Z3r0shin/ambersong/docs/human/hardware-bible/13b-tube-radio.md

## 13.6 The 455 kHz AM IF and AM detector

In SW and AM, the converter (V3, section 13.7) sends its 455 kHz IF through the **first AM IF
transformer** (L11) to the first IF amplifier (V4), the tube the FM path also uses (section 13.4). From
V4 the IF goes through the **second AM IF transformer** (L13) to the **AM detector**: the two diodes
inside V6, a 12AV6. The detector recovers the audio from the IF and also makes the **AVC** voltage, which
sets the gain of V4 and, in AM, of the converter (section 13.1.5).

### 13.6.1 How it is joined

**First AM IF transformer (L11).** One end of its primary (terminal B) is on the converter's plate (V3
pin 5). The other end (terminal P) is on the AM supply, `AM_B`, together with the converter's screen
grids (V3 pin 6). The mode switch's B+ unit (S1D) puts B+ on `AM_B` in SW and AM only (section 13.1.6).
**No capacitor is on `AM_B`.** SAMS shows a 0.002 µF bypass there; this radio has none.

**Into V4.** The secondary of L11 is in series with the secondary of the first FM IF transformer (L10):
one end (terminal G) joins L10's secondary, and the other end (terminal E) is on the **AVC line**. V4's
control grid (pin 1) is at the far end of L10's secondary, so it returns to the AVC line through both
secondaries (section 13.4.1).

**Out of V4.** V4's plate feeds the primary of the second FM IF transformer (L12), then, in series, the
primary of the second AM IF transformer (L13). The far end of L13's primary shares a point with V4's
screen grid (pin 6). The **AM IF screen supply resistor** (R13, 1 kΩ) feeds that point from the B+
filter (`B115_A`, section 13.10), and its bypass capacitor (C29, 0.01 µF) joins it to the chassis. So
L13 and V4 have B+ in every position of the mode switch.

**Detector.** One end of L13's secondary (terminal G) goes to **both diode plates** of V6, pins 5 and 6.
The diodes' cathode is pin 2, which V6's triode shares, and it is on the chassis. The other end of the
secondary (terminal E) is the **detector load point**. From there:

- the detector IF bypass capacitor (C31, 100 pF) goes to the chassis;
- the detector load resistor (R15, 50 kΩ) leads to the **AM audio point**.

**AM audio point.** Three parts leave it: the detector DC return resistor (R16, 1 MΩ) and the audio IF
bypass capacitor (C32, 100 pF), both to the chassis, and the **AVC feed resistor** (R17, 2 MΩ) to the
AVC line. The AM audio goes to the SW and AM contacts of the mode switch's audio unit (S1B), whose common
feeds the top of the radio's volume control (section 13.8).

**AVC line.** It joins five things: the far end of the AVC feed resistor (R17), terminal E of L11's
secondary, one end of the AM loopstick (L7), one side of the AM antenna trimmer (C23A), and the **AVC
bypass capacitor** (C24, 0.05 µF), whose other side is on the chassis. In AM the converter's signal grid
returns to this line through the loopstick (section 13.7).

**Cans.** The cans of L11 and L13 are on the chassis.

How the stage is joined (simplified).

### 13.6.2 Parts

The stage's parts, with their fitted and original values (section 13.1.3):

| Part | Fitted | Original | Notes |
|---|---|---|---|
| First AM IF transformer (L11) | IF can, 455 kHz | factory: AM IF (A); SAMS: 455 kHz | SAMS DCR: primary 22 Ω, secondary 22 Ω. Not retuned. |
| Second AM IF transformer (L13) | IF can, 455 kHz | factory: AM IF (B); SAMS: 455 kHz | SAMS DCR: primary 22 Ω, secondary 20 Ω. Not retuned. Its secondary feeds V6's diodes. |
| AM IF screen supply resistor (R13) | 1 kΩ | same | Feeds the far end of L13's primary and V4's screen. |
| AM IF screen supply bypass capacitor (C29) | 0.01 µF | same | |
| Detector IF bypass capacitor (C31) | 100 pF | same | |
| Detector load resistor (R15) | 50 kΩ | same | |
| Detector DC return resistor (R16) | 1 MΩ | same | |
| Audio IF bypass capacitor (C32) | 100 pF | same | |
| AVC feed resistor (R17) | 2 MΩ | same | |
| AVC bypass capacitor (C24) | 0.05 µF | 0.05 µF (factory and SAMS); SAMS: 50 V | No fitted voltage rating recorded. |
| AM detector (V6's two diodes) | 12AV6, new old stock | 12AV6 | The whole tube is in section 13.8. |
| Mode switch, audio unit (S1B) | one unit of the mode switch | SAMS part M5 | Section 13.1.6. |

For a replacement AM IF transformer, neither original gives what you need: the windings' coupling and
impedance, the pinout, the internal capacitor values, the bandwidth and the mechanical fit are all
unrecorded. The tuned frequency is 455 kHz.

### 13.6.3 How to check it

- **Coil resistance.** The parts table gives the SAMS DCR figures for L11 and L13, which describe the
  original parts. A DCR is a check for an open winding, not a measure of inductance or tuning.
- **Shared with FM.** An open secondary in L11, or an open primary in L13, also stops V4 on FM
  (section 13.4.4).
- **Tuning.** The AM IF transformers were not retuned when the FM path was tuned (section 13.1.1).
- **Detector.** V6's diode plates are pins 5 and 6, both on the same end of L13's secondary; the cathode,
  pin 2, is on the chassis.

## 13.7 AM and SW input, converter (V3, 12BE6) and the SW and AM local oscillator

V3 is a **pentagrid converter**: one tube with five grids that is both the mixer and the local oscillator
for AM and SW. Its oscillator section runs on its first grid and cathode. The station enters on its third
grid, the **signal grid**. The IF, 455 kHz, leaves from its plate into the first AM IF transformer (L11).
The mode switch picks the input coil and the oscillator coil for each band. The input coil is the
ferrite **loopstick** (a ferrite rod carrying an antenna winding) in AM, and the SW antenna coil in SW.
V3 takes its B+ from `AM_B`, so it works only in SW and AM.

**The external SW antenna terminal (J2) is not fitted; the internal loopstick antenna (L7) is.** Every
other input part is fitted too: the SW coupling capacitor (C21), the SW antenna coil (L6) and its trimmer
(C22A), and the loopstick's trimmer (C23A).

SAMS gives the bands as 540 to 1620 kHz for AM (the loopstick) and 3.5 to 9 MHz for SW (the SW antenna
coil).

The stage has its own **trimmers** and **padders**, the small capacitors that set its alignment and
tracking (section 13.1.3).

### 13.7.1 How it is joined

**SW input.** The SW antenna coupling capacitor (C21) has one lead where the SW antenna terminal (J2)
would be; nothing else is on that lead. Its other lead goes to one end of the primary of the SW antenna
coil (L6); the other end of that primary is on the chassis. One end of L6's secondary is the **SW RF
point**, which the SW antenna trimmer (C22A) joins to the chassis, and which goes to the SW contact of the
mode switch's RF unit (S1C). The other end of the secondary is on the chassis.

**AM input.** One end of the loopstick (L7) is the **AM RF point**, which goes to the AM contact of S1C.
The other end is on the AVC line (section 13.6). The AM antenna trimmer (C23A) sits across the loopstick,
from the AVC line to the AM RF point.

**Signal grid.** The common of S1C, the AM/SW RF tuning section (VC3, whose other side is on the
chassis) and V3's signal grid (pin 7) are one point. In SW, S1C puts the SW RF point on it; in AM, the AM
RF point; in FM and FM-AFC, nothing. So in AM the grid returns to the AVC line through the loopstick,
and in SW it returns to the chassis through the SW coil's secondary.

**Plate and screens.** The plate (pin 5) goes to the primary of the first AM IF transformer (L11). The
screen grids (pin 6) are on `AM_B` with the other end of that primary. No capacitor is on `AM_B`
(section 13.6.1).

**Oscillator grid.** The oscillator grid (pin 1) goes to the chassis through the oscillator grid leak
resistor (R11, 20 kΩ; grid leak: section 13.3.1). The grid also goes through the oscillator feedback
capacitor (C25, 100 pF) to the **oscillator tuning point**.

**Oscillator tuning point.** It joins C25, the AM/SW oscillator tuning section (VC4, whose other side is
on the chassis) and the common of the mode switch's oscillator tank unit (S1F).

- **In SW**, S1F goes through the SW oscillator padder (C26, 0.003 µF) to the top of the SW oscillator
  coil (L9). The SW oscillator trimmer (C22B) joins that top to the chassis.
- **In AM**, S1F goes to a point that the AM oscillator trimmer (C23B) joins to the chassis. From there
  the AM oscillator padder (C27, 350 pF) leads to the top of the AM oscillator coil (L8).

The bottoms of both oscillator coils are on the chassis.

**Cathode.** The cathode (pin 2) goes only to the common of the mode switch's oscillator feedback unit
(S1G). In SW, S1G puts it on the tap of the SW oscillator coil (L9); in AM, on the tap of the AM
oscillator coil (L8). In FM and FM-AFC the cathode is connected to nothing, and the tube has no B+.

**Heater.** The heater is on pins 3 and 4, in the series string (section 13.9).

How the stage is joined (simplified).

### 13.7.2 V3's pins

The table gives each of V3's pins and what it is joined to.

| Pin | What it is | Joined to |
|---|---|---|
| 1 | oscillator grid (grid 1) | grid leak (R11) to chassis; feedback capacitor (C25) to the oscillator tuning point |
| 2 | cathode | oscillator feedback unit (S1G) only: SW oscillator coil's tap in SW, AM oscillator coil's tap in AM |
| 3 | heater | heater string, toward the FM RF tube's heater through a heater choke (L16) |
| 4 | heater | heater string, from the first IF tube's heater; bypass capacitor (C47) to chassis |
| 5 | plate | primary of the first AM IF transformer (L11) |
| 6 | screen grids (grids 2 and 4) | `AM_B`, with the other end of L11's primary |
| 7 | signal grid (grid 3) | RF unit's common (S1C) and the AM/SW RF tuning section (VC3) |

### 13.7.3 Parts

The stage's parts, with their fitted and original values (section 13.1.3):

| Part | Fitted | Original | Notes |
|---|---|---|---|
| Converter tube (V3) | 12BE6 | 12BE6 | |
| SW antenna terminal (J2) | **absent** | factory: antenna terminal with a series coupling capacitor; SAMS: a terminal, no rating | The external SW antenna terminal (J2) is not fitted; the internal loopstick antenna (L7) is. |
| SW antenna coupling capacitor (C21) | 450 pF | same | Several listed substitutes, Sprague among them, are 470 pF. The listed substitutes are DC-rated and give no safety class for an antenna input on a mains-connected chassis. |
| SW antenna coil (L6) | two-winding coil | factory: two-winding SW matching coil; SAMS: DCR 0.3 Ω each winding, band 3.5–9 MHz | Inductance not given. |
| SW antenna trimmer (C22A) | trimmer | no value in either original | Range and dielectric not specified. Part of the band alignment: do not choose one by appearance. |
| AM loopstick (L7) | loopstick | factory: ferrite bar with antenna winding; SAMS: DCR 0.6 Ω, band 540–1620 kHz | Inductance not given. |
| AM antenna trimmer (C23A) | trimmer | no value in either original | As the SW antenna trimmer. |
| AM/SW RF tuning section (VC3) | section of the four-section tuning capacitor | part of SAMS's tuning assembly M2; no range given | Serves both SW and AM. Turns with the other three sections of the tuning capacitor. |
| Mode switch, RF unit (S1C) | one unit of the mode switch | SAMS part M5 | Section 13.1.6. |
| Oscillator grid leak resistor (R11) | 20 kΩ | same | |
| Oscillator feedback capacitor (C25) | 100 pF | same | |
| AM/SW oscillator tuning section (VC4) | section of the four-section tuning capacitor | part of SAMS's tuning assembly M2; no range given | Serves both SW and AM. |
| Mode switch, oscillator tank unit (S1F) | one unit of the mode switch | SAMS part M5 | Section 13.1.6. |
| SW oscillator padder (C26) | 0.003 µF | 0.003 µF (3000 pF), SAMS: ±5 % | A stable, low-loss RF capacitor. The listed substitute is silvered mica, 500 V. The fitted part's type and rating are not recorded. |
| SW oscillator trimmer (C22B) | trimmer | no value in either original | As the SW antenna trimmer. |
| SW oscillator coil (L9) | tapped coil | factory: tapped oscillator coil; SAMS: DCR 0.3 Ω and 0.1 Ω sections | |
| AM oscillator padder (C27) | 350 pF | same | **Do not round it to 330 pF**: the padder sets the tracking. Sprague 5GA-T35 is 350 pF; Aerovox DI-330 and other listed substitutes are not. |
| AM oscillator trimmer (C23B) | trimmer | no value in either original | As the SW antenna trimmer. |
| AM oscillator coil (L8) | tapped coil | factory: tapped oscillator coil; SAMS: DCR 4.6 Ω and 0.9 Ω sections | SAMS: on the listed Merit, Miller and Stancor substitutes, ignore the extra tap. |
| Mode switch, oscillator feedback unit (S1G) | one unit of the mode switch | SAMS part M5 | Section 13.1.6. |

The AVC bypass capacitor (C24) is in section 13.6.

### 13.7.4 How to check it

- **Coil resistance.** SAMS gives these DCRs for the original coils: the SW antenna coil (L6) 0.3 Ω each
  winding; the loopstick (L7) 0.6 Ω; the AM oscillator coil (L8) 4.6 Ω and 0.9 Ω for its two sections;
  the SW oscillator coil (L9) 0.3 Ω and 0.1 Ω. A DCR finds an open winding; it does not measure
  inductance.
- **The mode switch.** With the cord out, the mode switch's RF, oscillator tank and oscillator feedback
  units (S1C, S1F, S1G) each join their common to their SW contact in SW and their AM contact in AM.
  In FM and FM-AFC they join it to nothing (section 13.1.6).
- **Alignment.** The AM and SW path was not retuned when the FM path was (section 13.1.1). No alignment
  figures for the trimmers are recorded.

## 13.8 The audio amplifier (V6, 12AV6, and V7, 50C5), tone switch and output transformer

The audio picked by the mode switch's audio unit (S1B) reaches the top of the radio's **volume
control** (R1). Its wiper drives the triode inside V6, the **first audio amplifier**, which raises the
audio's voltage. V7, a 50C5 **beam power tube** (a tube built to deliver power to a load), is the
**output stage**: it drives the primary of the **output transformer** (T1). A **tone switch** can join one
or two small capacitors from V6's plate to the chassis, which takes some of the treble away. V6 and V7
have B+ in every position of the mode switch.

### 13.8.1 How it is joined

**Volume control (R1).** Its top (pin 1) comes from the common of the audio unit (S1B). Its bottom
(pin 3) is on the chassis. Its wiper (pin 2) goes through the grid coupling capacitor (C38, 0.01 µF) to
V6's triode grid (pin 1). The audio grid leak resistor (R25, 2 MΩ) joins that grid to the chassis.

**V6's triode.** The cathode (pin 2), shared with the AM detector diodes, is on the chassis. The plate
(pin 7) is fed from the B+ filter (`B115_A`) through the audio plate load resistor (R26, 250 kΩ). Three
more parts leave the plate: the audio plate shunt capacitor (C39, 100 pF) to the chassis, the output
coupling capacitor (C42, 0.01 µF) to V7's grid, and the first tone capacitor (C40).

**Tone switch.** The first tone capacitor (C40, 0.002 µF) runs from V6's plate to a point the tone switch
calls LOW. The second tone capacitor (C41, 0.002 µF) runs from LOW to a point called MID. The tone
unit's common is on the chassis. The table shows what each tone position switches in:

| Tone position | What it switches in, from V6's plate to the chassis |
|---|---|
| H (high) | nothing: the H contact is connected to nothing |
| M (medium) | C40 and C41 in series: 0.001 µF |
| L (low) | C40 alone: 0.002 µF |

The factory drawing and SAMS agree on this. SAMS numbers the switch's lugs 13 for the common, 2 for OFF,
3 for H, 4 for M and 5 for L. The letters H, M and L above are the drawing's; no record maps them to the
physical lugs.

**V7.** The control grid (pin 2) takes the audio from C42 and returns to the chassis through the output
grid leak resistor (R27, 500 kΩ). The cathode (pin 1) goes to the chassis through the output cathode
resistor (R28, 150 Ω 1 W); nothing else is on the cathode. The screen grid (pin 6) is on the B+ filter
(`B115_A`). The plate (pin 7) goes to one end of the output transformer's primary (terminal P) and to the
primary shunt capacitor (C43, 0.0047 µF). **Nothing is wired to pin 5.**

**Output transformer (T1).** Its primary has **two terminals and no tap**. Terminal P is on V7's plate.
Terminal B is on `B130`, the first filtered point of the B+ supply (section 13.10), and C43 sits across
the two. The secondary's two leads leave the radio for the ADC (section 13.11).

**SP1 and SP2** are the radio's original speakers as drawn by the factory, in series across the
secondary. In this machine the radio's output feeds the 7.5 Ω load and the ADC, not speakers.

**Heaters.** V6's heater is on pins 3 and 4, V7's on pins 3 and 4, both in the series string
(section 13.9).

How the stage is joined (simplified).

### 13.8.2 V6's and V7's pins

The table gives each pin of both tubes and what it is joined to.

| Pin | V6, 12AV6 | Joined to | V7, 50C5 | Joined to |
|---|---|---|---|---|
| 1 | triode grid | grid coupling capacitor (C38) from the volume wiper; grid leak (R25) to chassis | cathode | output cathode resistor (R28) to chassis |
| 2 | cathode, shared by the triode and both diodes | chassis | control grid | output coupling capacitor (C42); grid leak (R27) to chassis |
| 3 | heater | heater string, toward the first IF tube's heater | heater | heater string, toward the limiter's heater |
| 4 | heater | heater string, from the limiter's heater | heater | the fused live: the start of the heater string |
| 5 | diode plate | second AM IF transformer's secondary (L13), terminal G | second control-grid pin | nothing |
| 6 | diode plate | the same point as pin 5 | screen grid | B+ filter (`B115_A`) |
| 7 | triode plate | plate load (R26) from `B115_A`; C39, C42, C40 | plate | output transformer primary, terminal P; C43 |

The 50C5's published ratings: plate at most 150 V, screen at most 130 V, plate dissipation 7 W, screen
dissipation 1.4 W.
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
