Z3r0shin/ambersong/docs/human/hardware-bible/A-datasheet-limits.md

# Appendix A. Datasheet facts used in this machine

This appendix gathers the makers' figures that matter for this machine: pinouts, limits, addresses and
ratings, part by part. Only the facts the machine uses are here. You need it when you replace a part,
check a reading against a limit, or adapt the design to other parts. The chapters tell you what each
part does; abbreviations are explained in the glossary.
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
