Z3r0shin/ambersong/hardware/STLs/AUDIO - Passive Radiator - Holder.stl

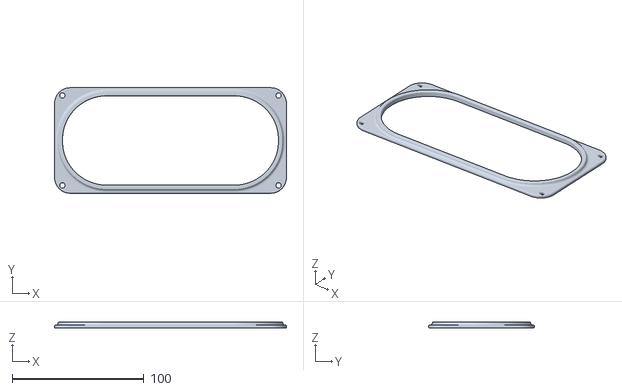
[picture p21: CAD file, 2026-09-28]
hardware/STLs/AUDIO - Passive Radiator - Holder.stl
176.2 x 80.2 x 4.80
