Z3r0shin/ambersong/hardware/STLs/IN - Electronics - LEDITRON Bus Case Bottom.stl

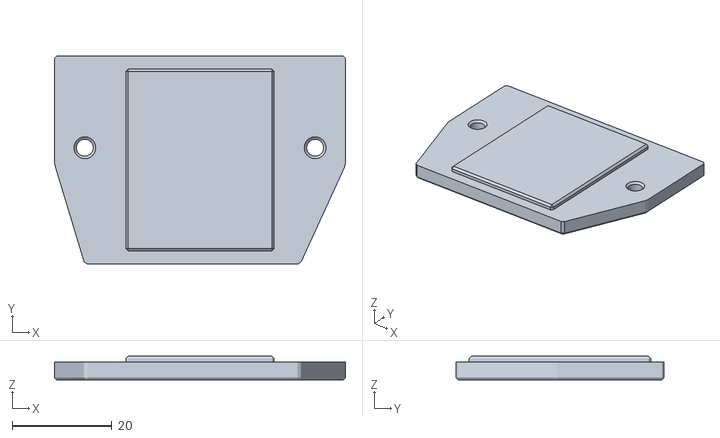
[picture p22: CAD file, 2026-09-28]
hardware/STLs/IN - Electronics - LEDITRON Bus Case Bottom.stl
58.4 x 41.8 x 4.80
