Z3r0shin/ambersong/hardware/STLs/IN - Electronics - Power Detect Case BOTTOM.stl

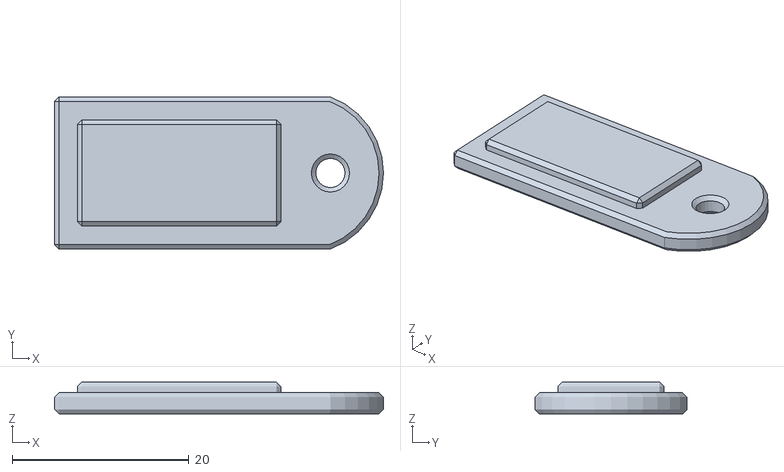
[picture p23: CAD file, 2026-09-28]
hardware/STLs/IN - Electronics - Power Detect Case BOTTOM.stl
37.2 x 17.2 x 3.60
