Z3r0shin/ambersong/hardware/STLs/FRONT - Panel Anchors - Outsidemost.stl

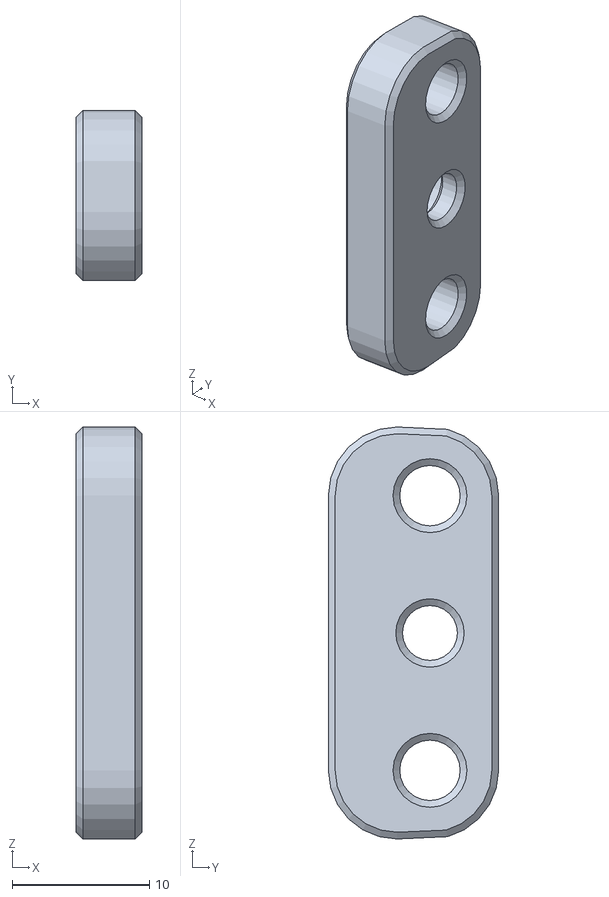
[picture p24: CAD file, 2026-09-28]
hardware/STLs/FRONT - Panel Anchors - Outsidemost.stl
4.80 x 12.4 x 30.0
