Z3r0shin/ambersong/hardware/STLs/IN - Electronics - RDA5807M - Cage Holder.stl

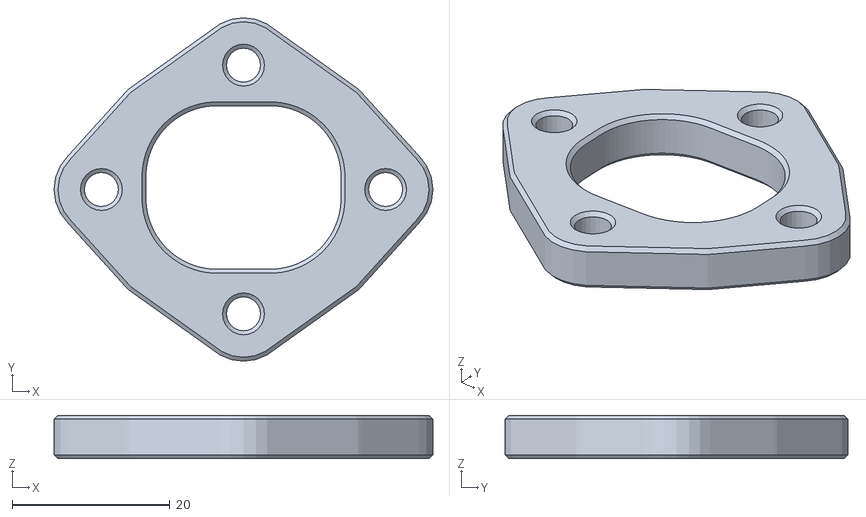
[picture p25: CAD file, 2026-09-28]
hardware/STLs/IN - Electronics - RDA5807M - Cage Holder.stl
48.0 x 43.5 x 5.50
