Z3r0shin/ambersong/hardware/STLs/IN - Electronics - Box Fan LM7812 Case Top.stl

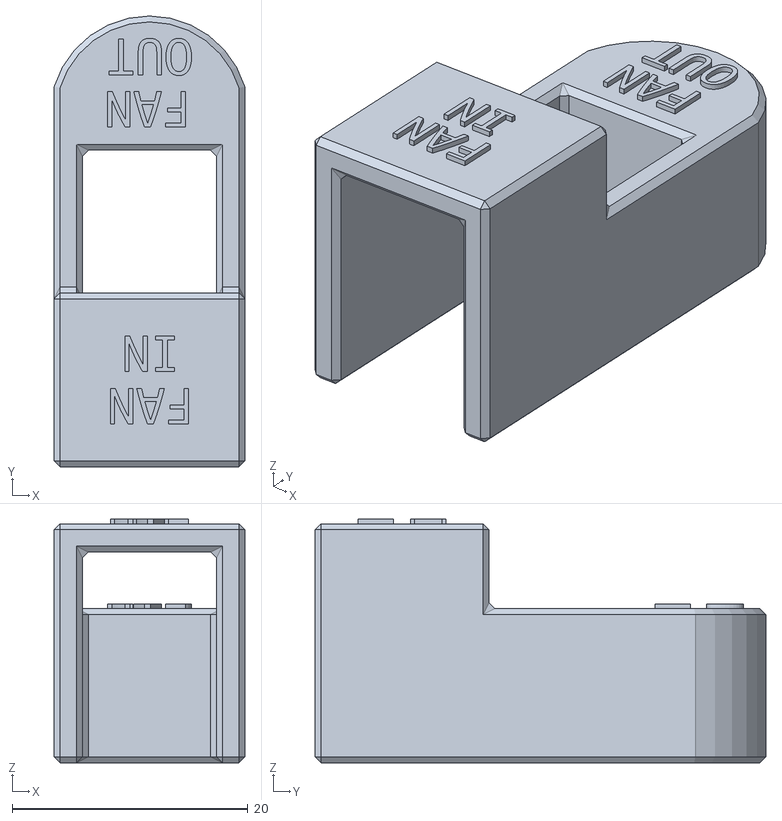
[picture p26: CAD file, 2026-09-28]
hardware/STLs/IN - Electronics - Box Fan LM7812 Case Top.stl
16.2 x 38.3 x 20.7
