Z3r0shin/ambersong/hardware/STLs/BACK - Electronics - BNC Antenna Interface.stl

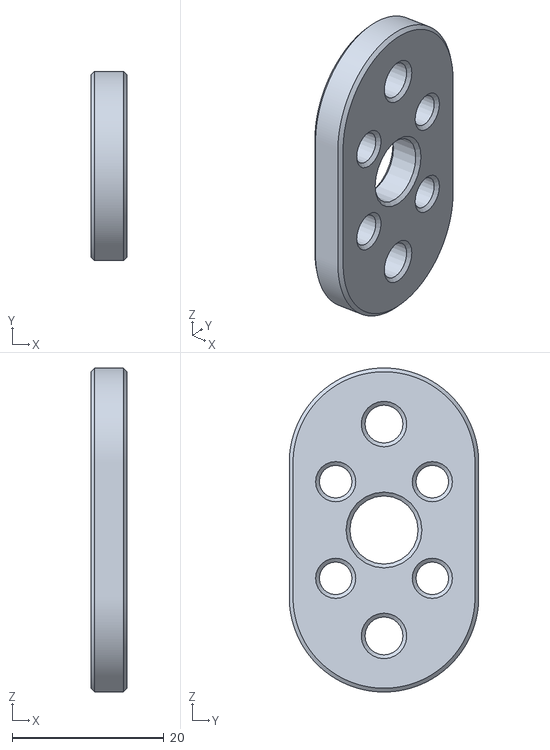
[picture p27: CAD file, 2026-09-28]
hardware/STLs/BACK - Electronics - BNC Antenna Interface.stl
4.80 x 25.0 x 42.7
