Z3r0shin/ambersong/hardware/STLs/LEDITRON - Front Case.stl

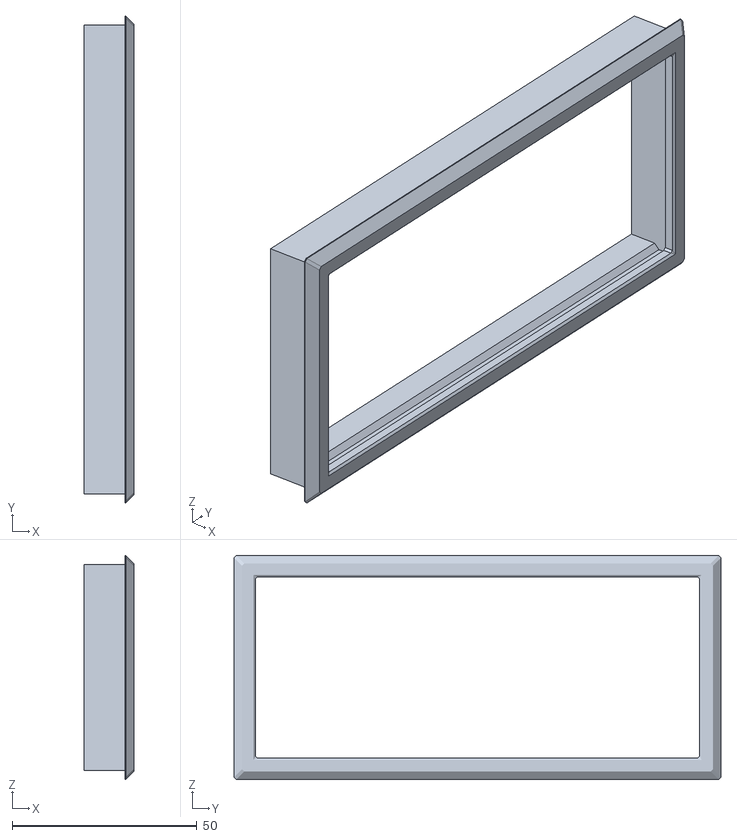
[picture p28: CAD file, 2026-09-28]
hardware/STLs/LEDITRON - Front Case.stl
13.5 x 131.8 x 60.7
