Z3r0shin/ambersong/hardware/STLs/IN - Electronics - Box Fan LM7812 Case Bottom.stl

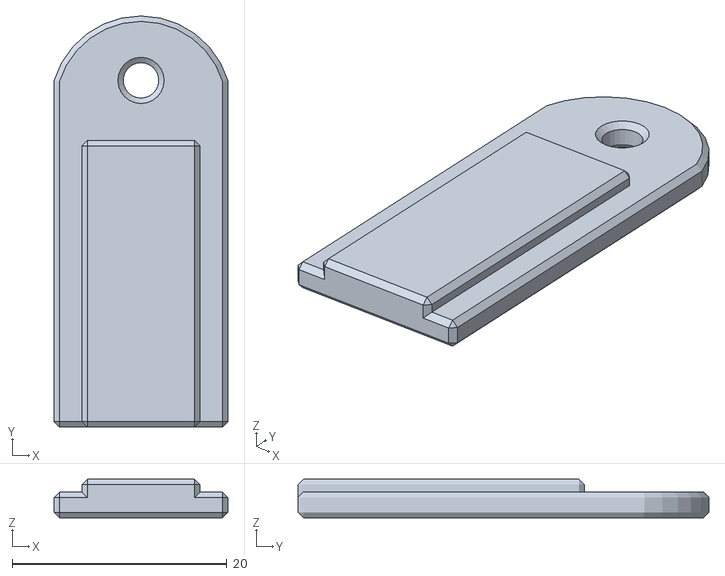
[picture p29: CAD file, 2026-09-28]
hardware/STLs/IN - Electronics - Box Fan LM7812 Case Bottom.stl
16.2 x 38.3 x 3.60
