Z3r0shin/ambersong/hardware/STLs/IN - Electronics - LEDITRON Back.stl

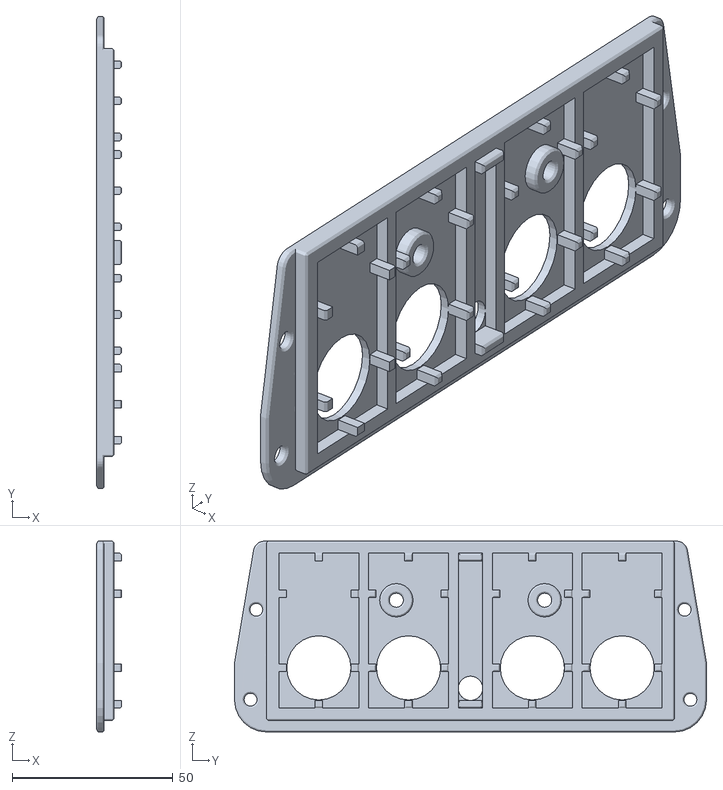
[picture p30: CAD file, 2026-09-28]
hardware/STLs/IN - Electronics - LEDITRON Back.stl
7.81 x 147.0 x 59.5
