Z3r0shin/ambersong/hardware/STLs/LEDITRON - Digit.stl

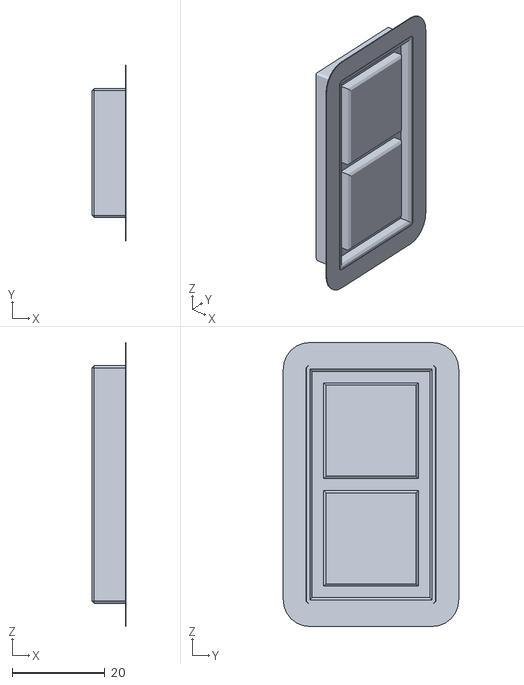
[picture p31: CAD file, 2026-09-28]
hardware/STLs/LEDITRON - Digit.stl
7.40 x 37.8 x 61.1
