Z3r0shin/ambersong/hardware/STLs/AUDIO - Passive Radiator - TPU Membrane.stl

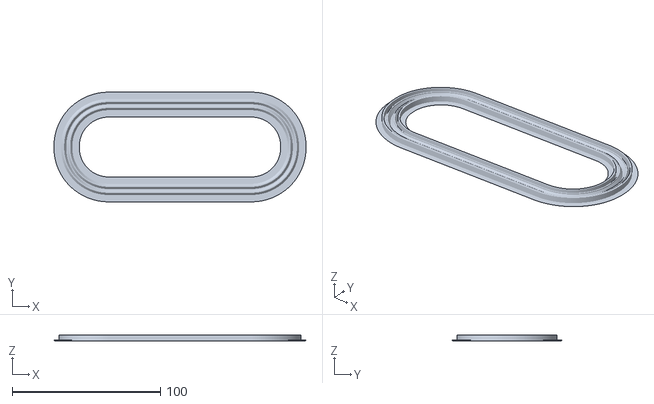
[picture p32: CAD file, 2026-09-28]
hardware/STLs/AUDIO - Passive Radiator - TPU Membrane.stl
170.0 x 74.0 x 4.00
