Z3r0shin/ambersong/hardware/STLs/LEDITRON - Glass Spacer.stl

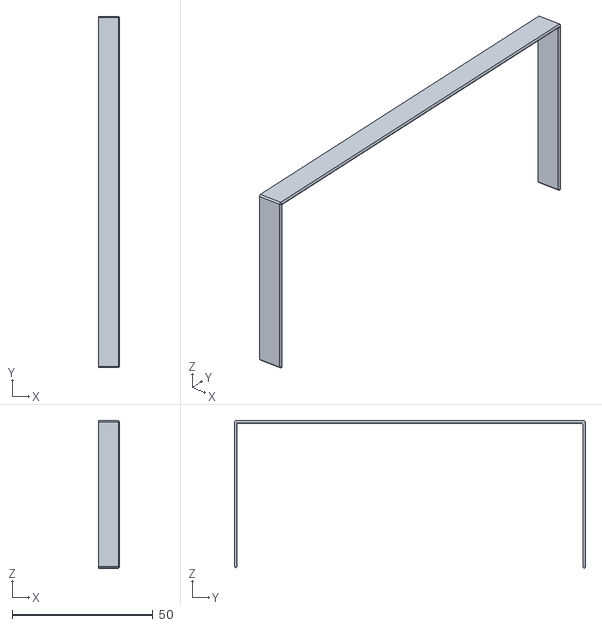
[picture p33: CAD file, 2026-09-28]
hardware/STLs/LEDITRON - Glass Spacer.stl
7.51 x 124.6 x 52.5
