Z3r0shin/ambersong/hardware/STLs/IN - Electronics - Audio MCU Case BOTTOM.stl

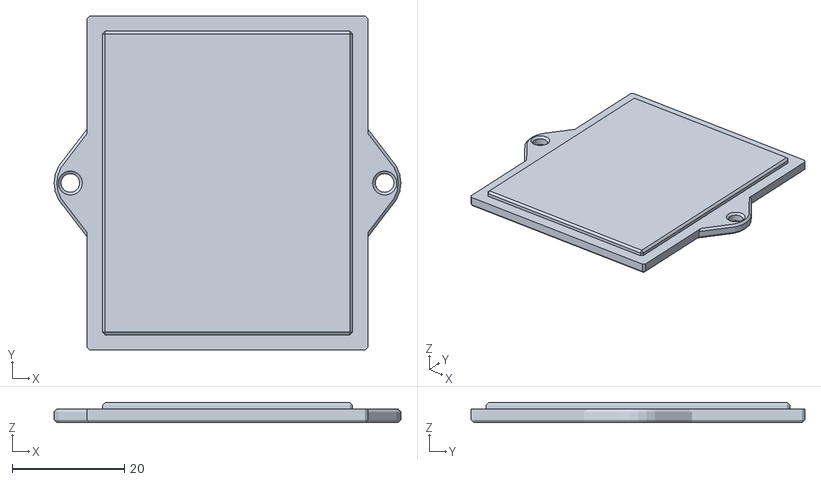
[picture p34: CAD file, 2026-09-28]
hardware/STLs/IN - Electronics - Audio MCU Case BOTTOM.stl
61.7 x 59.4 x 3.60
