Z3r0shin/ambersong/hardware/STLs/IN - Electronics - PCM5102A DAC Case Bottom.stl

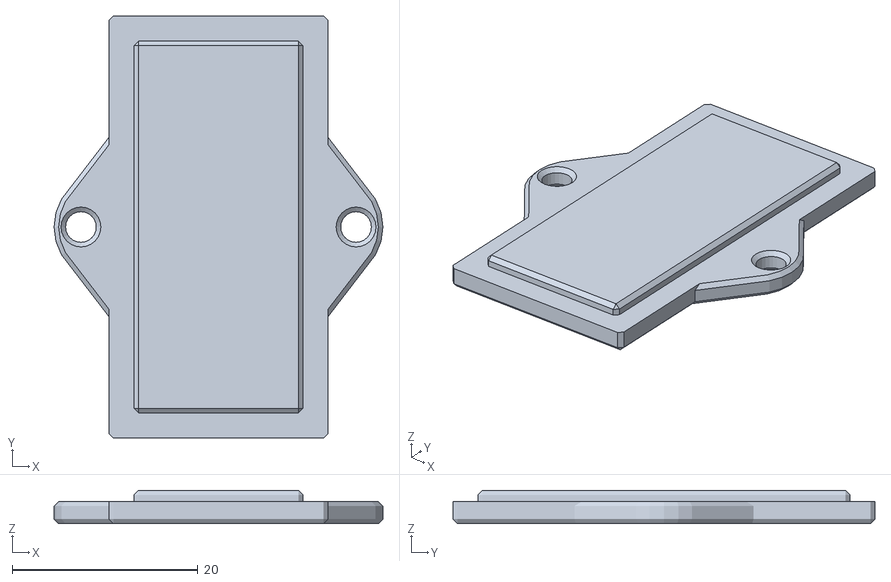
[picture p35: CAD file, 2026-09-28]
hardware/STLs/IN - Electronics - PCM5102A DAC Case Bottom.stl
35.4 x 45.4 x 3.60
