Z3r0shin/ambersong/hardware/STLs/IN - Electronics - 5V PSU Case Bottom.stl

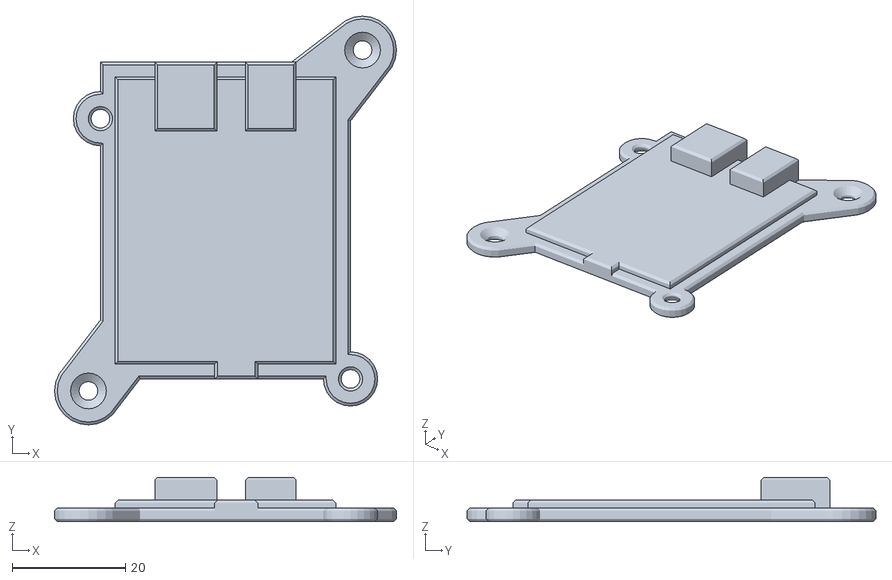
[picture p36: CAD file, 2026-09-28]
hardware/STLs/IN - Electronics - 5V PSU Case Bottom.stl
60.4 x 72.2 x 7.80
