Z3r0shin/ambersong/hardware/STLs/IN - Electronics - RDA5807M - Bottom.stl

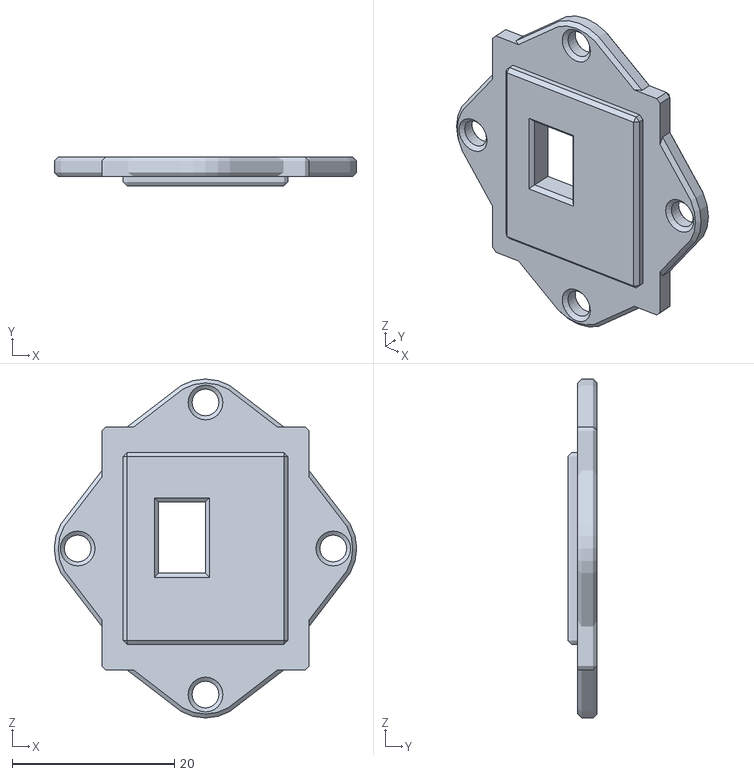
[picture p37: CAD file, 2026-09-28]
hardware/STLs/IN - Electronics - RDA5807M - Bottom.stl
37.3 x 3.60 x 41.8
