Z3r0shin/ambersong/hardware/STLs/IN - Electronics - LEDITRON Bus Case TOP.stl

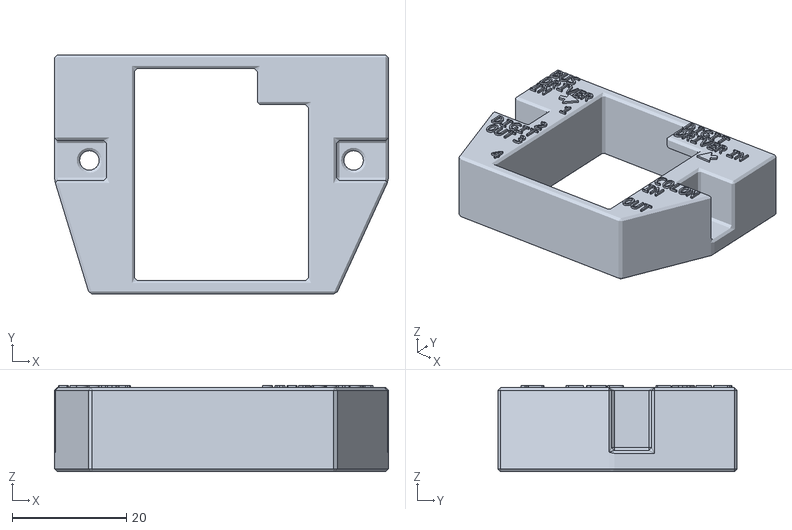
[picture p38: CAD file, 2026-09-28]
hardware/STLs/IN - Electronics - LEDITRON Bus Case TOP.stl
58.4 x 41.8 x 15.1
