Z3r0shin/ambersong/hardware/STLs/IN - Electronics - Stepper Driver ULN2003A Case - Top.stl

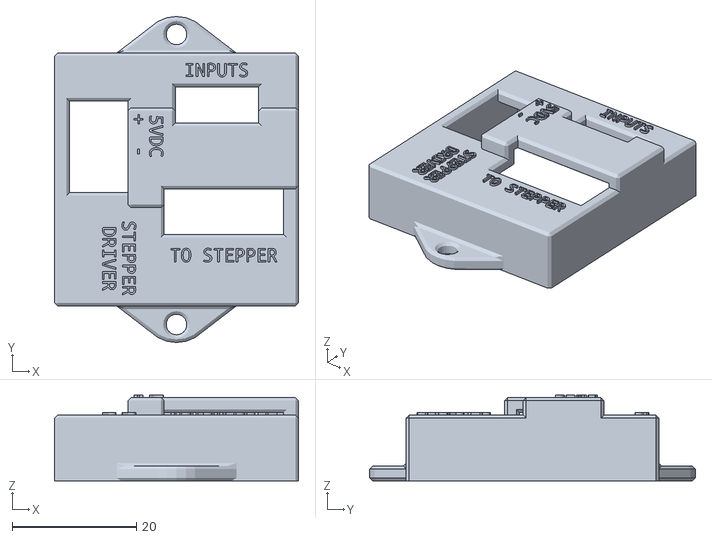
[picture p39: CAD file, 2026-09-28]
hardware/STLs/IN - Electronics - Stepper Driver ULN2003A Case - Top.stl
39.2 x 52.4 x 13.8
