Z3r0shin/ambersong/hardware/STLs/FRONT - FM Dial - Stepper Needle and Magnet Holder.stl

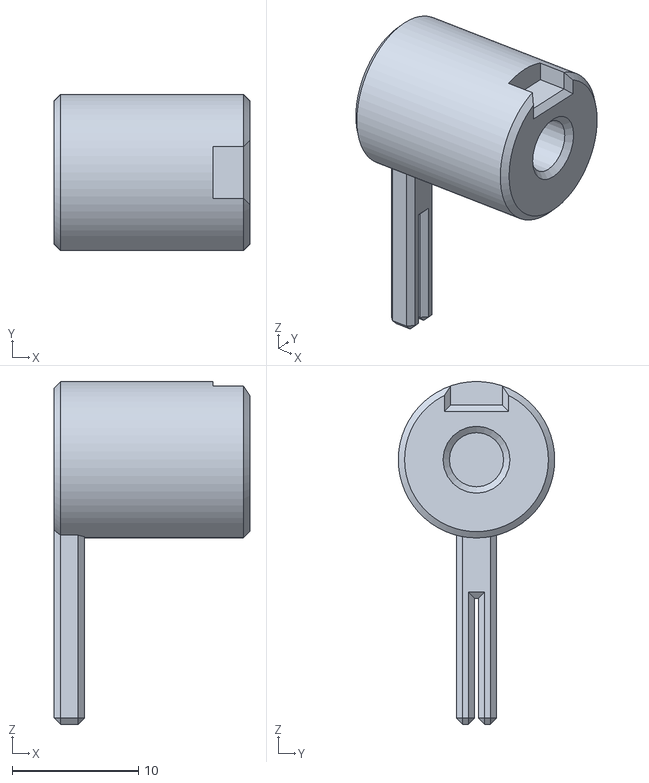
[picture p40: CAD file, 2026-09-28]
hardware/STLs/FRONT - FM Dial - Stepper Needle and Magnet Holder.stl
15.5 x 12.4 x 27.2
