Z3r0shin/ambersong/hardware/STLs/IN - Electronics - AS5600 Case - Top.stl

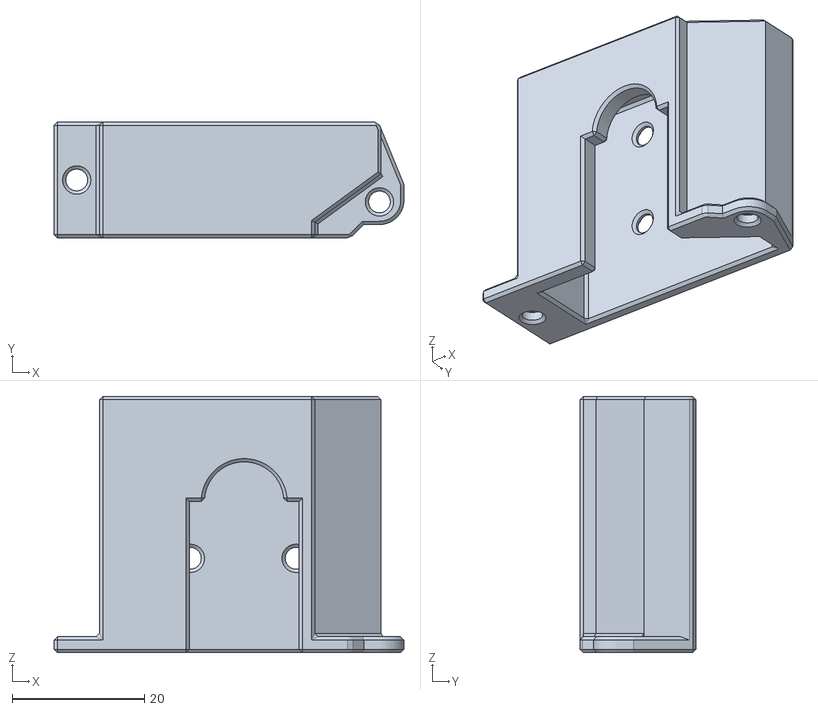
[picture p41: CAD file, 2026-09-28]
hardware/STLs/IN - Electronics - AS5600 Case - Top.stl
53.0 x 17.5 x 38.8
