Z3r0shin/ambersong/hardware/STLs/AUDIO - Passive Radiator - Membrane Weight.stl

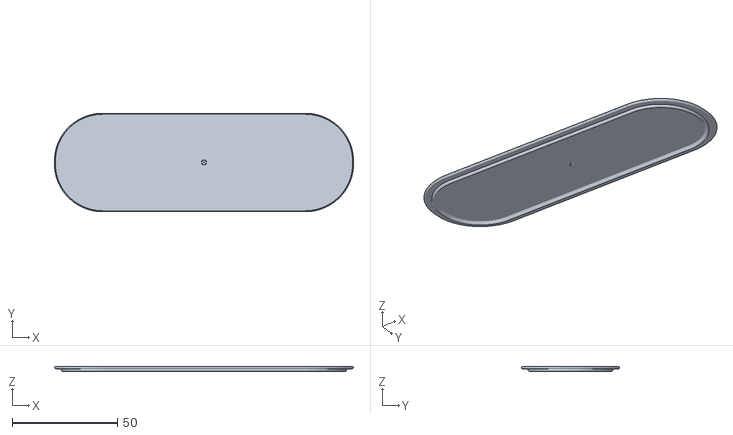
[picture p42: CAD file, 2026-09-28]
hardware/STLs/AUDIO - Passive Radiator - Membrane Weight.stl
142.3 x 46.8 x 2.40
