Z3r0shin/ambersong/hardware/STLs/IN - Electronics - PCM1802 ADC Case BOTTOM.stl

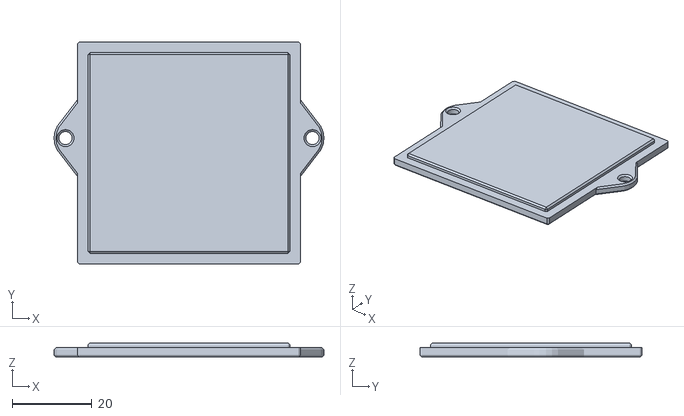
[picture p43: CAD file, 2026-09-28]
hardware/STLs/IN - Electronics - PCM1802 ADC Case BOTTOM.stl
67.9 x 55.9 x 3.60
