Z3r0shin/ambersong/hardware/STLs/IN - Electronics - Stepper Driver ULN2003A Case - Bottom.stl

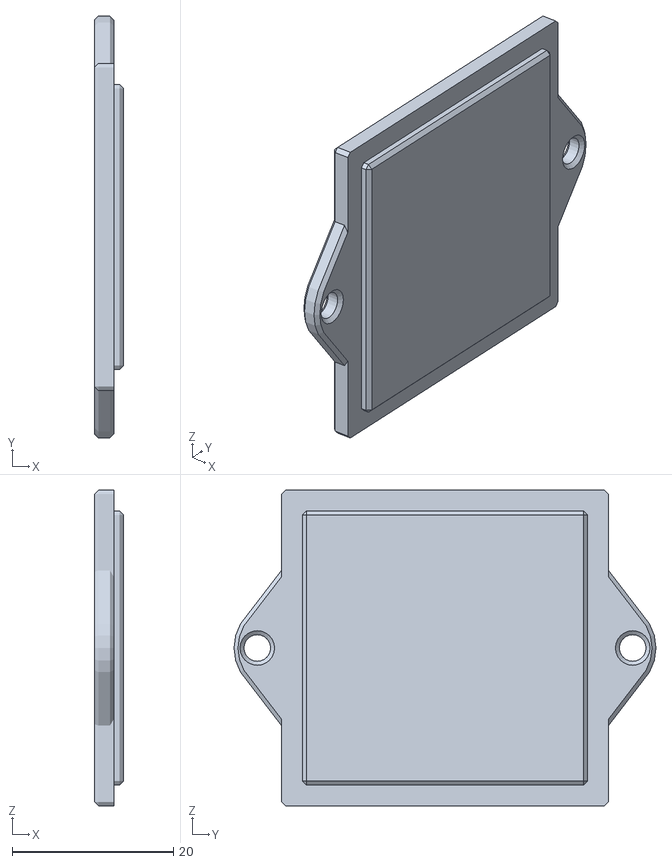
[picture p44: CAD file, 2026-09-28]
hardware/STLs/IN - Electronics - Stepper Driver ULN2003A Case - Bottom.stl
3.60 x 52.4 x 39.2
