Z3r0shin/ambersong/hardware/STLs/IN - Electronics - Audio Listener Case BOTTOM.stl

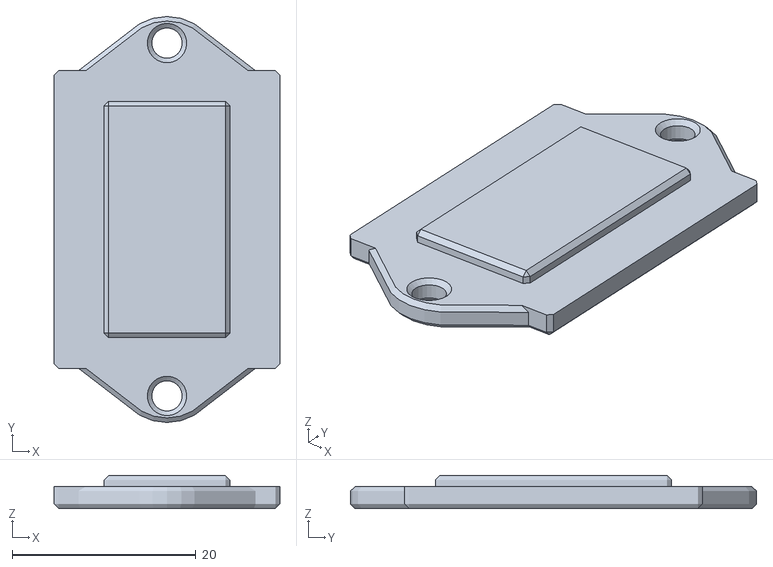
[picture p45: CAD file, 2026-09-28]
hardware/STLs/IN - Electronics - Audio Listener Case BOTTOM.stl
24.5 x 44.2 x 3.60
