Z3r0shin/ambersong/hardware/STLs/IN - Electronics - Digit Drivers Case BOTTOM.stl

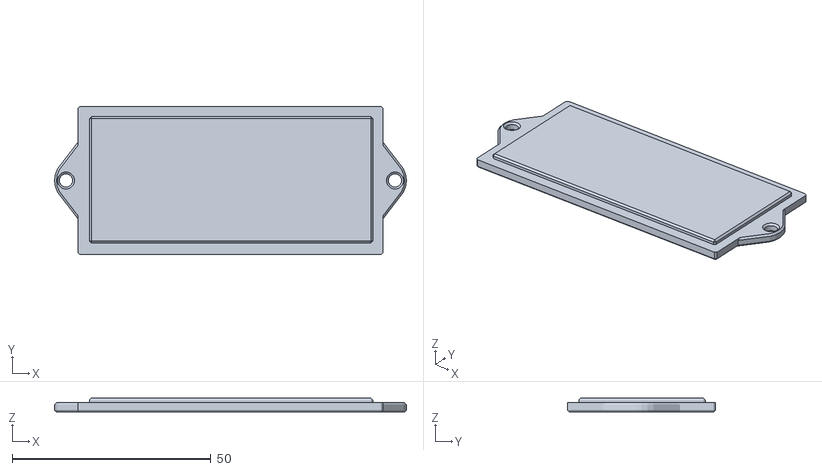
[picture p46: CAD file, 2026-09-28]
hardware/STLs/IN - Electronics - Digit Drivers Case BOTTOM.stl
88.6 x 37.3 x 3.60
