Z3r0shin/ambersong/hardware/STLs/IN - Electronics - Audio Listener Case TOP.stl

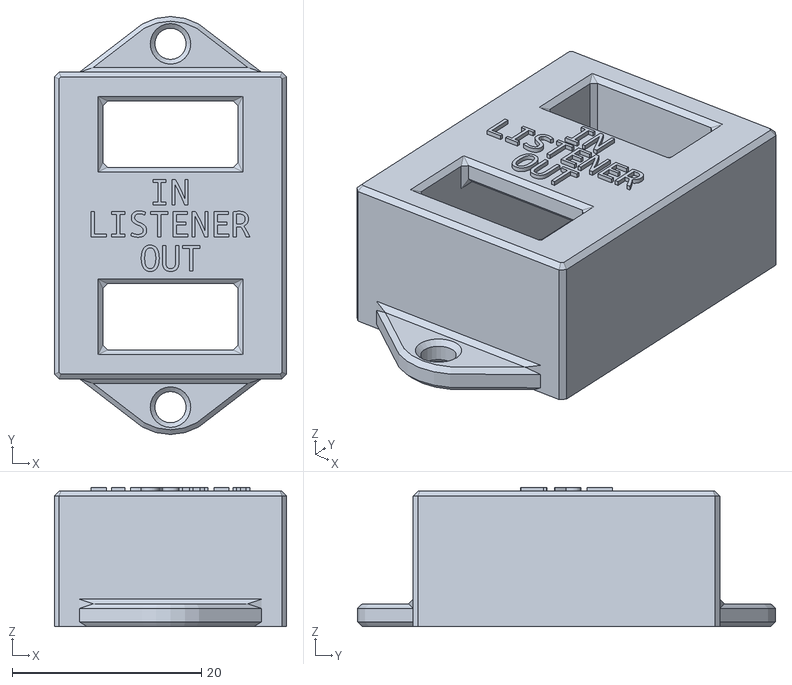
[picture p47: CAD file, 2026-09-28]
hardware/STLs/IN - Electronics - Audio Listener Case TOP.stl
24.6 x 44.2 x 14.7
