Z3r0shin/ambersong/hardware/STLs/LEDITRON - Colon - Blanket.stl

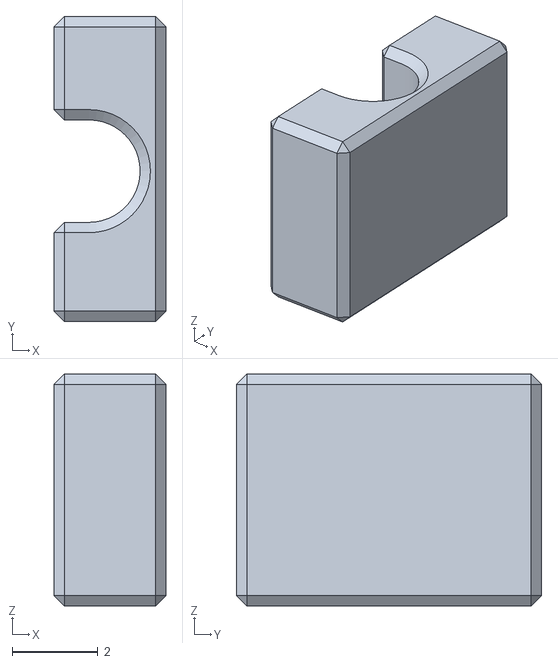
[picture p48: CAD file, 2026-09-28]
hardware/STLs/LEDITRON - Colon - Blanket.stl
2.60 x 7.10 x 5.40
