Z3r0shin/ambersong/hardware/STLs/IN - Electronics - Digit Drivers Case TOP.stl

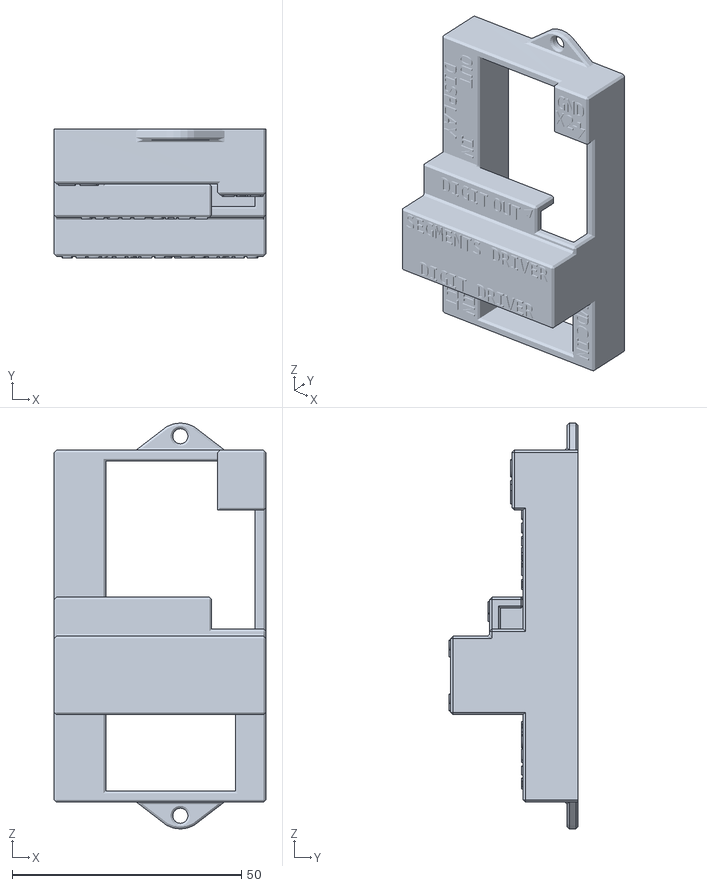
[picture p49: CAD file, 2026-09-28]
hardware/STLs/IN - Electronics - Digit Drivers Case TOP.stl
46.2 x 28.2 x 88.6
