Z3r0shin/ambersong/hardware/STLs/BACK - Fan Exhaust.stl

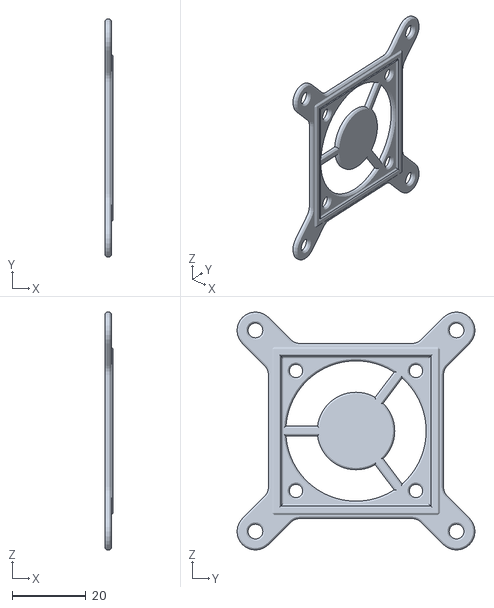
[picture p50: CAD file, 2026-09-28]
hardware/STLs/BACK - Fan Exhaust.stl
2.29 x 64.5 x 64.5
