Z3r0shin/ambersong/hardware/STLs/FRONT - FM Dial - Back.stl

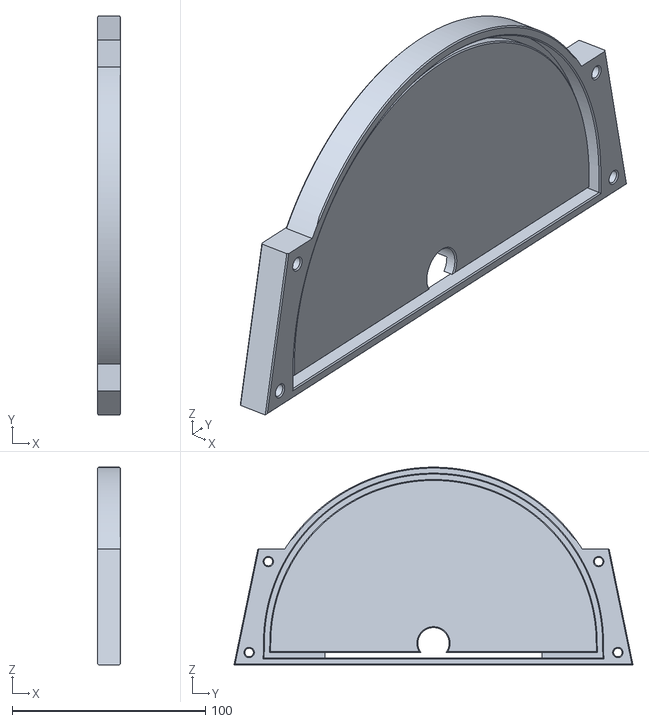
[picture p51: CAD file, 2026-09-28]
hardware/STLs/FRONT - FM Dial - Back.stl
12.0 x 206.7 x 102.4
