Z3r0shin/ambersong/hardware/STLs/IN - Electronics - DS3231 RTC Case BOTTOM.stl

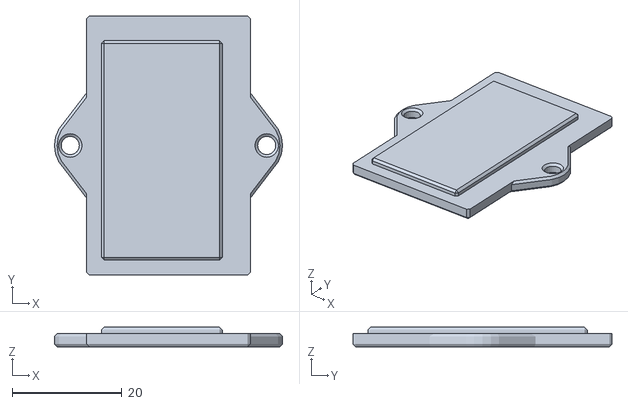
[picture p52: CAD file, 2026-09-28]
hardware/STLs/IN - Electronics - DS3231 RTC Case BOTTOM.stl
41.6 x 47.2 x 3.60
