Z3r0shin/ambersong/hardware/STLs/FRONT - FM Dial - Cover.stl

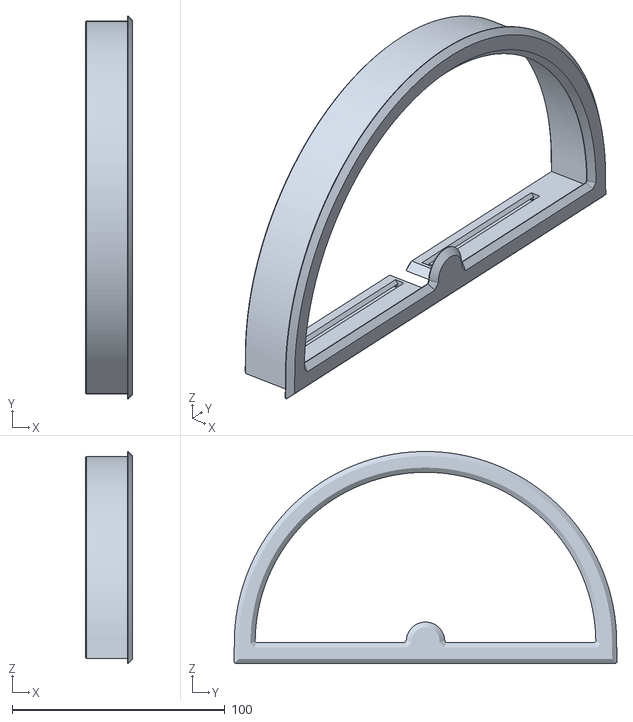
[picture p53: CAD file, 2026-09-28]
hardware/STLs/FRONT - FM Dial - Cover.stl
22.3 x 179.9 x 99.6
