Z3r0shin/ambersong/hardware/STLs/IN - Electronics - Bluetooth LED Holder.stl

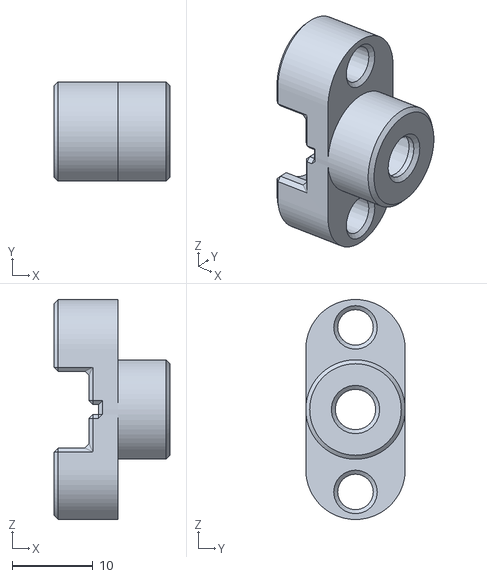
[picture p54: CAD file, 2026-09-28]
hardware/STLs/IN - Electronics - Bluetooth LED Holder.stl
14.3 x 12.3 x 27.2
