Z3r0shin/ambersong/hardware/STLs/IN - Electronics - PCM1802 ADC Case TOP.stl

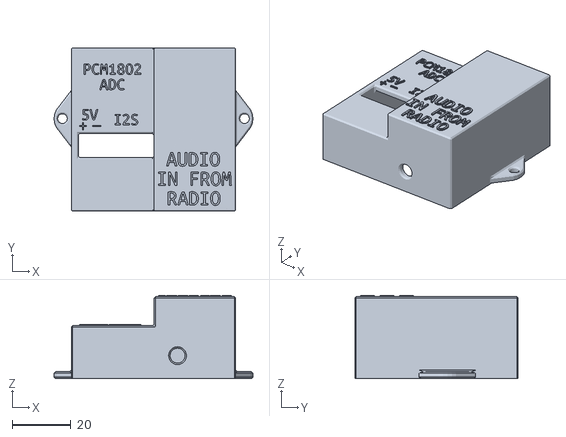
[picture p55: CAD file, 2026-09-28]
hardware/STLs/IN - Electronics - PCM1802 ADC Case TOP.stl
67.9 x 55.8 x 28.4
