Z3r0shin/ambersong/hardware/STLs/IN - Tube Radio - Faraday Cage 1.stl

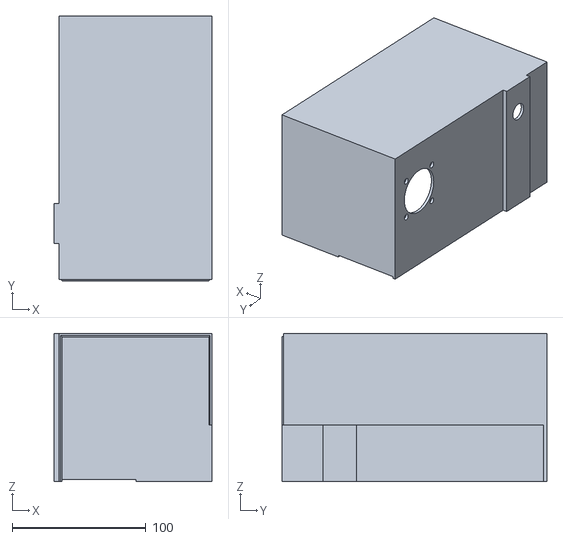
[picture p56: CAD file, 2026-09-28]
hardware/STLs/IN - Tube Radio - Faraday Cage 1.stl
118.0 x 197.7 x 110.7
