Z3r0shin/ambersong/hardware/STLs/IN - Electronics - Hall Sensor Stepper Limit Case.stl

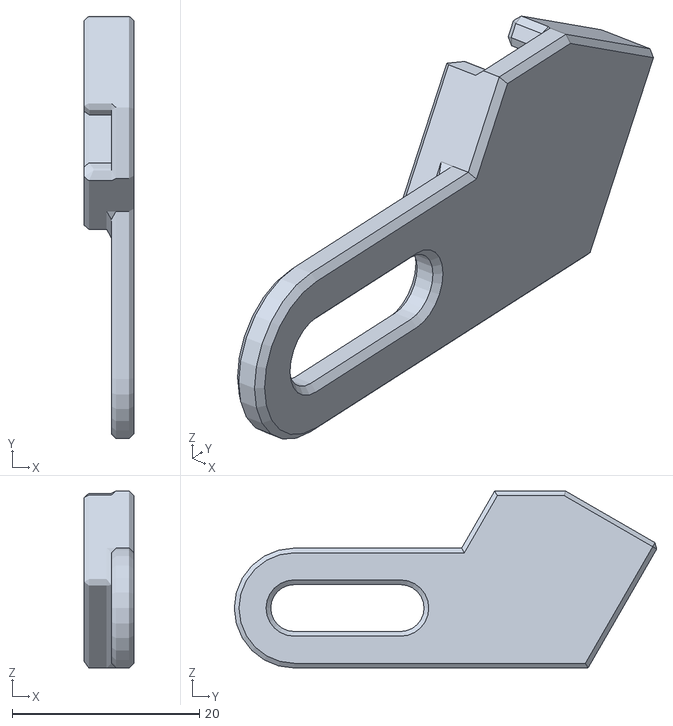
[picture p57: CAD file, 2026-09-28]
hardware/STLs/IN - Electronics - Hall Sensor Stepper Limit Case.stl
5.30 x 45.1 x 18.9
