Z3r0shin/ambersong/hardware/STLs/AUDIO - Speakers Holder and Seal.stl

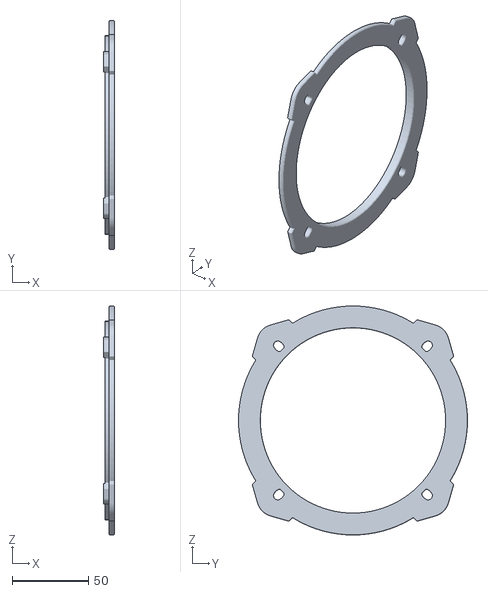
[picture p58: CAD file, 2026-09-28]
hardware/STLs/AUDIO - Speakers Holder and Seal.stl
7.50 x 150.6 x 150.6
