Z3r0shin/ambersong/hardware/STLs/IN - Electronics - Backing Panel 1.stl

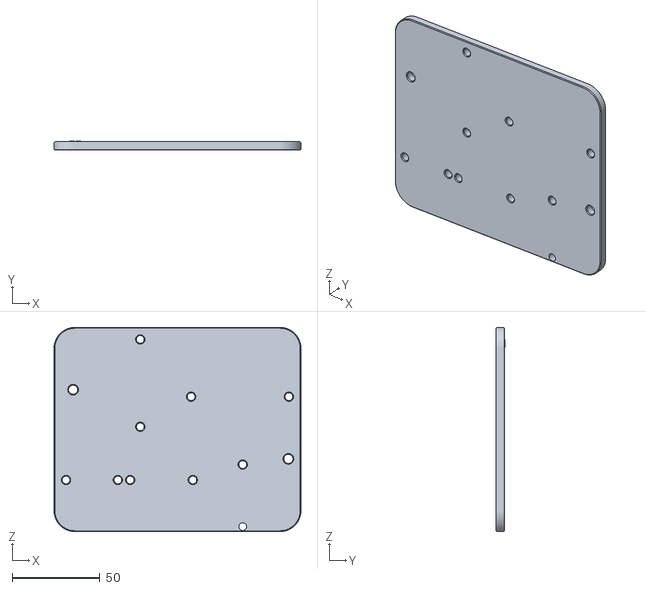
[picture p59: CAD file, 2026-09-28]
hardware/STLs/IN - Electronics - Backing Panel 1.stl
141.1 x 5.20 x 116.7
