Z3r0shin/ambersong/hardware/STLs/FRONT - Tuning Pot Extender PLA Shaft.stl

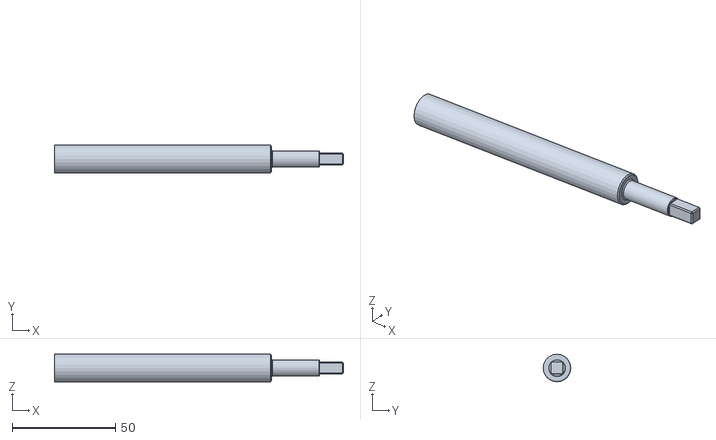
[picture p60: CAD file, 2026-09-28]
hardware/STLs/FRONT - Tuning Pot Extender PLA Shaft.stl
140.1 x 13.4 x 13.4
