Z3r0shin/ambersong/hardware/STLs/IN - Electronics - 5V PSU Case Top.stl

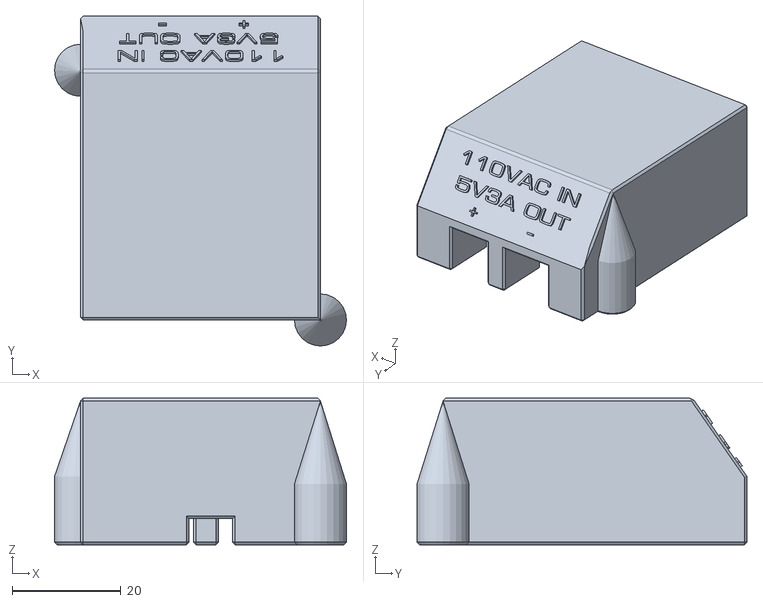
[picture p61: CAD file, 2026-09-28]
hardware/STLs/IN - Electronics - 5V PSU Case Top.stl
53.8 x 60.8 x 27.0
