Z3r0shin/ambersong/hardware/STLs/IN - Tube Radio - Faraday Cage 2.stl

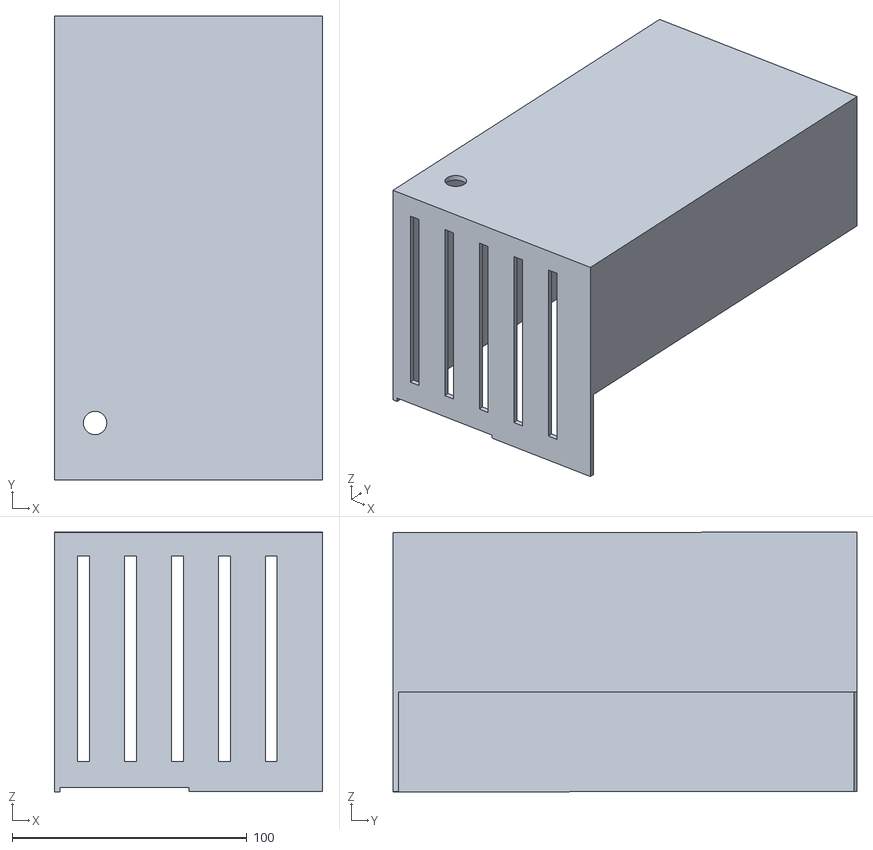
[picture p62: CAD file, 2026-09-28]
hardware/STLs/IN - Tube Radio - Faraday Cage 2.stl
114.4 x 197.7 x 110.7
