Z3r0shin/ambersong/hardware/STLs/BACK - Panel Anchors Bottom.stl

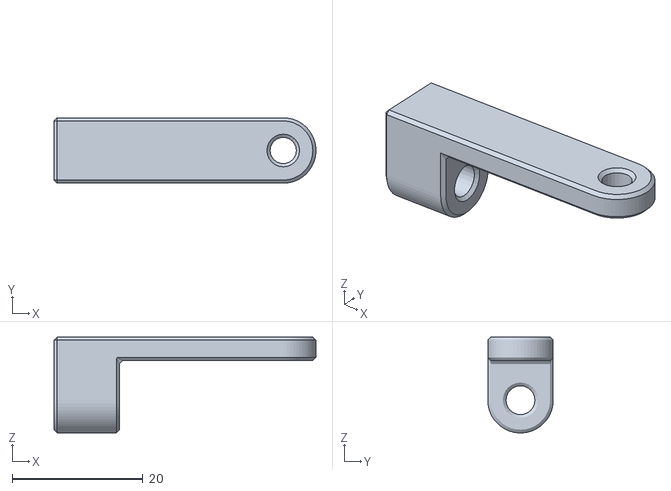
[picture p63: CAD file, 2026-09-28]
hardware/STLs/BACK - Panel Anchors Bottom.stl
40.0 x 10.0 x 14.6
