Z3r0shin/ambersong/hardware/STLs/BACK - Panel Anchors.stl

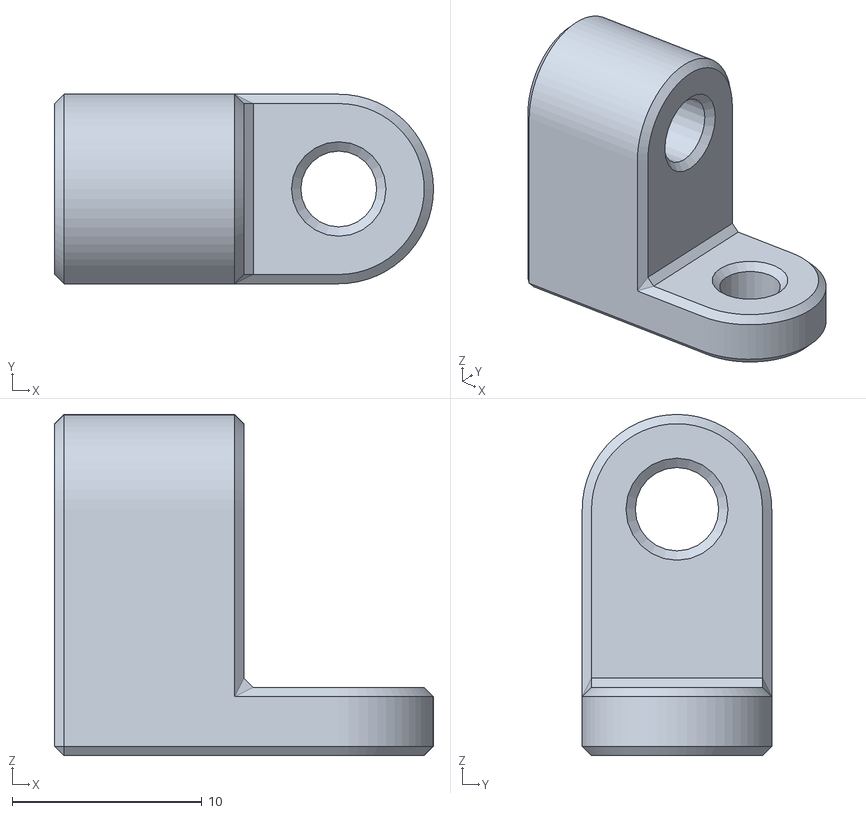
[picture p64: CAD file, 2026-09-28]
hardware/STLs/BACK - Panel Anchors.stl
20.0 x 10.0 x 18.0
