Z3r0shin/ambersong/hardware/STLs/IN - Electronics - AS5600 Case - Connecting Rod.stl

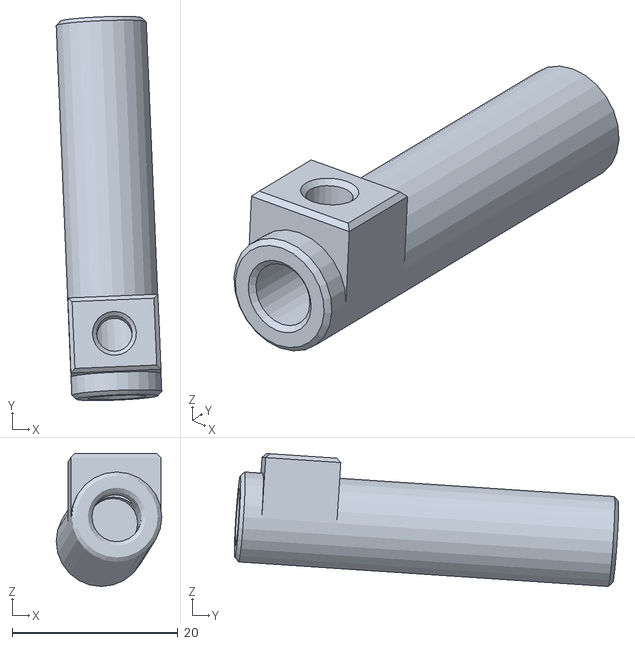
[picture p65: CAD file, 2026-09-28]
hardware/STLs/IN - Electronics - AS5600 Case - Connecting Rod.stl
12.8 x 46.4 x 16.1
