Z3r0shin/ambersong/hardware/STLs/FRONT - FM Dial - Spacer.stl

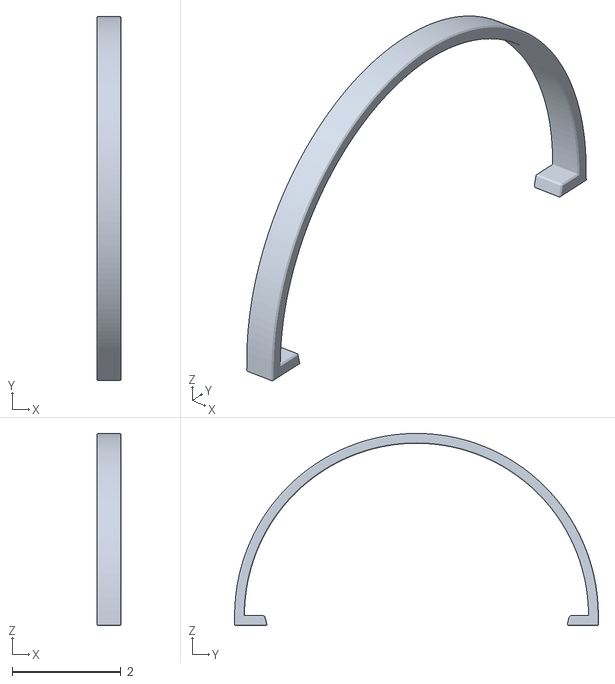
[picture p67: CAD file, 2026-09-28]
hardware/STLs/FRONT - FM Dial - Spacer.stl
0.445 x 6.68 x 3.53
