Z3r0shin/ambersong/hardware/STLs/IN - Electronics - DS3231 RTC Case TOP.stl

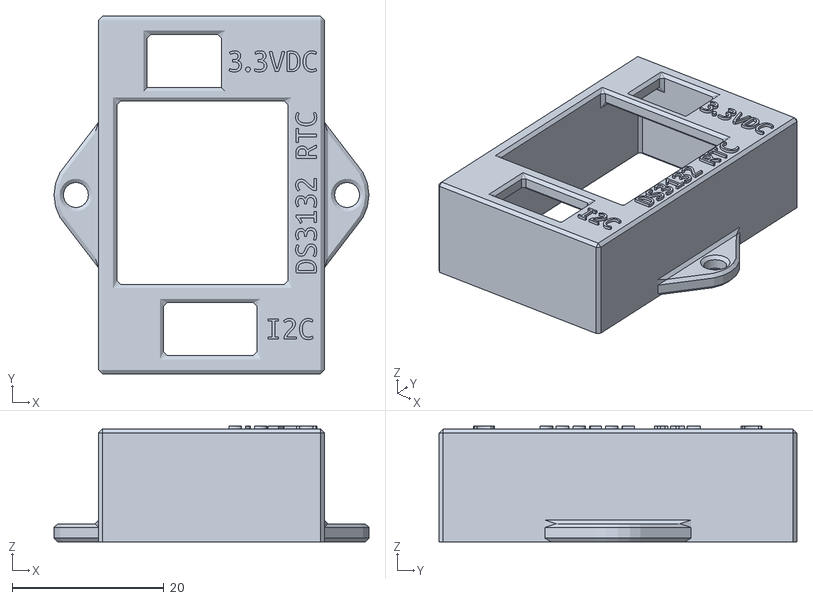
[picture p68: CAD file, 2026-09-28]
hardware/STLs/IN - Electronics - DS3231 RTC Case TOP.stl
41.6 x 47.2 x 15.3
