Z3r0shin/ambersong/hardware/STLs/BACK - Dual USB-C Ports.stl

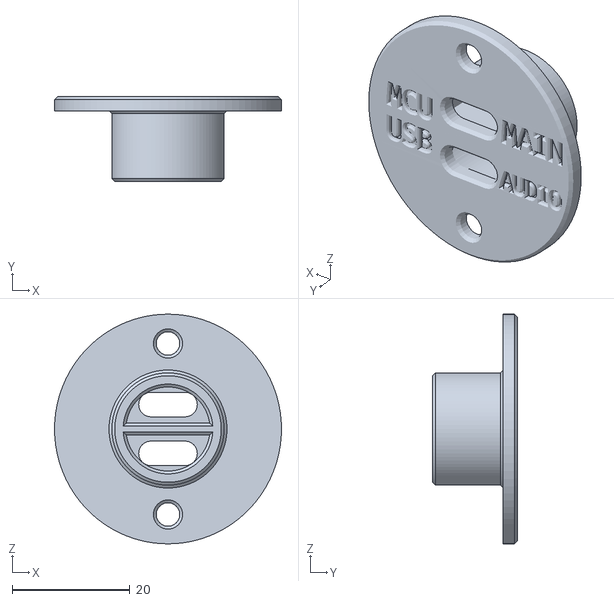
[picture p69: CAD file, 2026-09-28]
hardware/STLs/BACK - Dual USB-C Ports.stl
38.6 x 14.4 x 39.1
