Z3r0shin/ambersong/hardware/STLs/IN - Electronics - Bluetooth LED Pusher.stl

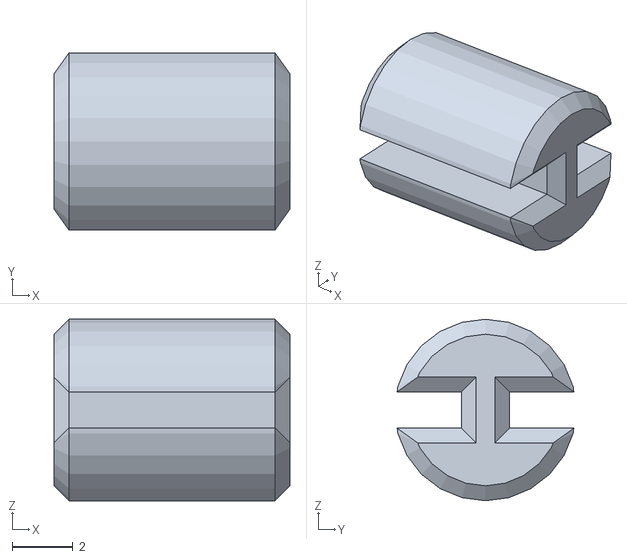
[picture p70: CAD file, 2026-09-28]
hardware/STLs/IN - Electronics - Bluetooth LED Pusher.stl
7.80 x 5.84 x 6.00
