Z3r0shin/ambersong/hardware/STLs/IN - Electronics - RDA5807M - Middle Bottom.stl

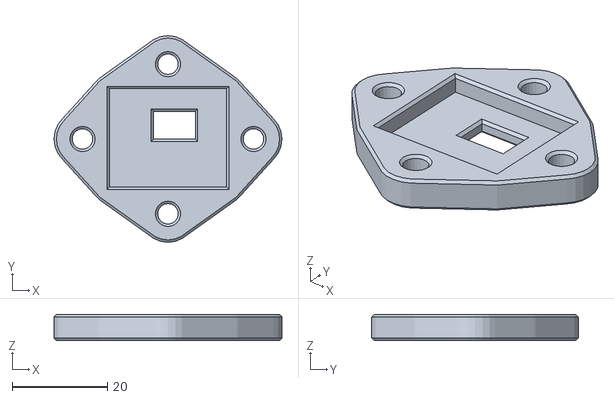
[picture p71: CAD file, 2026-09-28]
hardware/STLs/IN - Electronics - RDA5807M - Middle Bottom.stl
48.0 x 43.5 x 5.50
