Z3r0shin/ambersong/hardware/STLs/IN - Electronics - AC Line Filter Case.stl

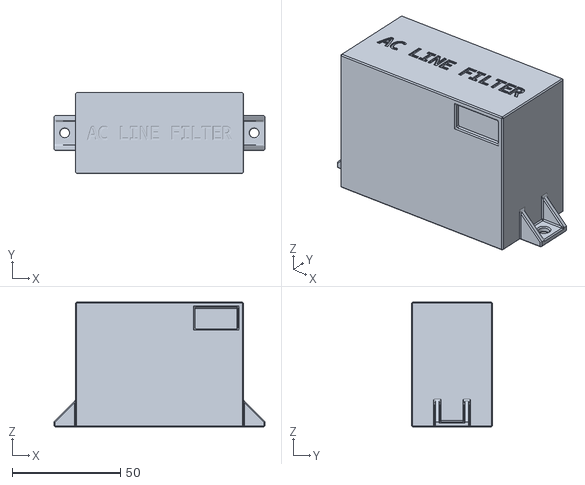
[picture p72: CAD file, 2026-09-28]
hardware/STLs/IN - Electronics - AC Line Filter Case.stl
97.4 x 37.4 x 57.7
