Z3r0shin/ambersong/hardware/STLs/FRONT - Tuner Pot Knob.stl

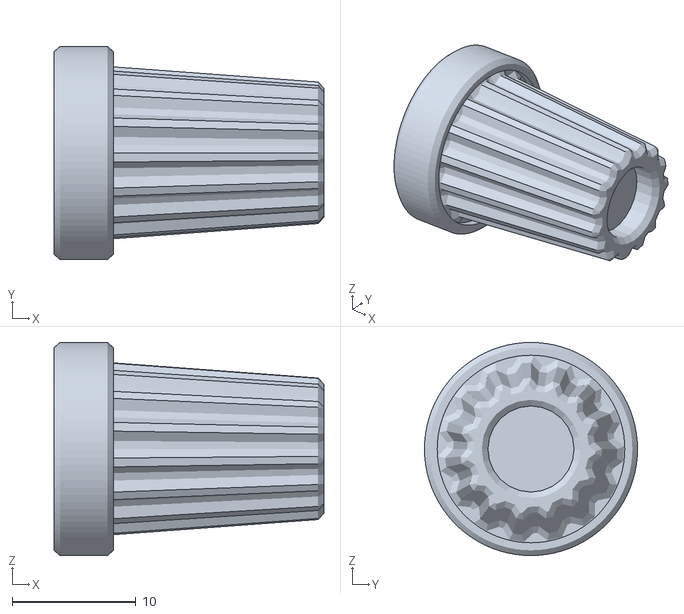
[picture p73: CAD file, 2026-09-28]
hardware/STLs/FRONT - Tuner Pot Knob.stl
21.8 x 17.2 x 17.2
