Z3r0shin/ambersong/hardware/STLs/IN - Electronics - Front Panel FM LEDs Case TOP.stl

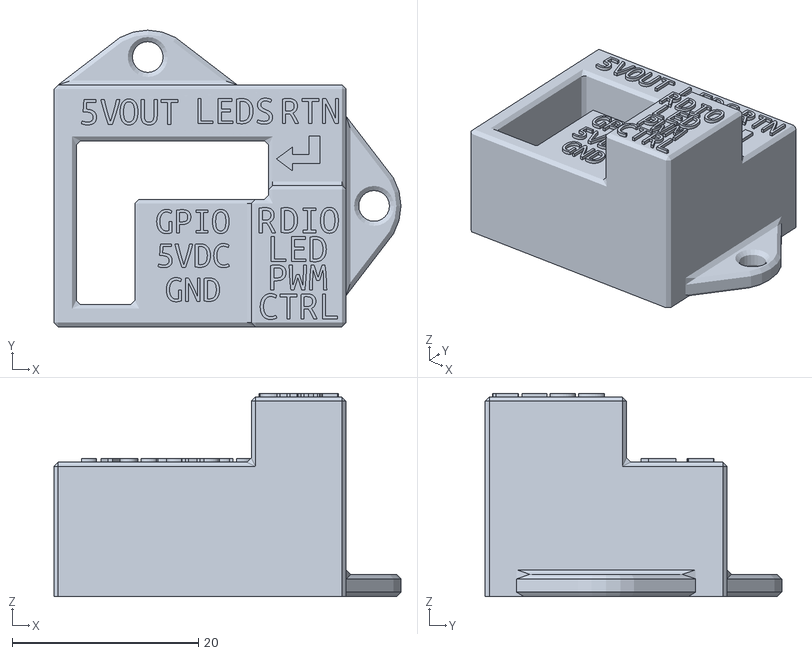
[picture p74: CAD file, 2026-09-28]
hardware/STLs/IN - Electronics - Front Panel FM LEDs Case TOP.stl
37.3 x 31.9 x 21.9
