Z3r0shin/ambersong/hardware/STLs/BACK - Fan Intake.stl

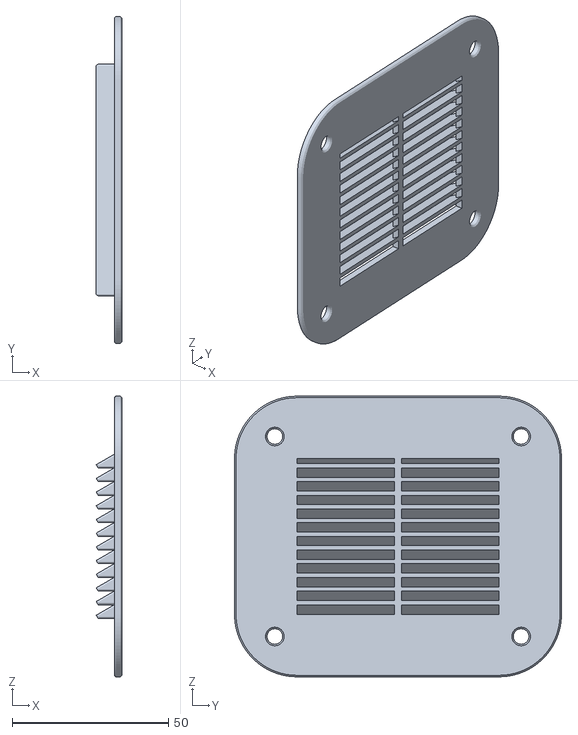
[picture p75: CAD file, 2026-09-28]
hardware/STLs/BACK - Fan Intake.stl
8.20 x 104.8 x 89.9
