Z3r0shin/ambersong/hardware/STLs/FRONT - Panel Anchors - Insidemost.stl

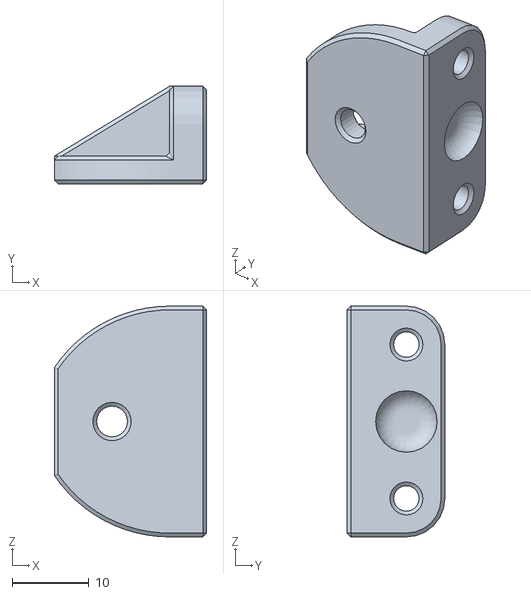
[picture p76: CAD file, 2026-09-28]
hardware/STLs/FRONT - Panel Anchors - Insidemost.stl
19.8 x 12.7 x 30.0
