Z3r0shin/ambersong/hardware/STLs/BACK - Panel Anchors Inner Corners.stl

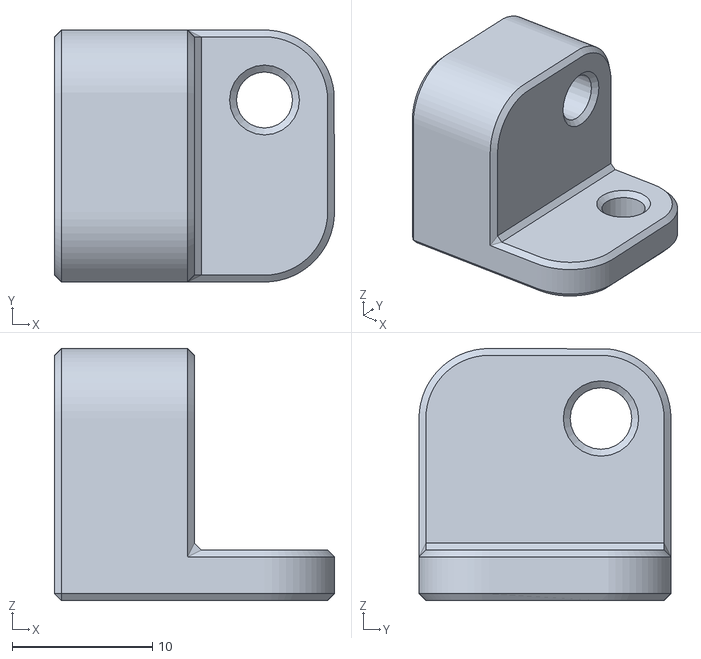
[picture p77: CAD file, 2026-09-28]
hardware/STLs/BACK - Panel Anchors Inner Corners.stl
20.0 x 18.0 x 18.0
