Z3r0shin/ambersong/hardware/STLs/BACK - Panel Anchors Outer Corners.stl

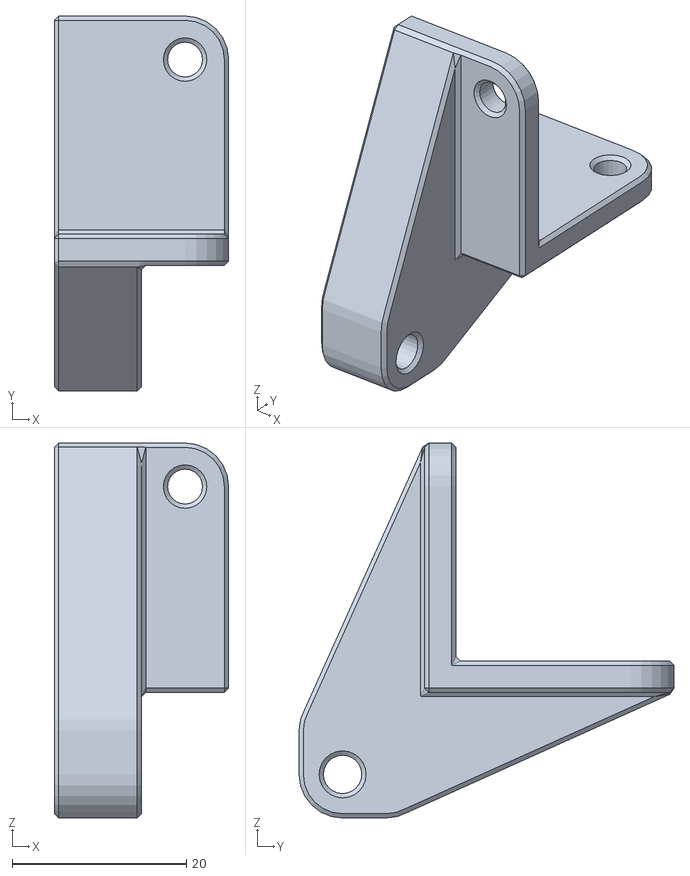
[picture p78: CAD file, 2026-09-28]
hardware/STLs/BACK - Panel Anchors Outer Corners.stl
20.0 x 43.0 x 43.0
