Z3r0shin/ambersong/hardware/STLs/IN - Electronics - RDA5807M - TOP.stl

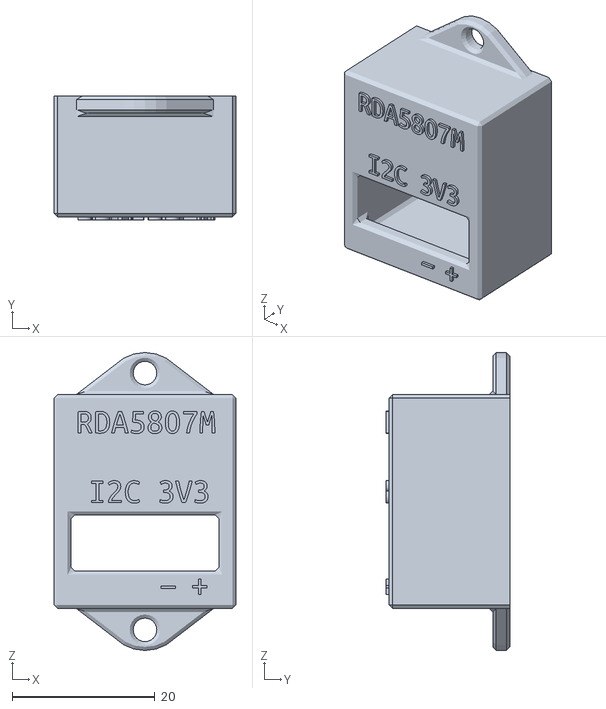
[picture p79: CAD file, 2026-09-28]
hardware/STLs/IN - Electronics - RDA5807M - TOP.stl
25.5 x 17.4 x 41.8
