Z3r0shin/ambersong/hardware/STLs/IN - Electronics - Power Detect Case TOP.stl

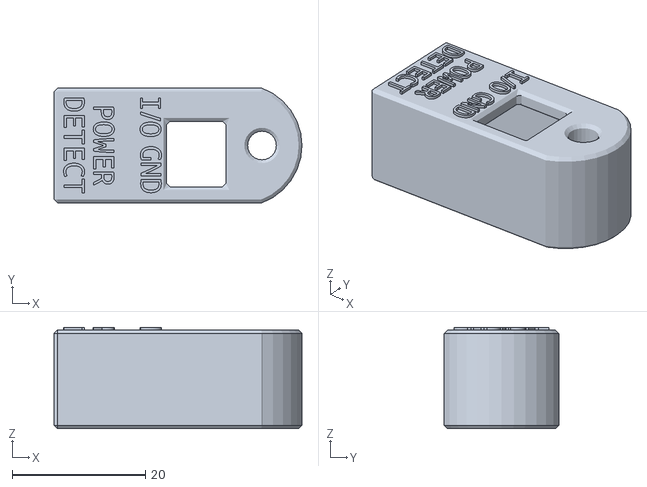
[picture p80: CAD file, 2026-09-28]
hardware/STLs/IN - Electronics - Power Detect Case TOP.stl
37.2 x 17.2 x 15.2
