Z3r0shin/ambersong/hardware/schematics/Ambersong - 7 SEGMENTS 24H CLOCK DISPLAY.kicad_sch

## KiCad design hardware/schematics/Ambersong - 7 SEGMENTS 24H CLOCK DISPLAY.kicad_sch (2026-09-28)

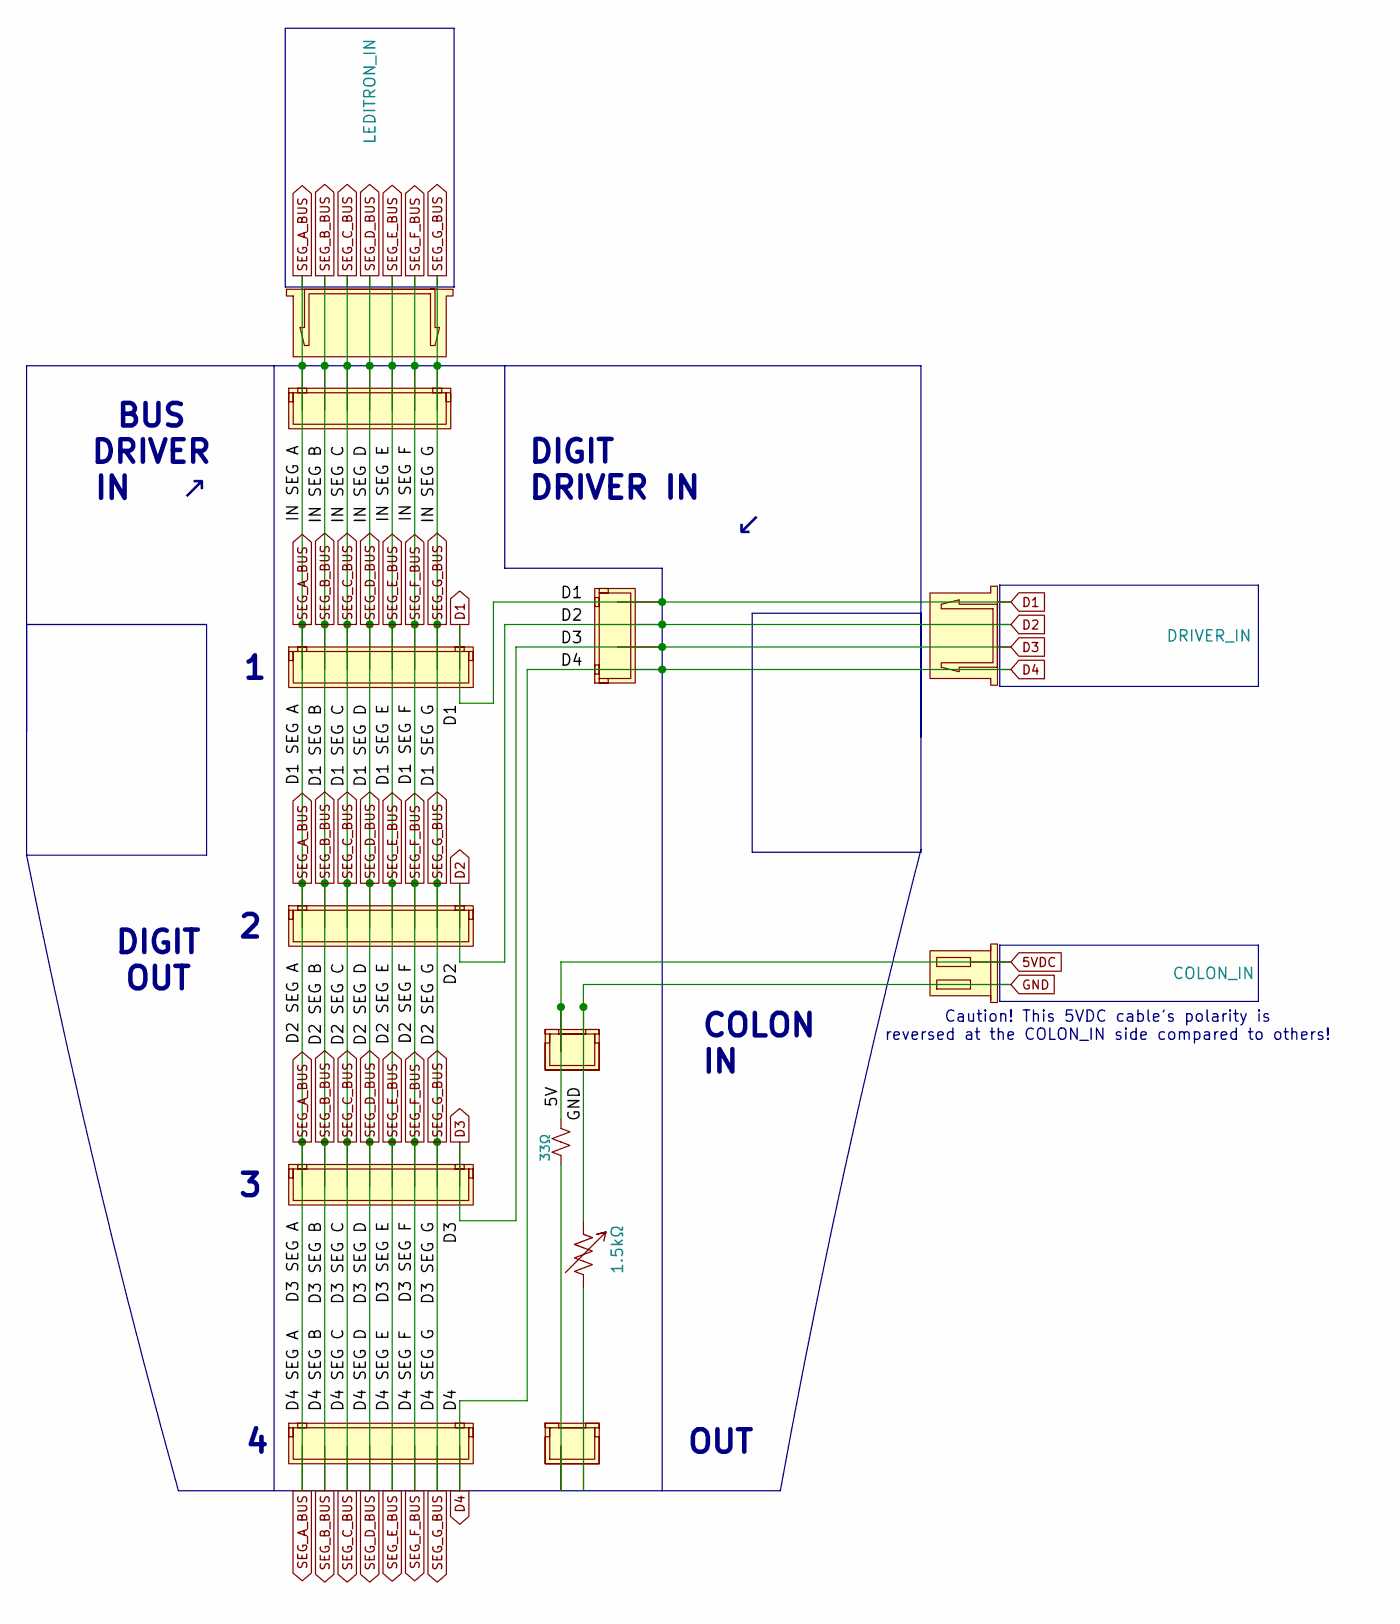
[picture p81: schematic Ambersong - 7 SEGMENTS 24H CLOCK DISPLAY.kicad_sch]

Parts:
33Ω: R_Small_US
COLON_IN: (no value)
DRIVER_IN: (no value)
LEDITRON_IN: (no value)
R99: 1.5kΩ
U12, U17, U18, U19, U32, U33, U34, U35: (no value)

Connections:
5VDC: 33Ω.1, COLON_IN., U34.
D1: DRIVER_IN., U18., U33.
D2: DRIVER_IN., U17., U33.
D3: DRIVER_IN., U19., U33.
D4: DRIVER_IN., U32., U33.
GND: COLON_IN., R99.1, U34.
unnamed: 33Ω.2, U35.
unnamed: R99.2, U35.
SEG_A_BUS: LEDITRON_IN., U12., U17., U18., U19., U32.
SEG_B_BUS: LEDITRON_IN., U12., U17., U18., U19., U32.
SEG_C_BUS: LEDITRON_IN., U12., U17., U18., U19., U32.
SEG_D_BUS: LEDITRON_IN., U12., U17., U18., U19., U32.
SEG_E_BUS: LEDITRON_IN., U12., U17., U18., U19., U32.
SEG_F_BUS: LEDITRON_IN., U12., U17., U18., U19., U32.
SEG_G_BUS: LEDITRON_IN., U12., U17., U18., U19., U32.

Notes on the sheet:
DIGIT DRIVER IN ↙
BUS DRIVER IN ↗
OUT
COLON IN
DIGIT OUT
Caution! This 5VDC cable's polarity is reversed at the COLON_IN side compared to others!
