Z3r0shin/ambersong/hardware/schematics/Ambersong - AUDIO MCU ESP32-WROOM-32.kicad_sch

## KiCad design hardware/schematics/Ambersong - AUDIO MCU ESP32-WROOM-32.kicad_sch (2026-09-28)

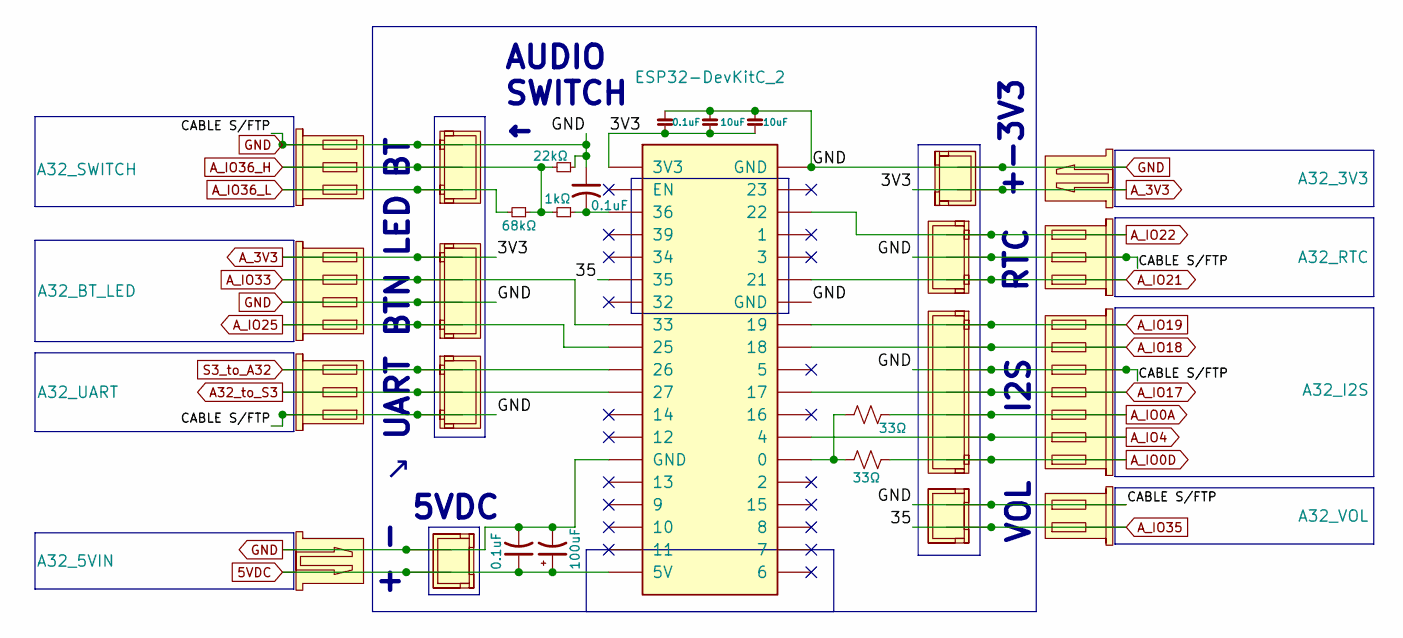
[picture p82: schematic Ambersong - AUDIO MCU ESP32-WROOM-32.kicad_sch]

Parts:
0.1uF: C_Small_US
1kΩ, 22kΩ, 33Ω, 68kΩ: R_Small_US
100uF: C_Polarized_Small_US
A32_3V3, A32_5VIN, A32_BT_LED, A32_I2S, A32_RTC, A32_SWITCH, A32_UART, A32_VOL: (no value)
C54: 0.1uF
C55, C56: 10uF
U45, U75, U76, U77, U78, U79, U80, U81: (no value)
U74: ESP32-DevKitC_2; ESP32-DevKitC

Connections:
5VDC: 0.1uF.1, 100uF.1, A32_5VIN., U74., U81.
A32_to_S3: A32_UART., U74., U80.
A_3V3: A32_3V3., A32_BT_LED., C54.1, C55.1, C56.1, U74., U75., U79.
A_IO0A: 33Ω.2, A32_I2S., U77.
A_IO0D: 33Ω.2, A32_I2S., U77.
A_IO4: A32_I2S., U74., U77.
A_IO17: A32_I2S., U74., U77.
A_IO18: A32_I2S., U74., U77.
A_IO19: A32_I2S., U74., U77.
A_IO21: A32_RTC., U74., U76.
A_IO22: A32_RTC., U74., U76.
A_IO25: A32_BT_LED., U74., U79.
A_IO33: A32_BT_LED., U74., U79.
A_IO35: A32_VOL., U45., U74.
A_IO36_H: 1kΩ.2, 22kΩ.2, 68kΩ.1, A32_SWITCH., U78.
A_IO36_L: 68kΩ.2, A32_SWITCH., U78.
GND: 0.1uF.1, 0.1uF.2, 22kΩ.1, 100uF.2, A32_3V3., A32_5VIN., A32_BT_LED., A32_I2S., A32_RTC., A32_SWITCH., A32_UART., A32_VOL., C54.2, C55.2, C56.2, U45., U74., U75., U76., U77., U78., U79., U80., U81.
unnamed: 0.1uF.2, 1kΩ.1, U74.
unnamed: 33Ω.1, U74.
S3_to_A32: A32_UART., U74., U80.

Notes on the sheet:
I2S
AUDIO SWITCH ←
+-3V3
RTC
VOL
BTN LED BT
↘ UART
+ -
5VDC
