Z3r0shin/ambersong/hardware/schematics/Ambersong - BLUETOOTH PAIR BUTTON & FRONT PANEL BLUETOOTH LED & DPDT ON-OFF-ON AUDIO SWITCH.kicad_sch

## KiCad design hardware/schematics/Ambersong - BLUETOOTH PAIR BUTTON & FRONT PANEL BLUETOOTH LED & DPDT ON-OFF-ON AUDIO SWITCH.kicad_sch (2026-09-28)

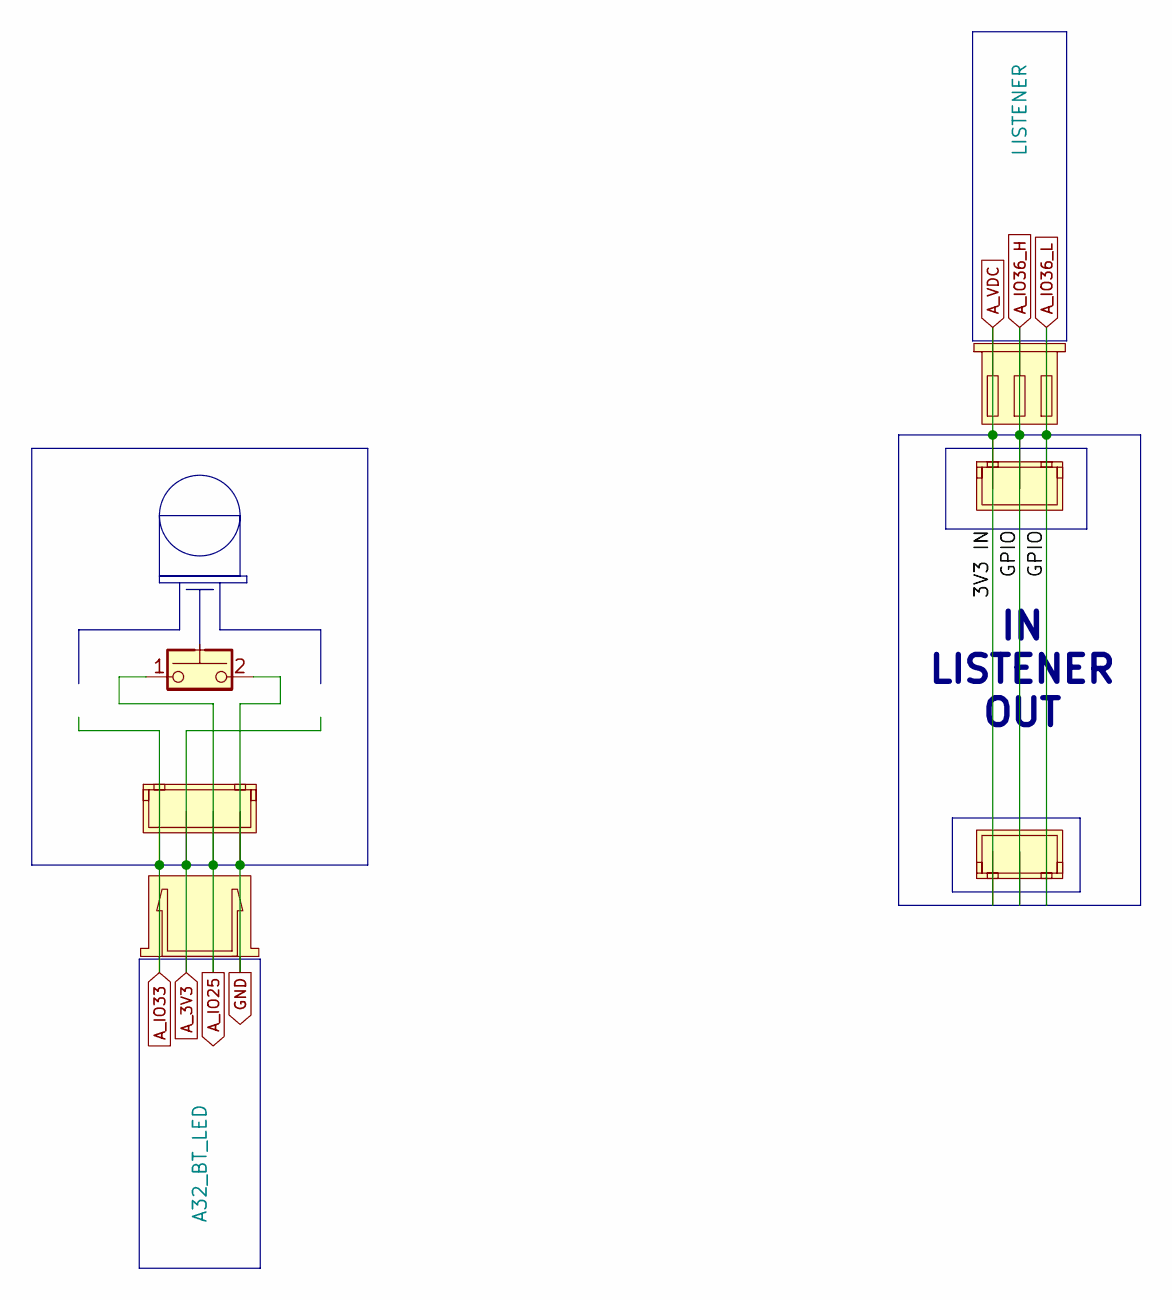
[picture p83: schematic Ambersong - BLUETOOTH PAIR BUTTON & FRONT PANEL BLUETOOTH LED & DPDT ON-OFF-ON AUDIO SWITCH.kicad_sch]

Parts:
A32_BT_LED: (no value)
LISTENER: (no value)
SW4: SW_Push_Shielded
U36, U43, U44: (no value)

Connections:
A_3V3: A32_BT_LED., U36.
A_IO25: A32_BT_LED., SW4.1, U36.
A_IO33: A32_BT_LED., U36.
A_IO36_H: LISTENER., U43., U44.
A_VDC: LISTENER., U43., U44.
GND: A32_BT_LED., SW4.2, U36.

Notes on the sheet:
IN LISTENER OUT
