Z3r0shin/ambersong/hardware/schematics/Ambersong - BOX FAN.kicad_sch

## KiCad design hardware/schematics/Ambersong - BOX FAN.kicad_sch (2026-09-28)

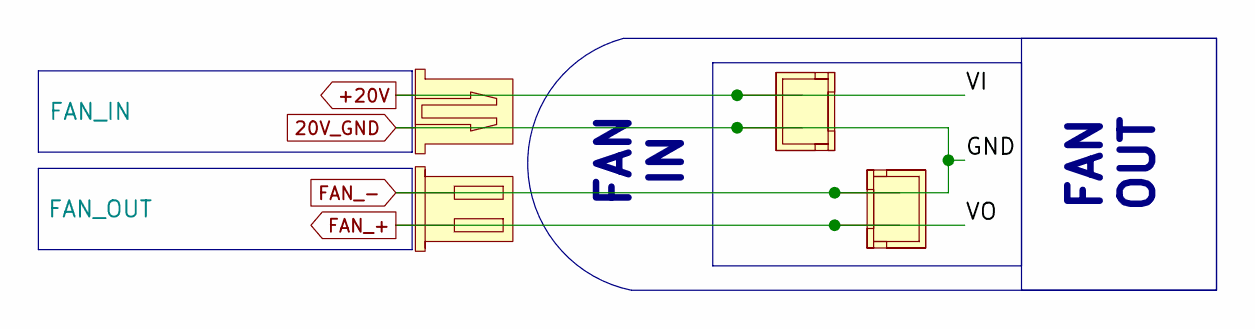
[picture p84: schematic Ambersong - BOX FAN.kicad_sch]

Parts:
FAN_IN: (no value)
FAN_OUT: (no value)
U87, U88: (no value)

Connections:
20V_GND: FAN_IN., FAN_OUT., U87., U88.
+20V: FAN_IN., U88.
FAN_+: FAN_OUT., U87.

Notes on the sheet:
FAN OUT
FAN IN
