Z3r0shin/ambersong/hardware/schematics/Ambersong - CABLES.kicad_sch

## KiCad design hardware/schematics/Ambersong - CABLES.kicad_sch (2026-09-28)

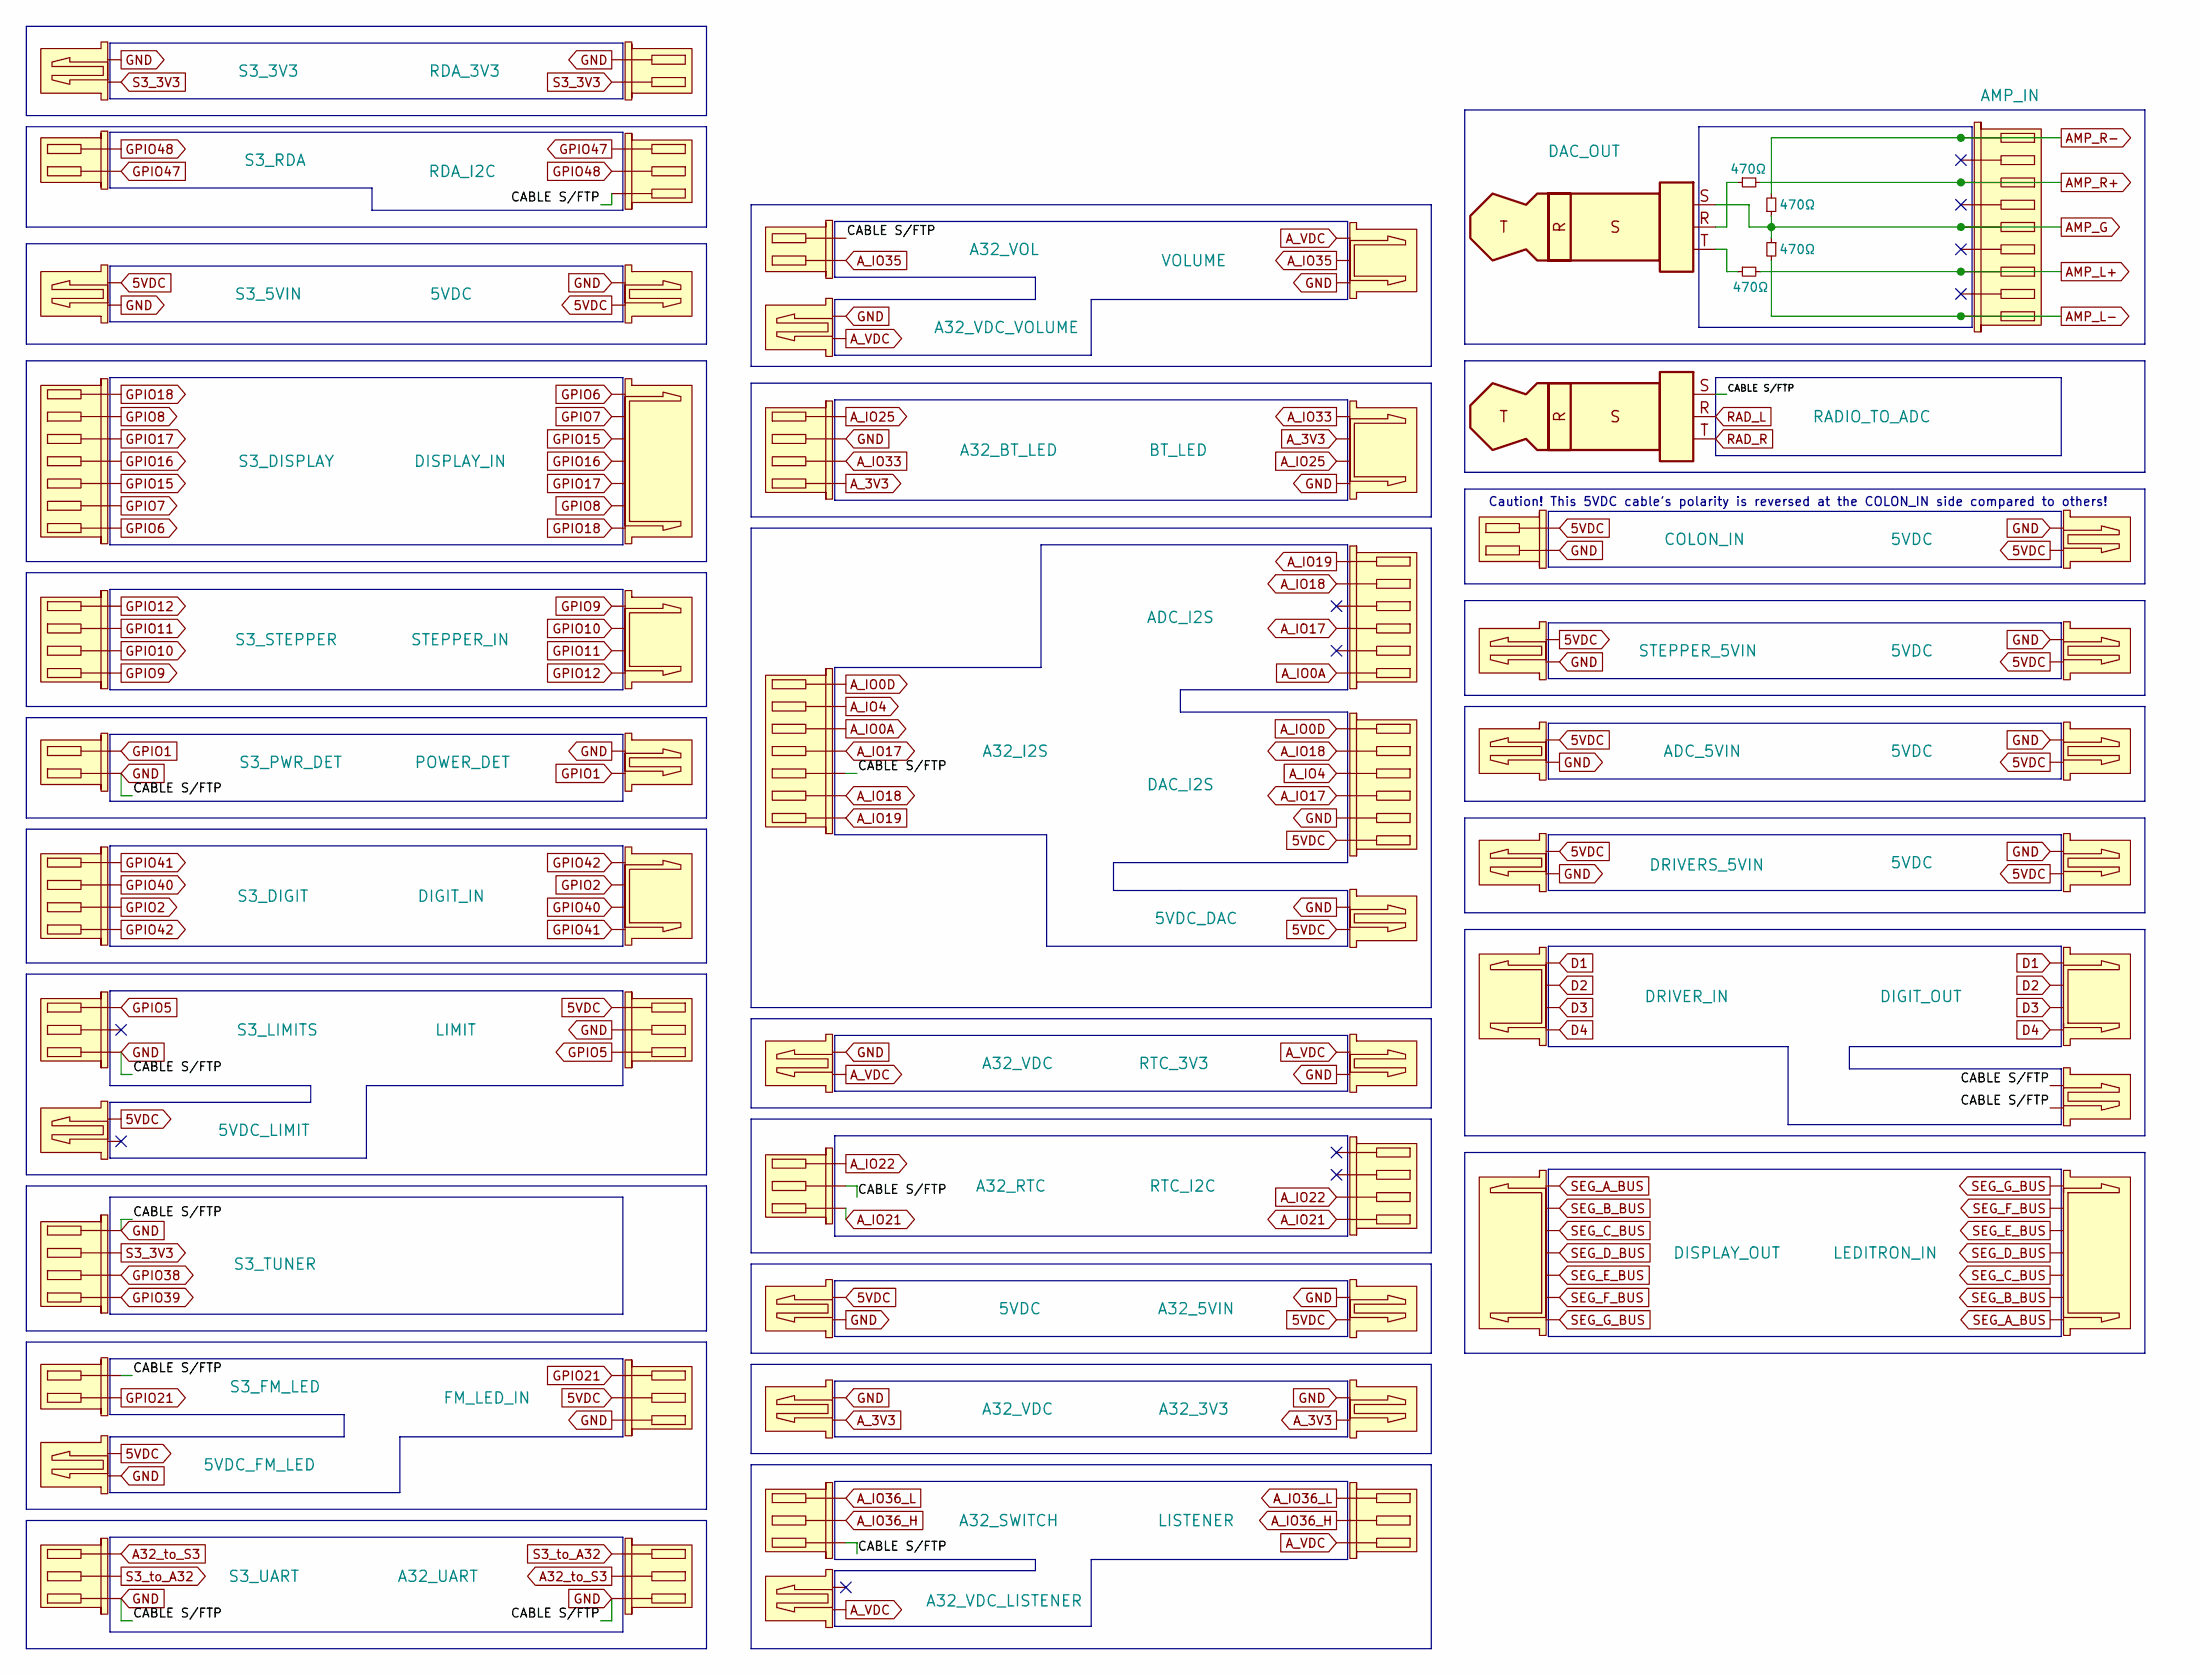
[picture p85: schematic Ambersong - CABLES.kicad_sch]

Parts:
5VDC, 5VDC_DAC, 5VDC_FM_LED, 5VDC_LIMIT: (no value)
470Ω: R_Small_US
A32_3V3, A32_5VIN, A32_BT_LED, A32_I2S, A32_RTC, A32_SWITCH, A32_UART, A32_VDC, A32_VDC_LISTENER, A32_VDC_VOLUME, A32_VOL: (no value)
ADC_5VIN: (no value)
ADC_I2S: (no value)
AMP_IN: (no value)
BT_LED: (no value)
COLON_IN: (no value)
DAC_I2S: (no value)
DIGIT_IN: (no value)
DIGIT_OUT, DIGIT_OUT1: (no value)
DISPLAY_IN: (no value)
DISPLAY_OUT: (no value)
DRIVERS_5VIN: (no value)
DRIVER_IN: (no value)
FM_LED_IN: (no value)
J49: DAC_OUT
J50: RADIO_TO_ADC
LEDITRON_IN: (no value)
LIMIT: (no value)
LISTENER: (no value)
POWER_DET: (no value)
RDA_3V3: (no value)
RDA_I2C: (no value)
RTC_3V3: (no value)
RTC_I2C: (no value)
S3_3V3, S3_5VIN, S3_DIGIT, S3_DISPLAY, S3_FM_LED, S3_LIMITS, S3_PWR_DET, S3_RDA, S3_STEPPER, S3_TUNER, S3_UART: (no value)
STEPPER_5VIN: (no value)
STEPPER_IN: (no value)
VOLUME: (no value)

Connections:
5VDC: 5VDC., 5VDC_DAC., 5VDC_FM_LED., 5VDC_LIMIT., A32_5VIN., ADC_5VIN., COLON_IN., DAC_I2S., DRIVERS_5VIN., FM_LED_IN., LIMIT., S3_5VIN., STEPPER_5VIN.
A32_to_S3: A32_UART., S3_UART.
AMP_G: 470Ω.1, AMP_IN., J49.S
AMP_L+: 470Ω.2, AMP_IN.
AMP_L-: 470Ω.2, AMP_IN.
AMP_R+: 470Ω.2, AMP_IN.
AMP_R-: 470Ω.2, AMP_IN.
A_3V3: A32_3V3., A32_BT_LED., A32_VDC., BT_LED.
A_IO0A: A32_I2S., ADC_I2S.
A_IO0D: A32_I2S., DAC_I2S.
A_IO4: A32_I2S., DAC_I2S.
A_IO17: A32_I2S., ADC_I2S., DAC_I2S.
A_IO18: A32_I2S., ADC_I2S., DAC_I2S.
A_IO19: A32_I2S., ADC_I2S.
A_IO21: A32_RTC., RTC_I2C.
A_IO22: A32_RTC., RTC_I2C.
A_IO25: A32_BT_LED., BT_LED.
A_IO33: A32_BT_LED., BT_LED.
A_IO35: A32_VOL., VOLUME.
A_IO36_H: A32_SWITCH., LISTENER.
A_IO36_L: A32_SWITCH., LISTENER.
A_VDC: A32_VDC., A32_VDC_LISTENER., A32_VDC_VOLUME., LISTENER., RTC_3V3., VOLUME.
D1: DIGIT_OUT., DRIVER_IN.
D2: DIGIT_OUT., DRIVER_IN.
D3: DIGIT_OUT., DRIVER_IN.
D4: DIGIT_OUT., DRIVER_IN.
GND: 5VDC., 5VDC_DAC., 5VDC_FM_LED., A32_3V3., A32_5VIN., A32_BT_LED., A32_I2S., A32_RTC., A32_SWITCH., A32_UART., A32_VDC., A32_VDC_VOLUME., A32_VOL., ADC_5VIN., BT_LED., COLON_IN., DAC_I2S., DIGIT_OUT1., DRIVERS_5VIN., FM_LED_IN., J50.S, LIMIT., POWER_DET., RDA_3V3., RDA_I2C., RTC_3V3., S3_3V3., S3_5VIN., S3_FM_LED., S3_LIMITS., S3_PWR_DET., S3_TUNER., S3_UART., STEPPER_5VIN., VOLUME.
GPIO1: POWER_DET., S3_PWR_DET.
GPIO2: DIGIT_IN., S3_DIGIT.
GPIO5: LIMIT., S3_LIMITS.
GPIO6: DISPLAY_IN., S3_DISPLAY.
GPIO7: DISPLAY_IN., S3_DISPLAY.
GPIO8: DISPLAY_IN., S3_DISPLAY.
GPIO9: S3_STEPPER., STEPPER_IN.
GPIO10: S3_STEPPER., STEPPER_IN.
GPIO11: S3_STEPPER., STEPPER_IN.
GPIO12: S3_STEPPER., STEPPER_IN.
GPIO15: DISPLAY_IN., S3_DISPLAY.
GPIO16: DISPLAY_IN., S3_DISPLAY.
GPIO17: DISPLAY_IN., S3_DISPLAY.
GPIO18: DISPLAY_IN., S3_DISPLAY.
GPIO21: FM_LED_IN., S3_FM_LED.
GPIO38: S3_TUNER.
GPIO39: S3_TUNER.
GPIO40: DIGIT_IN., S3_DIGIT.
GPIO41: DIGIT_IN., S3_DIGIT.
GPIO42: DIGIT_IN., S3_DIGIT.
GPIO47: RDA_I2C., S3_RDA.
GPIO48: RDA_I2C., S3_RDA.
unnamed: 470Ω.1, J49.R, J49.T
RAD_L: J50.R
RAD_R: J50.T
S3_3V3: RDA_3V3., S3_3V3., S3_TUNER.
S3_to_A32: A32_UART., S3_UART.
SEG_A_BUS: DISPLAY_OUT., LEDITRON_IN.
SEG_B_BUS: DISPLAY_OUT., LEDITRON_IN.
SEG_C_BUS: DISPLAY_OUT., LEDITRON_IN.
SEG_D_BUS: DISPLAY_OUT., LEDITRON_IN.
SEG_E_BUS: DISPLAY_OUT., LEDITRON_IN.
SEG_F_BUS: DISPLAY_OUT., LEDITRON_IN.
SEG_G_BUS: DISPLAY_OUT., LEDITRON_IN.

Notes on the sheet:
Caution! This 5VDC cable's polarity is reversed at the COLON_IN side compared to others!
