Z3r0shin/ambersong/hardware/schematics/Ambersong - DS3231 RTC.kicad_sch

## KiCad design hardware/schematics/Ambersong - DS3231 RTC.kicad_sch (2026-09-28)

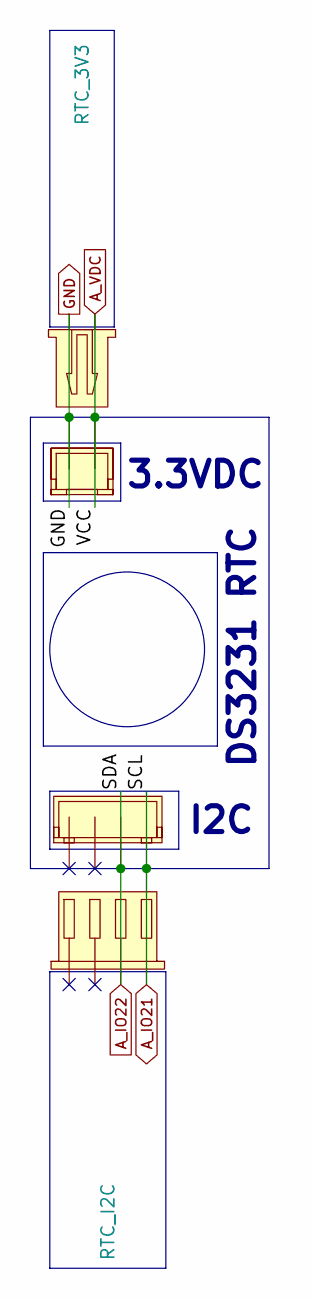
[picture p86: schematic Ambersong - DS3231 RTC.kicad_sch]

Parts:
RTC_3V3: (no value)
RTC_I2C: (no value)
U15, U16: (no value)

Connections:
A_IO21: RTC_I2C., U16.
A_IO22: RTC_I2C., U16.
A_VDC: RTC_3V3., U15.
GND: RTC_3V3., U15.

Notes on the sheet:
3.3VDC
I2C
DS3231 RTC
