Z3r0shin/ambersong/hardware/schematics/Ambersong - LLOYDS TM-838N TUBE RADIO.kicad_sch

## KiCad design hardware/schematics/Ambersong - LLOYDS TM-838N TUBE RADIO.kicad_sch (2026-09-28)

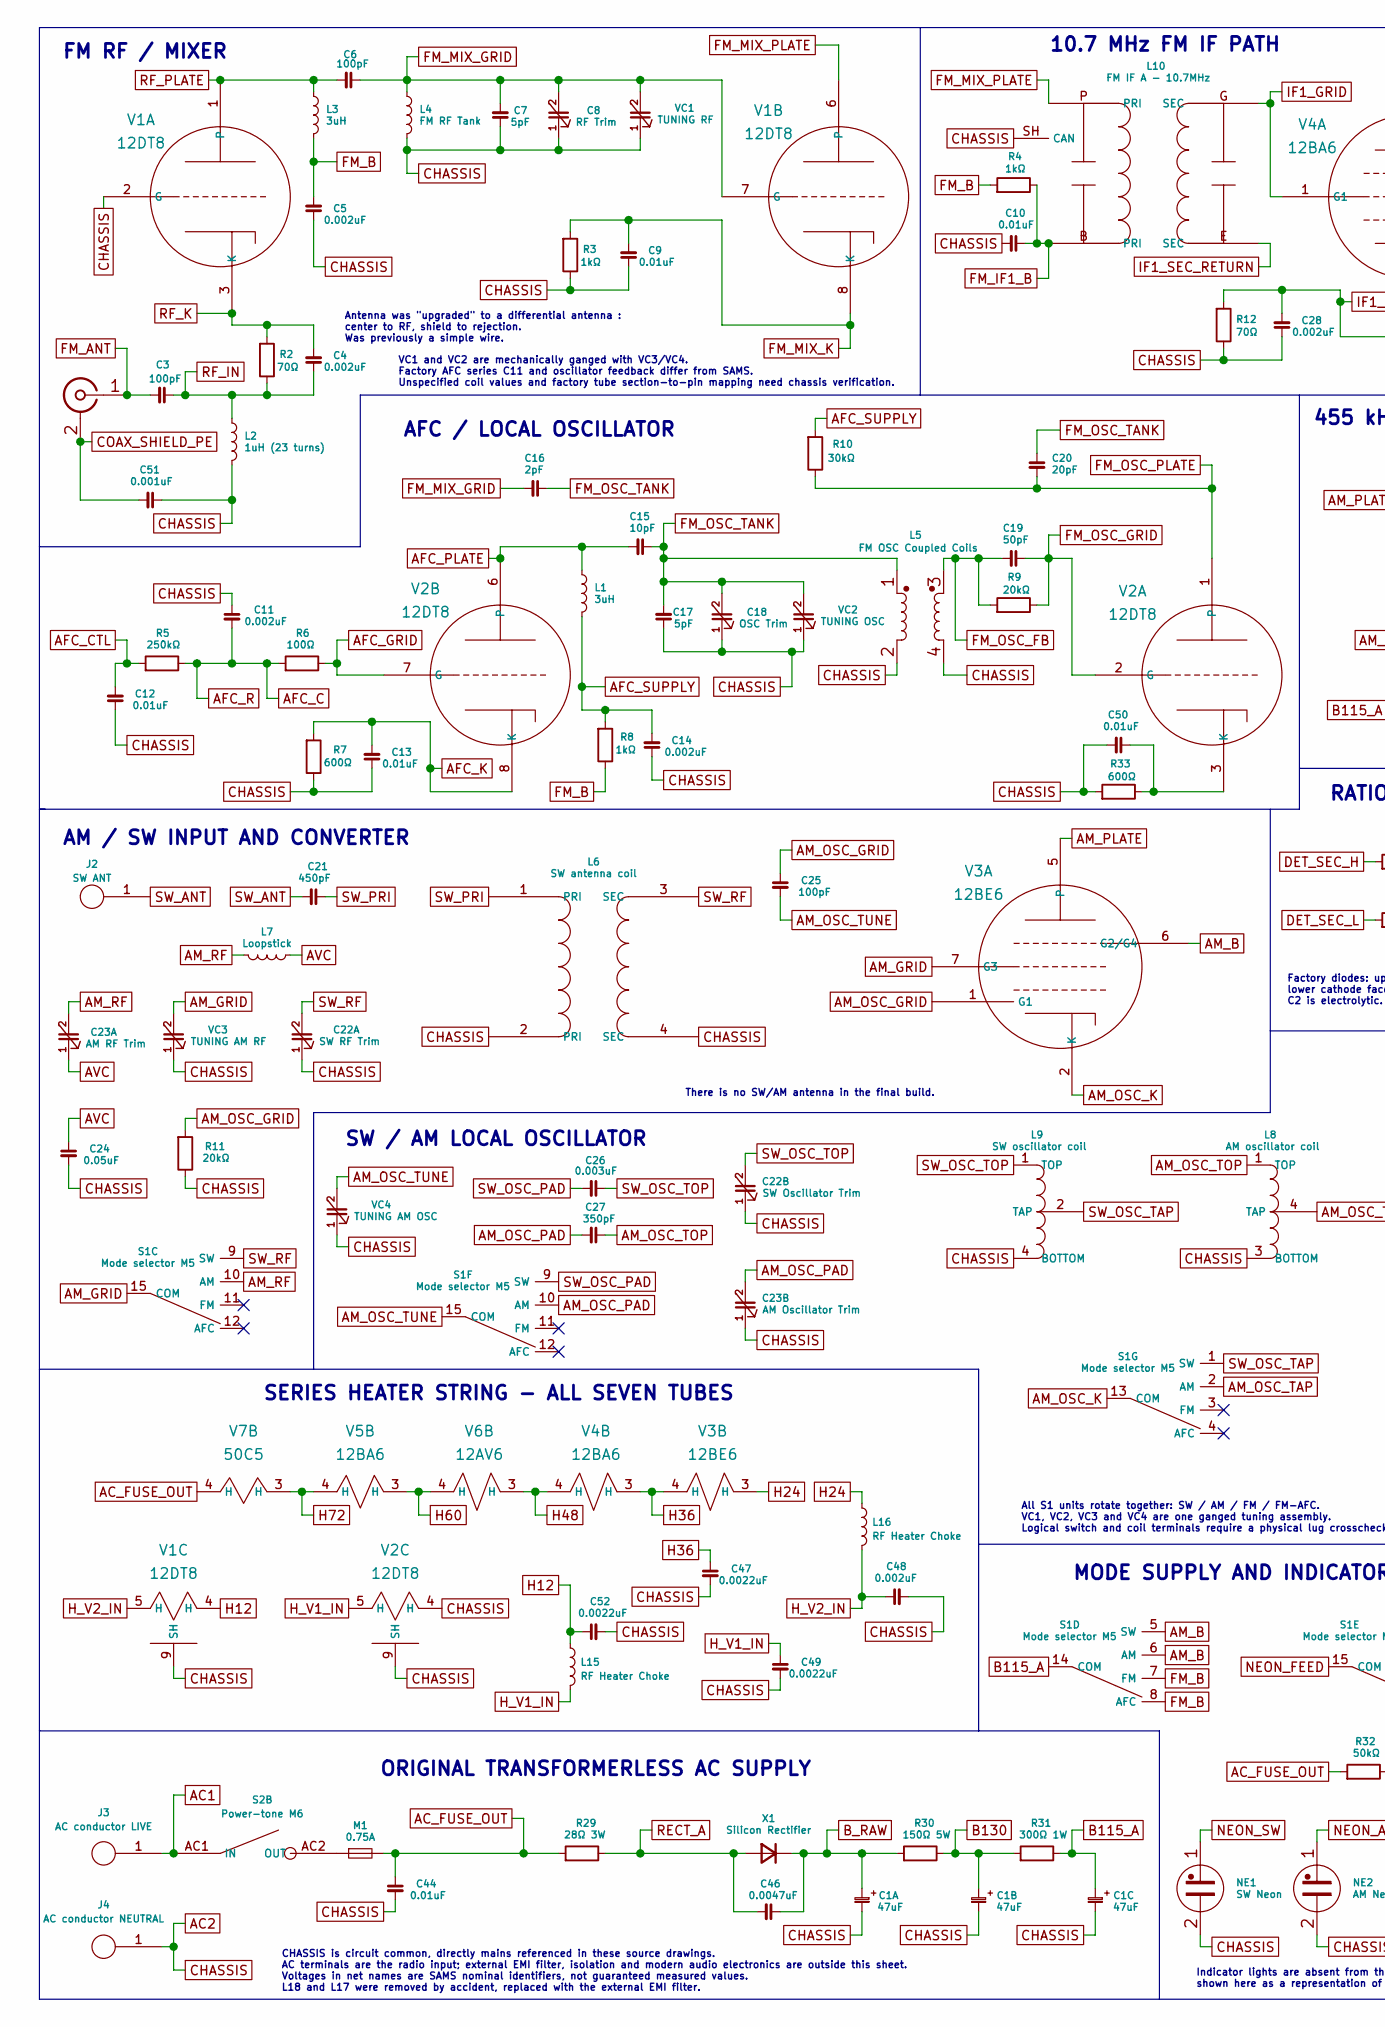
[picture p87: schematic Ambersong - LLOYDS TM-838N TUBE RADIO.kicad_sch, part in row 1, column 1]

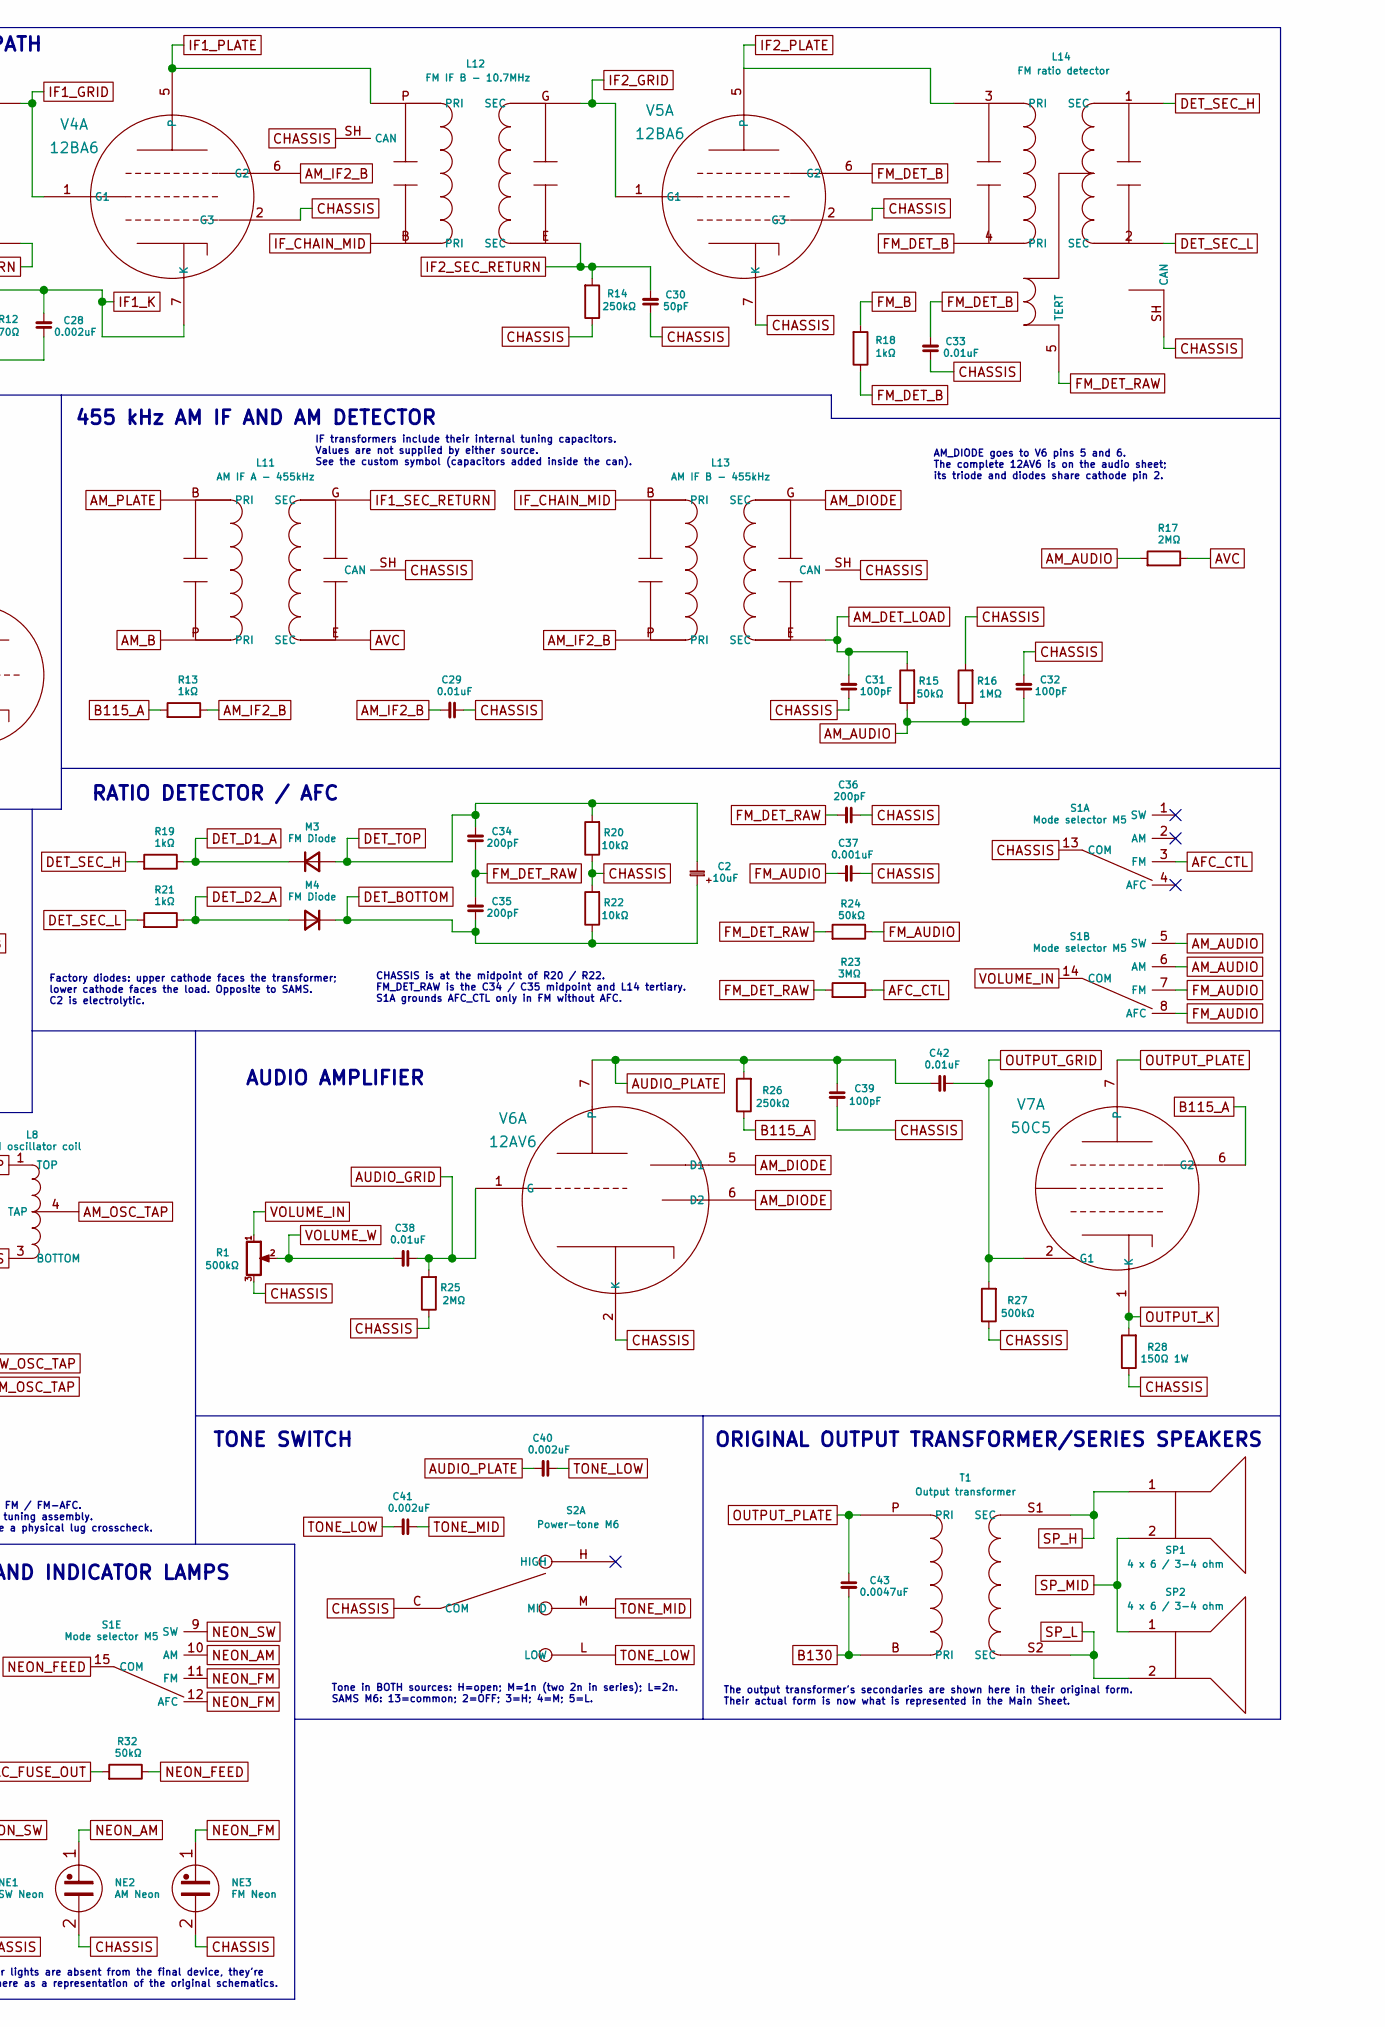
[picture p88: schematic Ambersong - LLOYDS TM-838N TUBE RADIO.kicad_sch, part in row 1, column 2]

Parts:
C1A, C1B, C1C: 47uF
C2: 10uF
C3, C6, C25, C31, C32, C39: 100pF
C4, C5, C11, C14, C28, C40, C41, C48: 0.002uF
C7, C17: 5pF
C8: RF Trim
C9, C10, C12, C13, C29, C33, C38, C42, C44, C50: 0.01uF
C15: 10pF
C16: 2pF
C18: OSC Trim
C19, C30: 50pF
C20: 20pF
C21: 450pF
C22A: SW RF Trim
C22B: SW Oscillator Trim
C23A: AM RF Trim
C23B: AM Oscillator Trim
C24: 0.05uF
C26: 0.003uF
C27: 350pF
C34, C35, C36: 200pF
C37, C51: 0.001uF
C43, C46: 0.0047uF
C47, C49, C52: 0.0022uF
J2: SW ANT
J3: AC conductor LIVE
J4: AC conductor NEUTRAL
J53: RG179 Coax
L1, L3: 3uH
L2: 1uH (23 turns)
L4: FM RF Tank
L5: FM OSC Coupled Coils
L6: SW antenna coil
L7: Loopstick
L8: AM oscillator coil
L9: SW oscillator coil
L10: FM IF A - 10.7MHz
L11: AM IF A - 455kHz
L12: FM IF B - 10.7MHz
L13: AM IF B - 455kHz
L14: FM ratio detector
L15, L16: RF Heater Choke
M1: 0.75A
M3, M4: FM Diode
NE1: SW Neon
NE2: AM Neon
NE3: FM Neon
R1, R27: 500kΩ
R2, R12: 70Ω
R3, R4, R8, R13, R18, R19, R21: 1kΩ
R5, R14, R26: 250kΩ
R6: 100Ω
R7, R33: 600Ω
R9, R11: 20kΩ
R10: 30kΩ
R15, R24, R32: 50kΩ
R16: 1MΩ
R17, R25: 2MΩ
R20, R22: 10kΩ
R23: 3MΩ
R28: 150Ω 1W
R29: 28Ω 3W
R30: 150Ω 5W
R31: 300Ω 1W
S1A, S1B, S1C, S1D, S1E, S1F, S1G: Mode selector M5
S2: Power-tone M6
SP1, SP2: 4 x 6 / 3-4 ohm
T1: Output transformer
V1, V2: 12DT8
V3: 12BE6
V4, V5: 12BA6
V6: 12AV6
V7: 50C5
VC1: TUNING RF
VC2: TUNING OSC
VC3: TUNING AM RF
VC4: TUNING AM OSC
X1: Silicon Rectifier

Connections:
AC1: J3.1, S2.AC1 (IN)
AC2: C1A.2, C1B.2, C1C.2, C5.1, C7.1, C8.1, C9.1, C10.2, C11.1, C12.1, C13.1, C14.1, C17.1, C18.1, C22A.1, C22B.1, C23B.1, C24.2, C28.1, C29.1, C30.1, C31.1, C32.2, C33.1, C36.1, C37.1, C39.2, C44.2, C47.2, C48.2, C49.2, C50.2, C51.1, C52.2, J4.1, L2.2, L4.2, L5.2, L5.4, L6.2 (PRI), L6.4 (SEC), L8.3 (BOTTOM), L9.4 (BOTTOM), L10.SH (CAN), L11.SH (CAN), L12.SH (CAN), L13.SH (CAN), L14.SH (CAN), NE1.2, NE2.2, NE3.2, R1.3, R3.2, R7.2, R11.2, R12.2, R14.2, R16.1, R20.2, R22.1, R25.2, R27.2, R28.2, R33.1, S1A.13 (COM), S2.C (COM), V1.2 (G), V1.9 (SH), V2.4 (H), V2.9 (SH), V4.2 (G3), V5.2 (G3), V5.7 (K), V6.2 (K), VC1.1, VC2.1, VC3.1, VC4.1
AC_FUSE_OUT: C44.1, M1.2, R29.1, R32.1, V7.4 (H)
AFC_C: C11.2, R5.2, R6.1
AFC_CTL: C12.2, R5.1, R23.2, S1A.3 (FM)
AFC_GRID: R6.2, V2.7 (G)
AFC_K: C13.2, R7.1, V2.8 (K)
AFC_PLATE: C15.2, L1.1, V2.6
AFC_SUPPLY: C14.2, L1.2, R8.1, R10.1
AM_AUDIO: C32.1, R15.2, R16.2, R17.1, S1B.5 (SW), S1B.6 (AM)
AM_B: L11.P (PRI), S1D.5 (SW), S1D.6 (AM), V3.6 (G2/G4)
AM_DET_LOAD: C31.2, L13.E (SEC), R15.1
AM_DIODE: L13.G (SEC), V6.5 (D1), V6.6 (D2)
AM_GRID: S1C.15 (COM), V3.7 (G3), VC3.2
AM_IF2_B: C29.2, L13.P (PRI), R13.2, V4.6 (G2)
AM_OSC_GRID: C25.1, R11.1, V3.1 (G1)
AM_OSC_K: S1G.13 (COM), V3.2 (K)
AM_OSC_PAD: C23B.2, C27.2, S1F.10 (AM)
AM_OSC_TAP: L8.4 (TAP), S1G.2 (AM)
AM_OSC_TOP: C27.1, L8.1 (TOP)
AM_OSC_TUNE: C25.2, S1F.15 (COM), VC4.2
AM_PLATE: L11.B (PRI), V3.5
AM_RF: C23A.2, L7.2, S1C.10 (AM)
AUDIO_GRID: C38.1, R25.1, V6.1 (G)
AUDIO_PLATE: C39.1, C40.2, C42.2, R26.1, V6.7
AVC: C23A.1, C24.1, L7.1, L11.E (SEC), R17.2
B115_A: C1C.1, R13.1, R26.2, R31.2, S1D.14 (COM), V7.6 (G2)
B130: C1B.1, C43.2, R30.2, R31.1, T1.B (PRI)
B_RAW: C1A.1, C46.1, R30.1, X1.1 (K)
COAX_SHIELD_PE: C51.2, J53.2 (Ext)
DET_BOTTOM: C2.1, C35.1, M4.1 (K), R22.2
DET_D1_A: M3.1 (K), R19.2
DET_D2_A: M4.2 (A), R21.2
DET_SEC_H: L14.1 (SEC), R19.1
DET_SEC_L: L14.2 (SEC), R21.1
DET_TOP: C2.2, C34.2, M3.2 (A), R20.1
FM_ANT: C3.2, J53.1 (In)
FM_AUDIO: C37.2, R24.2, S1B.7 (FM), S1B.8 (AFC)
FM_B: C5.2, L3.2, R4.1, R8.2, R18.1, S1D.7 (FM), S1D.8 (AFC)
FM_DET_B: C33.2, L14.4 (PRI), R18.2, V5.6 (G2)
FM_DET_RAW: C34.1, C35.2, C36.2, L14.5 (TERT), R23.1, R24.1
FM_IF1_B: C10.1, L10.B (PRI), R4.2
FM_MIX_GRID: C6.1, C7.2, C8.2, C16.2, L4.1, V1.7 (G), VC1.2
FM_MIX_K: C9.2, R3.1, V1.8 (K)
FM_MIX_PLATE: L10.P (PRI), V1.6
FM_OSC_FB: C19.2, L5.3, R9.1
FM_OSC_GRID: C19.1, R9.2, V2.2 (G)
FM_OSC_PLATE: C20.2, R10.2, V2.1
FM_OSC_TANK: C15.1, C16.1, C17.2, C18.2, C20.1, L5.1, VC2.2
H12: C52.1, L15.1, V1.4 (H)
H24: L16.1, V3.3 (H)
H36: C47.1, V3.4 (H), V4.3 (H)
H48: V4.4 (H), V6.3 (H)
H60: V5.3 (H), V6.4 (H)
H72: V5.4 (H), V7.3 (H)
H_V1_IN: C49.1, L15.2, V2.5 (H)
H_V2_IN: C48.1, L16.2, V1.5 (H)
IF1_GRID: L10.G (SEC), V4.1 (G1)
IF1_K: C28.2, R12.1, V4.7 (K)
IF1_PLATE: L12.P (PRI), V4.5
IF1_SEC_RETURN: L10.E (SEC), L11.G (SEC)
IF2_GRID: L12.G (SEC), V5.1 (G1)
IF2_PLATE: L14.3 (PRI), V5.5
IF2_SEC_RETURN: C30.2, L12.E (SEC), R14.1
IF_CHAIN_MID: L12.B (PRI), L13.B (PRI)
NEON_AM: NE2.1, S1E.10 (AM)
NEON_FEED: R32.2, S1E.15 (COM)
NEON_FM: NE3.1, S1E.11 (FM), S1E.12 (AFC)
NEON_SW: NE1.1, S1E.9 (SW)
unnamed: C50.1, R33.2, V2.3 (K)
unnamed: M1.1, S2.AC2 (OUT)
OUTPUT_GRID: C42.1, R27.1, V7.2 (G1)
OUTPUT_K: R28.1, V7.1 (K)
OUTPUT_PLATE: C43.1, T1.P (PRI), V7.7
RECT_A: C46.2, R29.2, X1.2 (A)
RF_IN: C3.1, C4.1, L2.1, R2.2
RF_K: C4.2, R2.1, V1.3 (K)
RF_PLATE: C6.2, L3.1, V1.1
SP_H: SP1.1, T1.S1 (SEC)
SP_L: SP2.2, T1.S2 (SEC)
SP_MID: SP1.2, SP2.1
SW_ANT: C21.2, J2.1
SW_OSC_PAD: C26.2, S1F.9 (SW)
SW_OSC_TAP: L9.2 (TAP), S1G.1 (SW)
SW_OSC_TOP: C22B.2, C26.1, L9.1 (TOP)
SW_PRI: C21.1, L6.1 (PRI)
SW_RF: C22A.2, L6.3 (SEC), S1C.9 (SW)
TONE_LOW: C40.1, C41.2, S2.L (LOW)
TONE_MID: C41.1, S2.M (MID)
VOLUME_IN: R1.1, S1B.14 (COM)
VOLUME_W: C38.2, R1.2

Notes on the sheet:
AM_DIODE goes to V6 pins 5 and 6. The complete 12AV6 is on the audio sheet; its triode and diodes share cathode pin 2.
CHASSIS is circuit common, directly mains referenced in these source drawings. AC terminals are the radio input; external EMI filter, isolation and modern audio electronics are outside this sheet. Voltages in net names are SAMS nominal identifiers, not guaranteed measured values. L18 and L17 were r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
MODE SUPPLY AND INDICATOR LAMPS
VC1 and VC2 are mechanically ganged with VC3/VC4. Factory AFC series C11 and oscillator feedback differ from SAMS. Unspecified coil values and factory tube section-to-pin mapping need chassis verification.
455 kHz AM IF AND AM DETECTOR
Factory diodes: upper cathode faces the transformer; lower cathode faces the load. Opposite to SAMS. C2 is electrolytic.
CHASSIS is at the midpoint of R20 / R22. FM_DET_RAW is the C34 / C35 midpoint and L14 tertiary. S1A grounds AFC_CTL only in FM without AFC.
Indicator lights are absent from the final device, they're shown here as a representation of the original schematics.
AM / SW INPUT AND CONVERTER
There is no SW/AM antenna in the final build.
AUDIO AMPLIFIER
AFC / LOCAL OSCILLATOR
10.7 MHz FM IF PATH
The output transformer's secondaries are shown here in their original form. Their actual form is now what is represented in the Main Sheet.
TONE SWITCH
ORIGINAL TRANSFORMERLESS AC SUPPLY
Antenna was "upgraded" to a differential antenna : center to RF, shield to rejection. Was previously a simple wire.
IF transformers include their internal tuning capacitors. Values are not supplied by either source. See the custom symbol (capacitors added inside the can).
SW / AM LOCAL OSCILLATOR
ORIGINAL OUTPUT TRANSFORMER/SERIES SPEAKERS
Tone in BOTH sources: H=open; M=1n (two 2n in series); L=2n. SAMS M6: 13=common; 2=OFF; 3=H; 4=M; 5=L.
RATIO DETECTOR / AFC
FM RF / MIXER
All S1 units rotate together: SW / AM / FM / FM-AFC. VC1, VC2, VC3 and VC4 are one ganged tuning assembly. Logical switch and coil terminals require a physical lug crosscheck.
SERIES HEATER STRING - ALL SEVEN TUBES
