Z3r0shin/ambersong/hardware/schematics/Ambersong - MAIN MCU ESP32-S3 N16R8.kicad_sch

## KiCad design hardware/schematics/Ambersong - MAIN MCU ESP32-S3 N16R8.kicad_sch (2026-09-28)

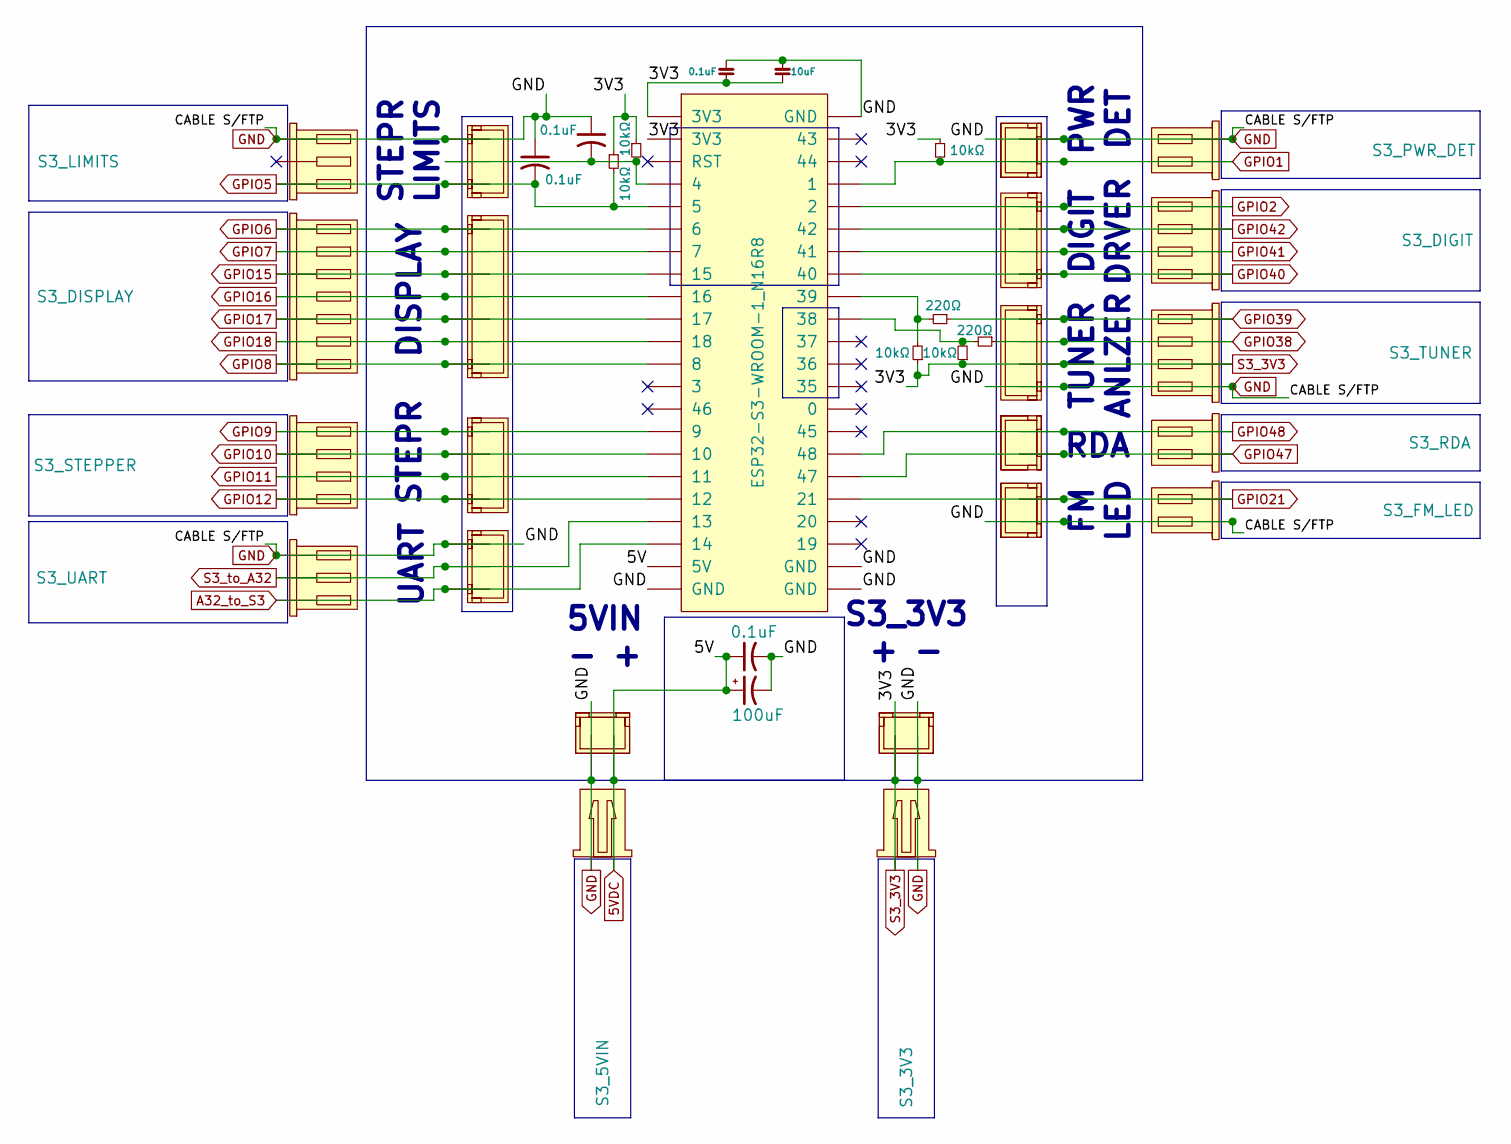
[picture p89: schematic Ambersong - MAIN MCU ESP32-S3 N16R8.kicad_sch]

Parts:
0.1uF: C_Small_US
10kΩ, 220Ω: R_Small_US
100uF: C_Polarized_Small_US
C45: 0.1uF
C53: 10uF
S3_3V3, S3_5VIN, S3_DIGIT, S3_DISPLAY, S3_FM_LED, S3_LIMITS, S3_PWR_DET, S3_RDA, S3_STEPPER, S3_TUNER, S3_UART: (no value)
U62, U64, U65, U66, U67, U68, U69, U70, U72, U73, U91: (no value)
U63: ESP32-S3-WROOM-1_N16R8

Connections:
5VDC: 0.1uF.1, 100uF.1, S3_5VIN., U63., U72.
A32_to_S3: S3_UART., U63., U69.
GND: 0.1uF.1, 0.1uF.2, 100uF.2, C45.2, C53.2, S3_3V3., S3_5VIN., S3_FM_LED., S3_LIMITS., S3_PWR_DET., S3_TUNER., S3_UART., U62., U63., U64., U66., U69., U70., U72., U73.
GPIO1: 10kΩ.2, S3_PWR_DET., U63., U64.
GPIO2: S3_DIGIT., U63., U67.
GPIO5: 0.1uF.2, 10kΩ.2, S3_LIMITS., U63., U70.
GPIO6: S3_DISPLAY., U63., U68.
GPIO7: S3_DISPLAY., U63., U68.
GPIO8: S3_DISPLAY., U63., U68.
GPIO9: S3_STEPPER., U63., U65.
GPIO10: S3_STEPPER., U63., U65.
GPIO11: S3_STEPPER., U63., U65.
GPIO12: S3_STEPPER., U63., U65.
GPIO15: S3_DISPLAY., U63., U68.
GPIO16: S3_DISPLAY., U63., U68.
GPIO17: S3_DISPLAY., U63., U68.
GPIO18: S3_DISPLAY., U63., U68.
GPIO21: S3_FM_LED., U62., U63.
GPIO38: 220Ω.1, S3_TUNER., U66.
GPIO39: 220Ω.1, S3_TUNER., U66.
GPIO40: S3_DIGIT., U63., U67.
GPIO41: S3_DIGIT., U63., U67.
GPIO42: S3_DIGIT., U63., U67.
GPIO47: S3_RDA., U63., U91.
GPIO48: S3_RDA., U63., U91.
unnamed: 0.1uF.2, 10kΩ.2, U63., U70.
unnamed: 10kΩ.2, 220Ω.2, U63.
S3_3V3: 10kΩ.1, C45.1, C53.1, S3_3V3., S3_TUNER., U63., U66., U73.
S3_to_A32: S3_UART., U63., U69.

Notes on the sheet:
DIGIT DRVER
S3_3V3 + -
STEPR LIMITS
5VIN - +
PWR DET
STEPR
UART
RDA
DISPLAY
TUNER ANLZER
FM LED
