Z3r0shin/ambersong/hardware/schematics/Ambersong - P-MOSFET DIGITS & P-MOSFET DIGIT DRIVER & 7 SEGMENTS BUS DRIVER.kicad_sch

## KiCad design hardware/schematics/Ambersong - P-MOSFET DIGITS & P-MOSFET DIGIT DRIVER & 7 SEGMENTS BUS DRIVER.kicad_sch (2026-09-28)

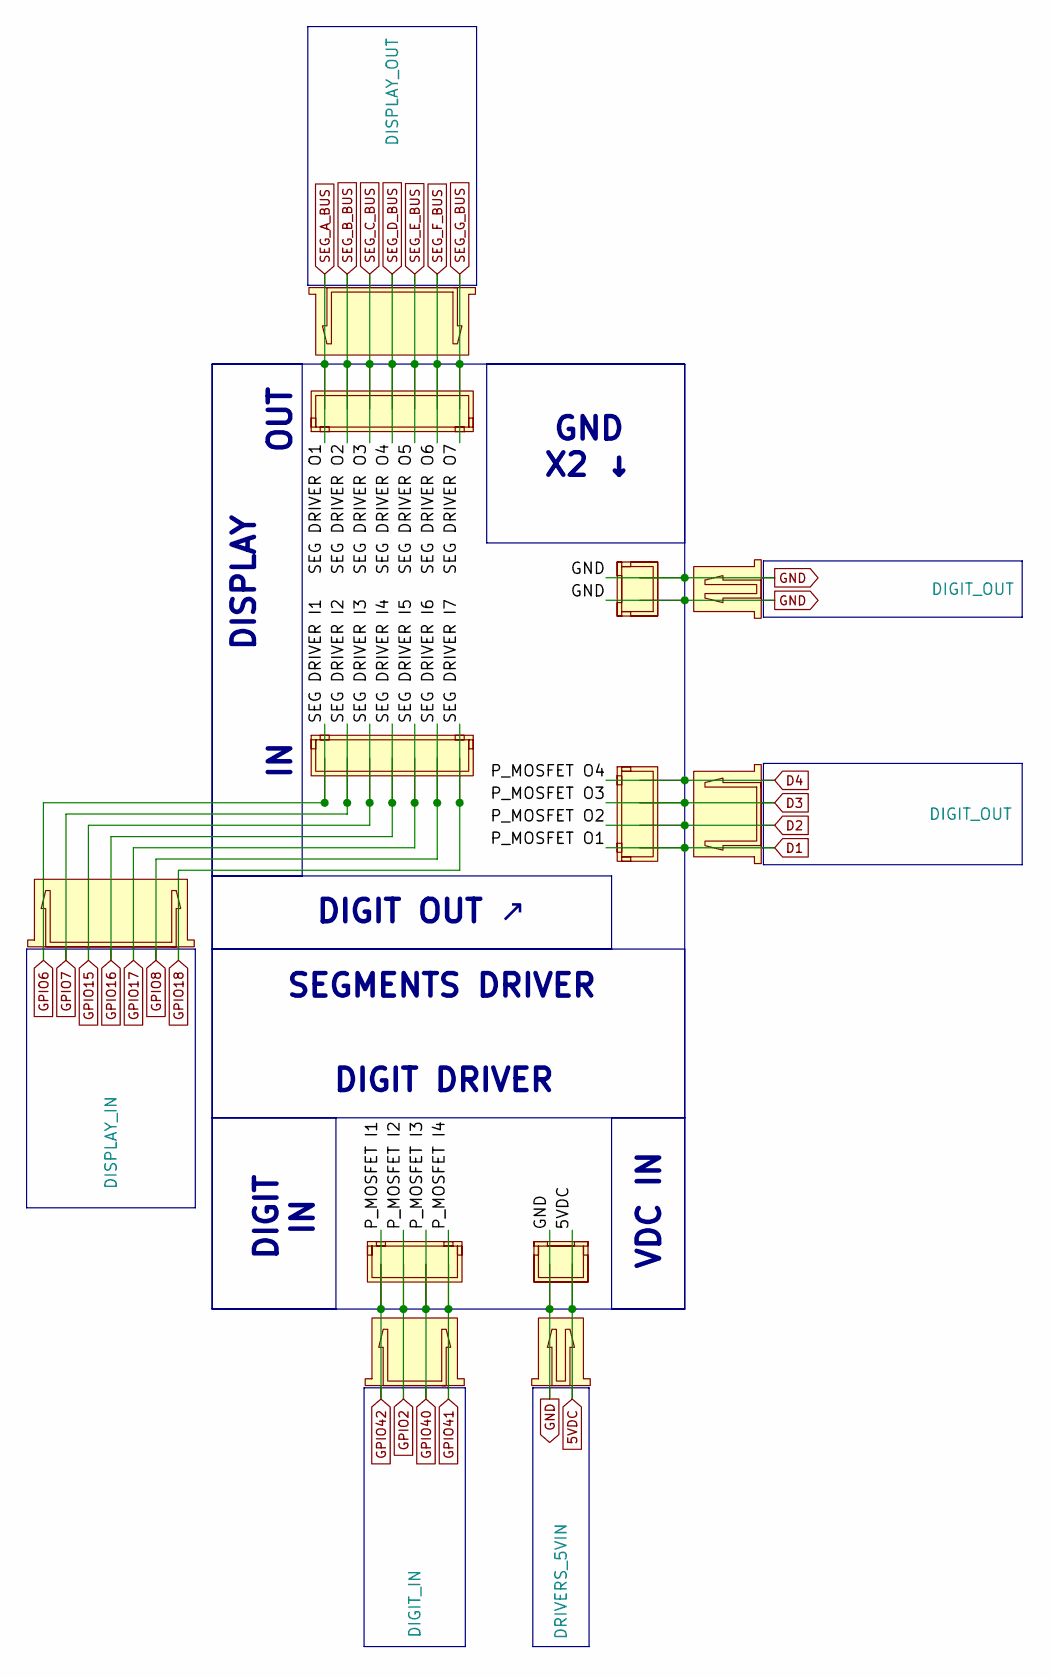
[picture p90: schematic Ambersong - P-MOSFET DIGITS & P-MOSFET DIGIT DRIVER & 7 SEGMENTS BUS DRIVER.kicad_sch]

Parts:
DIGIT_IN: (no value)
DIGIT_OUT: (no value)
DISPLAY_IN: (no value)
DISPLAY_OUT: (no value)
DRIVERS_5VIN: (no value)
U20, U22, U24, U26, U28, U29: (no value)

Connections:
5VDC: DRIVERS_5VIN., U28.
D1: DIGIT_OUT., U26.
D2: DIGIT_OUT., U26.
D3: DIGIT_OUT., U26.
D4: DIGIT_OUT., U26.
GND: DIGIT_OUT., DRIVERS_5VIN., U22., U28.
GPIO2: DIGIT_IN., U29.
GPIO6: DISPLAY_IN., U24.
GPIO7: DISPLAY_IN., U24.
GPIO8: DISPLAY_IN., U24.
GPIO15: DISPLAY_IN., U24.
GPIO16: DISPLAY_IN., U24.
GPIO17: DISPLAY_IN., U24.
GPIO18: DISPLAY_IN., U24.
GPIO40: DIGIT_IN., U29.
GPIO41: DIGIT_IN., U29.
GPIO42: DIGIT_IN., U29.
SEG_A_BUS: DISPLAY_OUT., U20.
SEG_B_BUS: DISPLAY_OUT., U20.
SEG_C_BUS: DISPLAY_OUT., U20.
SEG_D_BUS: DISPLAY_OUT., U20.
SEG_E_BUS: DISPLAY_OUT., U20.
SEG_F_BUS: DISPLAY_OUT., U20.
SEG_G_BUS: DISPLAY_OUT., U20.

Notes on the sheet:
DIGIT OUT ↗
DISPLAY IN OUT
GND X2 ↓
DIGIT IN
DIGIT DRIVER
VDC IN
SEGMENTS DRIVER
