Z3r0shin/ambersong/hardware/schematics/Ambersong - PANEL RADIO LED PWM CONTROL.kicad_sch

## KiCad design hardware/schematics/Ambersong - PANEL RADIO LED PWM CONTROL.kicad_sch (2026-09-28)

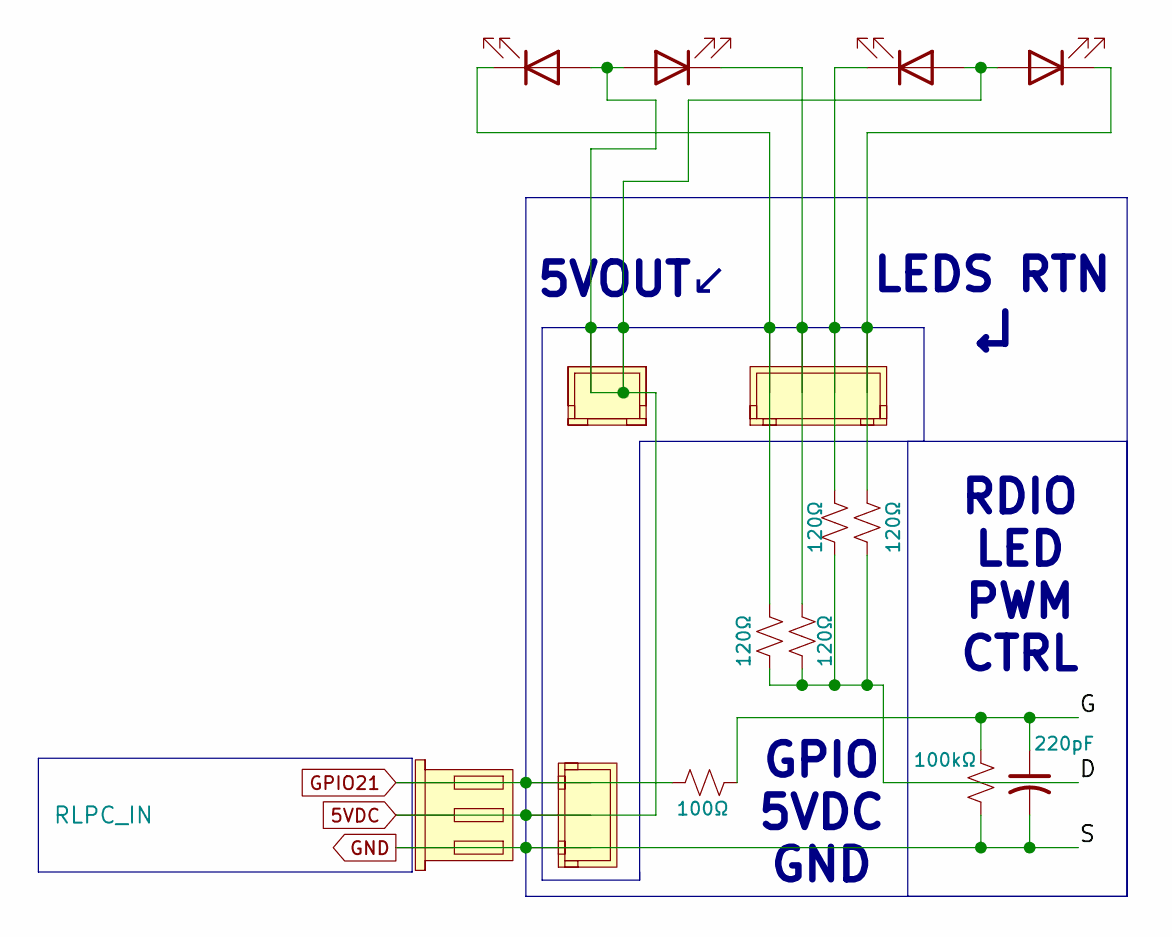
[picture p91: schematic Ambersong - PANEL RADIO LED PWM CONTROL.kicad_sch]

Parts:
100kΩ, 100Ω, 120Ω: R_Small_US
220pF: C_Small_US
D46, D47, D48, D49: LED
RLPC_IN: (no value)
U82, U85, U86: (no value)

Connections:
5VDC: D46.2 (A), D47.2 (A), D48.2 (A), D49.2 (A), RLPC_IN., U82., U85.
D: 120Ω.1
G: 100kΩ.2, 100Ω.1, 220pF.1
GND: 100kΩ.1, 220pF.2, RLPC_IN., U82.
GPIO21: 100Ω.2, RLPC_IN., U82.
unnamed: 120Ω.2, D46.1 (K), D47.1 (K), D48.1 (K), D49.1 (K), U86.

Notes on the sheet:
RDIO LED PWM CTRL
GPIO 5VDC GND
5VOUT↙
LEDS RTN
