Z3r0shin/ambersong/hardware/schematics/Ambersong - PCM1802 ADC & TUBE RADIO AUDIO JACK IN INTO PCM1802.kicad_sch

## KiCad design hardware/schematics/Ambersong - PCM1802 ADC & TUBE RADIO AUDIO JACK IN INTO PCM1802.kicad_sch (2026-09-28)

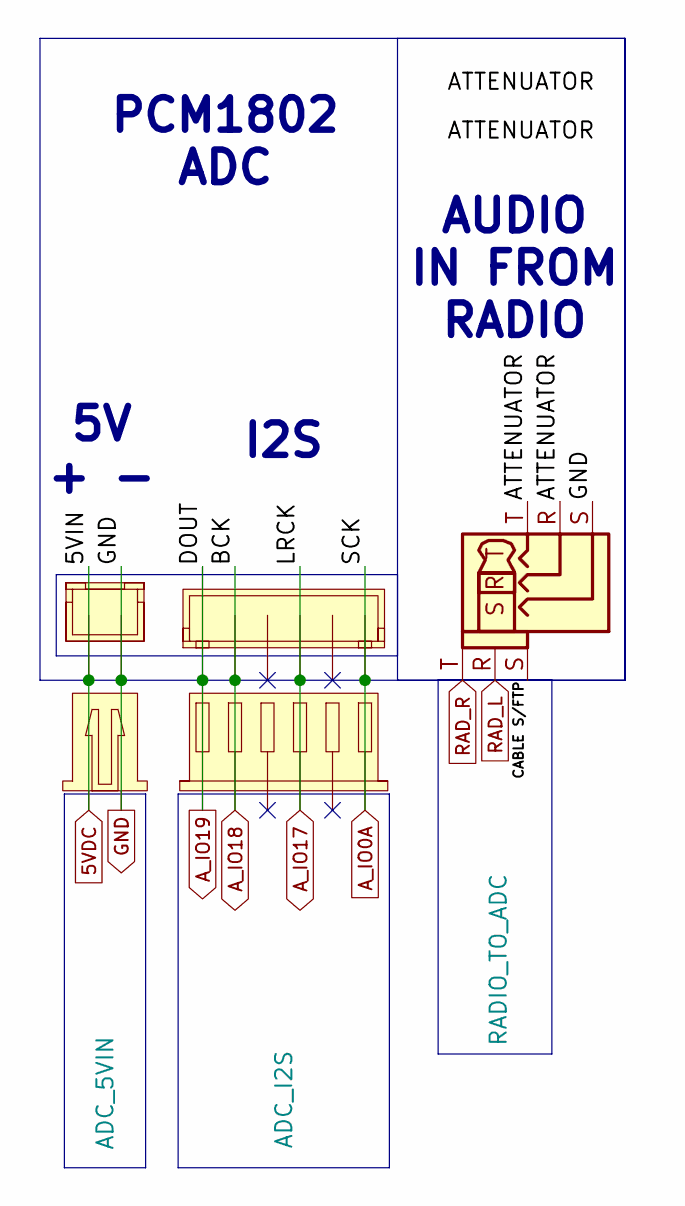
[picture p92: schematic Ambersong - PCM1802 ADC & TUBE RADIO AUDIO JACK IN INTO PCM1802.kicad_sch]

Parts:
ADC_5VIN: (no value)
ADC_I2S: (no value)
RADIO_TO_ADC: AudioJack3
U21, U23: (no value)

Connections:
5VDC: ADC_5VIN., U21.
ATTENUATOR: RADIO_TO_ADC.R, RADIO_TO_ADC.T
A_IO0A: ADC_I2S., U23.
A_IO17: ADC_I2S., U23.
A_IO18: ADC_I2S., U23.
A_IO19: ADC_I2S., U23.
CABLE S/FTP: RADIO_TO_ADC.S
GND: ADC_5VIN., RADIO_TO_ADC.S, U21.
RAD_L: RADIO_TO_ADC.R
RAD_R: RADIO_TO_ADC.T

Notes on the sheet:
I2S
5V + -
PCM1802 ADC
AUDIO IN FROM RADIO
