Z3r0shin/ambersong/hardware/schematics/Ambersong - PCM5102A DAC.kicad_sch

## KiCad design hardware/schematics/Ambersong - PCM5102A DAC.kicad_sch (2026-09-28)

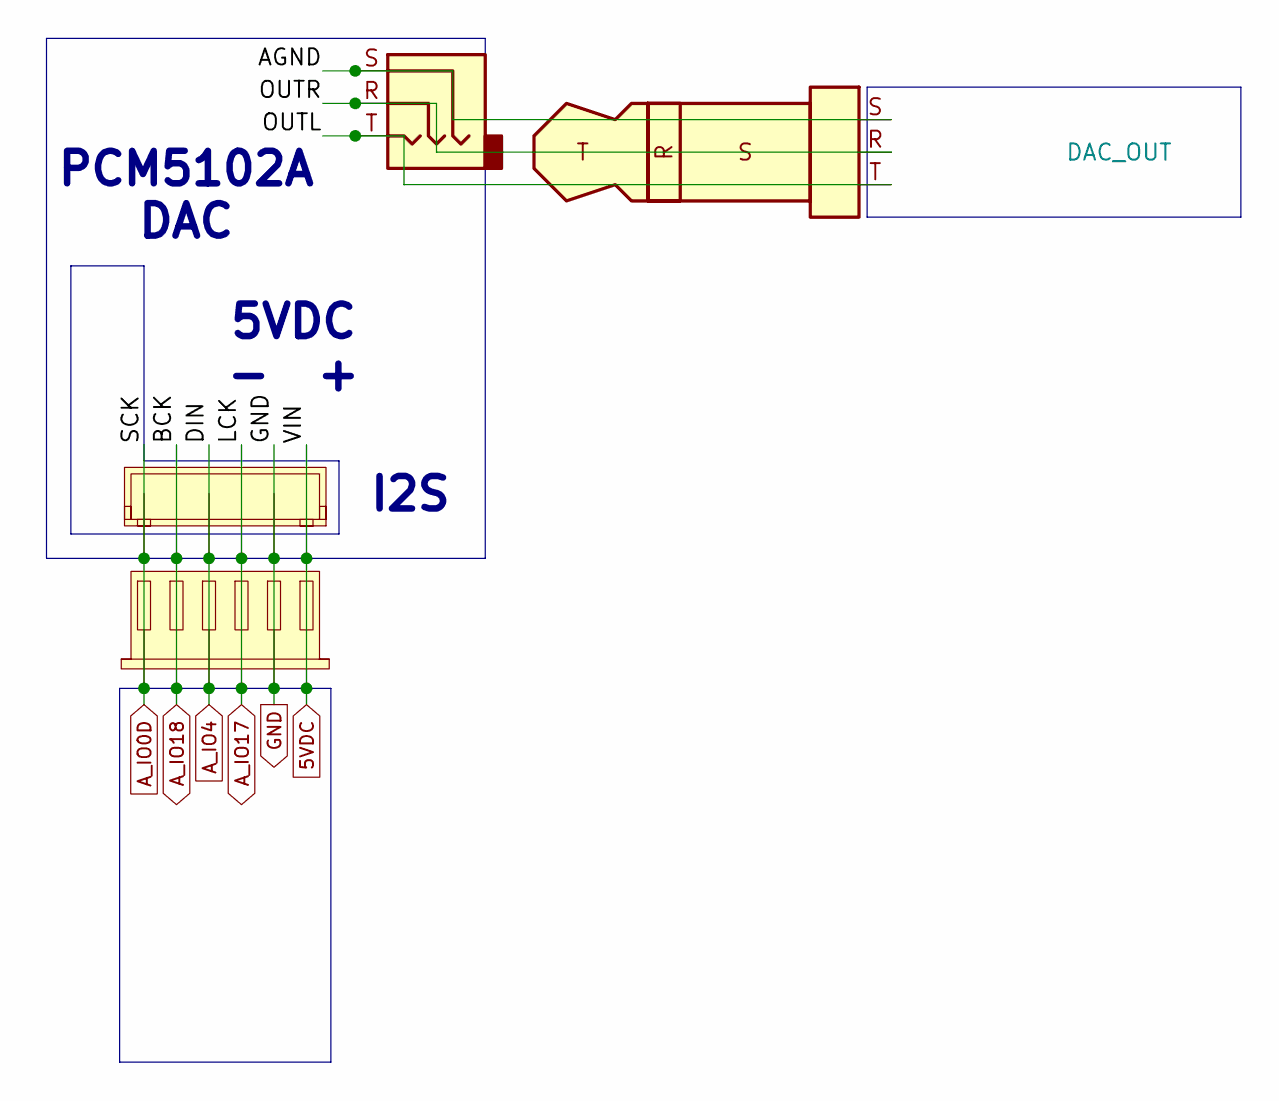
[picture p93: schematic Ambersong - PCM5102A DAC.kicad_sch]

Parts:
J40: DAC_OUT
J43: AudioJack3
U13, U14: (no value)

Connections:
5VDC: U13., U14.
AGND: J40.S, J43.S
A_IO0D: U13., U14.
A_IO4: U13., U14.
A_IO17: U13., U14.
A_IO18: U13., U14.
GND: U13., U14.
OUTL: J40.T, J43.T
OUTR: J40.R, J43.R

Notes on the sheet:
5VDC - +
PCM5102A DAC
I2S
