Z3r0shin/ambersong/hardware/schematics/Ambersong - POWER DETECT.kicad_sch

## KiCad design hardware/schematics/Ambersong - POWER DETECT.kicad_sch (2026-09-28)

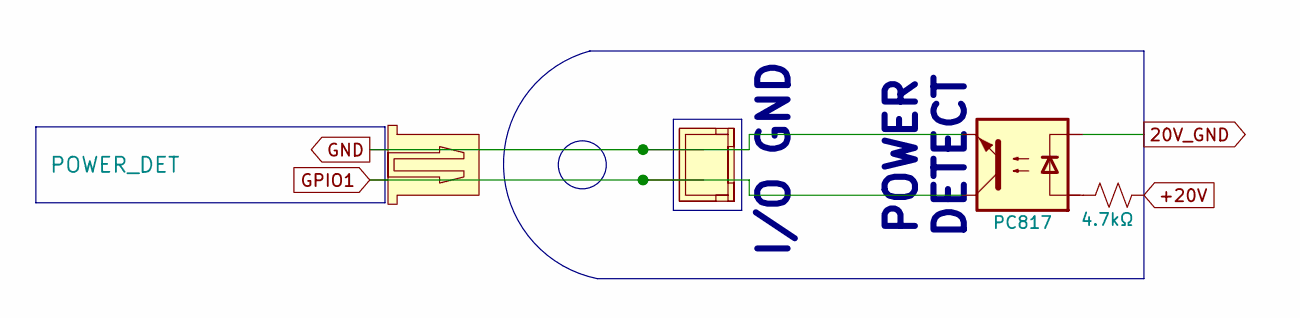
[picture p94: schematic Ambersong - POWER DETECT.kicad_sch]

Parts:
4.7kΩ: R_Small_US
POWER_DET: (no value)
U83: PC817; DIP-4_W7.62mm
U84: (no value)

Connections:
20V_GND: U83.
+20V: 4.7kΩ.2
GND: POWER_DET., U83., U84.
GPIO1: POWER_DET., U83., U84.
unnamed: 4.7kΩ.1, U83.

Notes on the sheet:
POWER DETECT
I/O GND
