Z3r0shin/ambersong/hardware/schematics/Ambersong - RDA5807M.kicad_sch

## KiCad design hardware/schematics/Ambersong - RDA5807M.kicad_sch (2026-09-28)

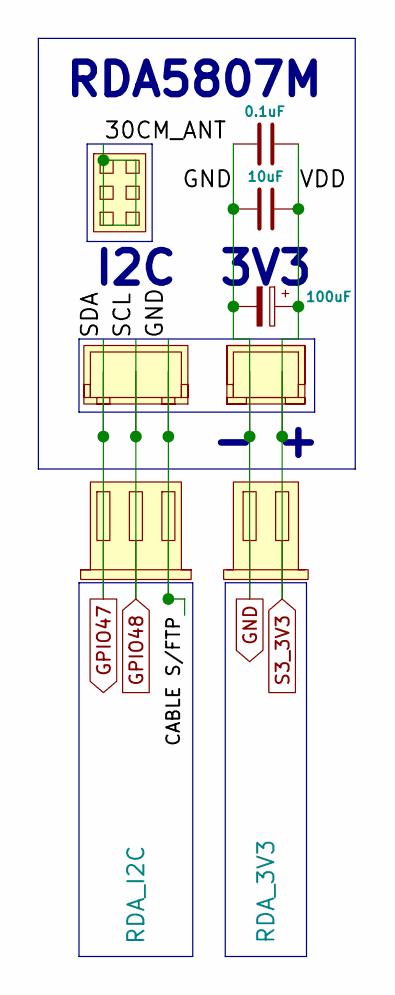
[picture p95: schematic Ambersong - RDA5807M.kicad_sch]

Parts:
C18: 100uF
C19: 0.1uF
C31: 10uF
RDA_3V3: (no value)
RDA_I2C: (no value)
U71, U92, U93: (no value)

Connections:
GND: C18.2, C19.2, C31.2, RDA_3V3., RDA_I2C., U92., U93.
GPIO47: RDA_I2C., U92.
GPIO48: RDA_I2C., U92.
S3_3V3: C18.1, C19.1, C31.1, RDA_3V3., U93.

Notes on the sheet:
3V3
I2C
RDA5807M
- +
