Z3r0shin/ambersong/hardware/schematics/Ambersong - STAR POINT VDC & GND JST XH BUSES.kicad_sch

## KiCad design hardware/schematics/Ambersong - STAR POINT VDC & GND JST XH BUSES.kicad_sch (2026-09-28)

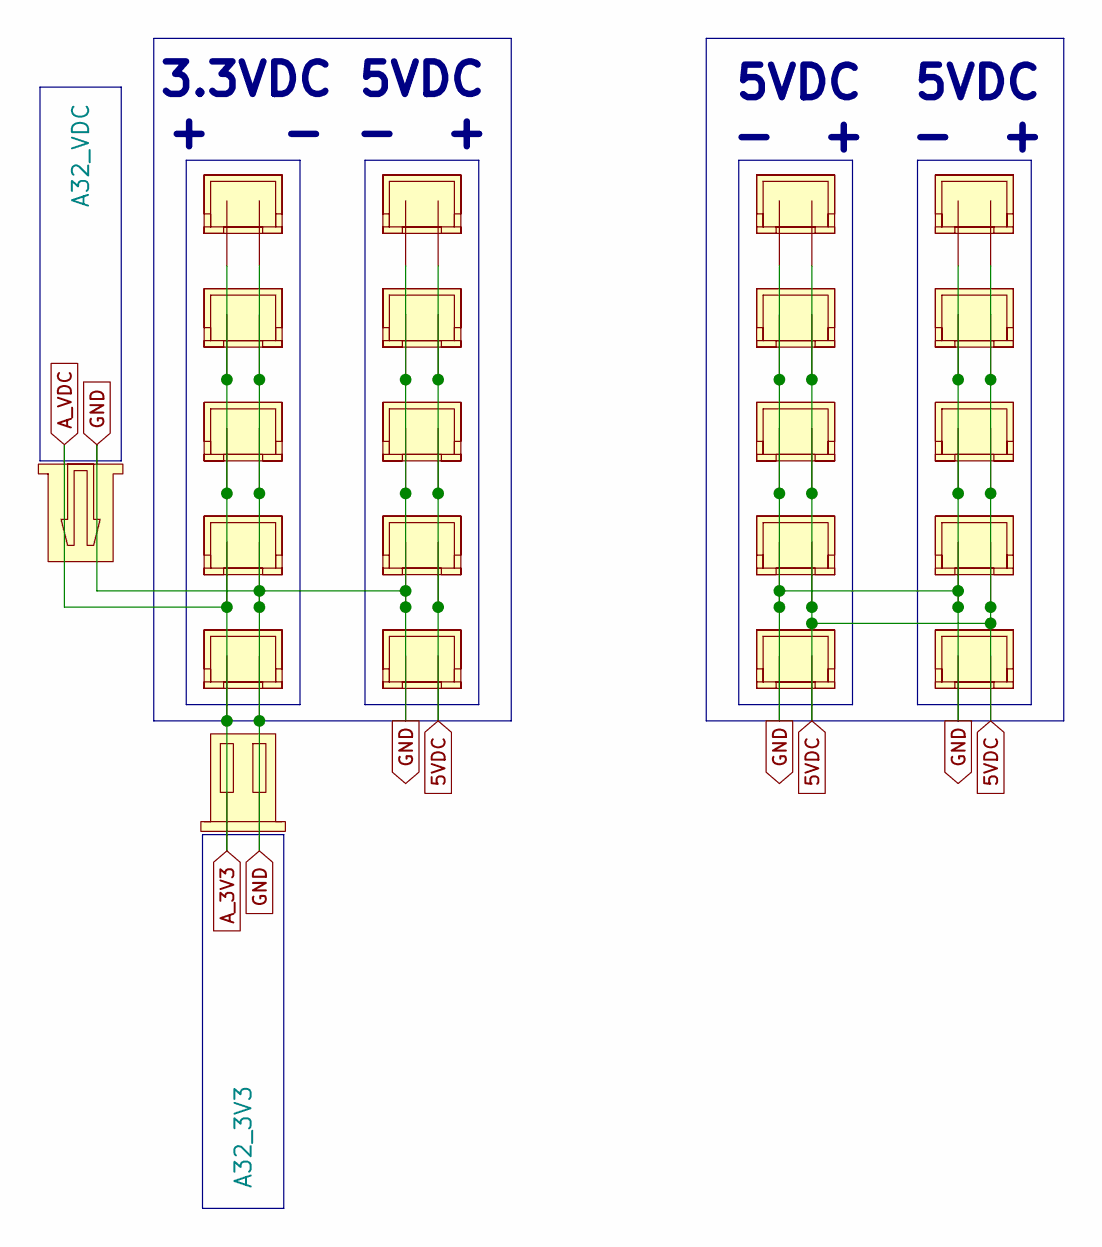
[picture p96: schematic Ambersong - STAR POINT VDC & GND JST XH BUSES.kicad_sch]

Parts:
A32_3V3, A32_VDC: (no value)
U25, U27, U30, U31, U46, U47, U48, U49, U50, U51, U52, U53, U54, U55, U56, U57, U58, U59, U60, U61: (no value)

Connections:
5VDC: U25., U27., U30., U31., U46., U47., U48., U49., U50., U51., U57., U58., U59., U60., U61.
A_3V3: A32_3V3., A32_VDC., U52., U53., U54., U55., U56.
GND: A32_3V3., A32_VDC., U25., U27., U30., U31., U46., U47., U48., U49., U50., U51., U52., U53., U54., U55., U56., U57., U58., U59., U60., U61.

Notes on the sheet:
5VDC - +
3.3VDC + -
