Z3r0shin/ambersong/hardware/schematics/Ambersong - STEPPER DRIVER.kicad_sch

## KiCad design hardware/schematics/Ambersong - STEPPER DRIVER.kicad_sch (2026-09-28)

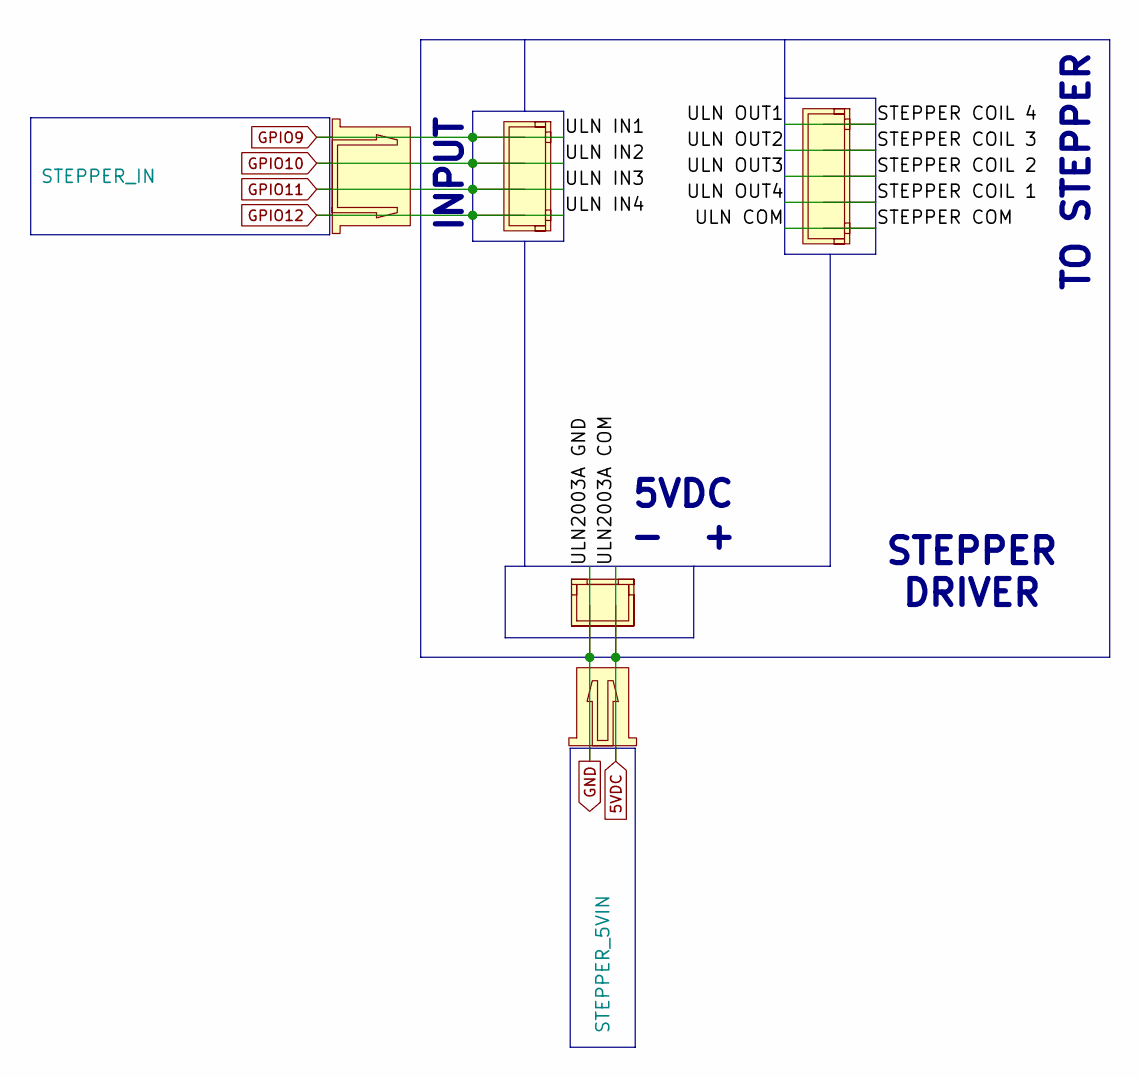
[picture p97: schematic Ambersong - STEPPER DRIVER.kicad_sch]

Parts:
STEPPER_5VIN: (no value)
STEPPER_IN: (no value)
U37, U38, U39: (no value)

Connections:
5VDC: STEPPER_5VIN., U37.
GND: STEPPER_5VIN., U37.
GPIO9: STEPPER_IN., U38.
GPIO10: STEPPER_IN., U38.
GPIO11: STEPPER_IN., U38.
GPIO12: STEPPER_IN., U38.
STEPPER COIL 1: U39.
STEPPER COIL 2: U39.
STEPPER COIL 3: U39.
STEPPER COIL 4: U39.
STEPPER COM: U39.

Notes on the sheet:
TO STEPPER
STEPPER DRIVER
INPUT
5VDC - +
