Z3r0shin/ambersong/hardware/schematics/Ambersong - STEPPER LIMIT.kicad_sch

## KiCad design hardware/schematics/Ambersong - STEPPER LIMIT.kicad_sch (2026-09-28)

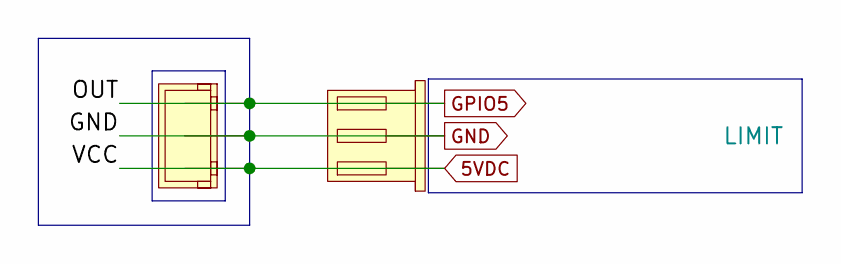
[picture p98: schematic Ambersong - STEPPER LIMIT.kicad_sch]

Parts:
LIMIT: (no value)
U90: (no value)

Connections:
5VDC: LIMIT., U90.
GND: LIMIT., U90.
GPIO5: LIMIT., U90.
