Z3r0shin/ambersong/hardware/schematics/Ambersong - USB-C CONNECTORS.kicad_sch

## KiCad design hardware/schematics/Ambersong - USB-C CONNECTORS.kicad_sch (2026-09-28)

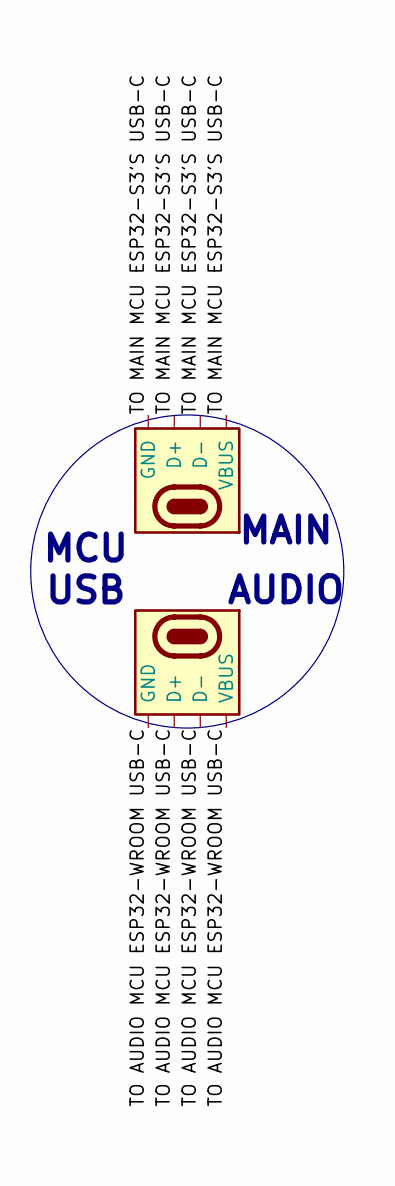
[picture p99: schematic Ambersong - USB-C CONNECTORS.kicad_sch]

Parts:
P1, P2: USB_C_Plug_USB2.0

Connections:
unnamed: P1.A12 (GND), P1.B1 (GND), P1.B12 (GND)
unnamed: P2.A12 (GND), P2.B1 (GND), P2.B12 (GND)
TO AUDIO MCU ESP32-WROOM USB-C: P1. (VBUS)
TO MAIN MCU ESP32-S3'S USB-C: P2. (VBUS)

Notes on the sheet:
MCU USB
MAIN
AUDIO
