Z3r0shin/ambersong/hardware/schematics/Ambersong.kicad_sch

## KiCad design hardware/schematics/Ambersong.kicad_sch (2026-09-28)

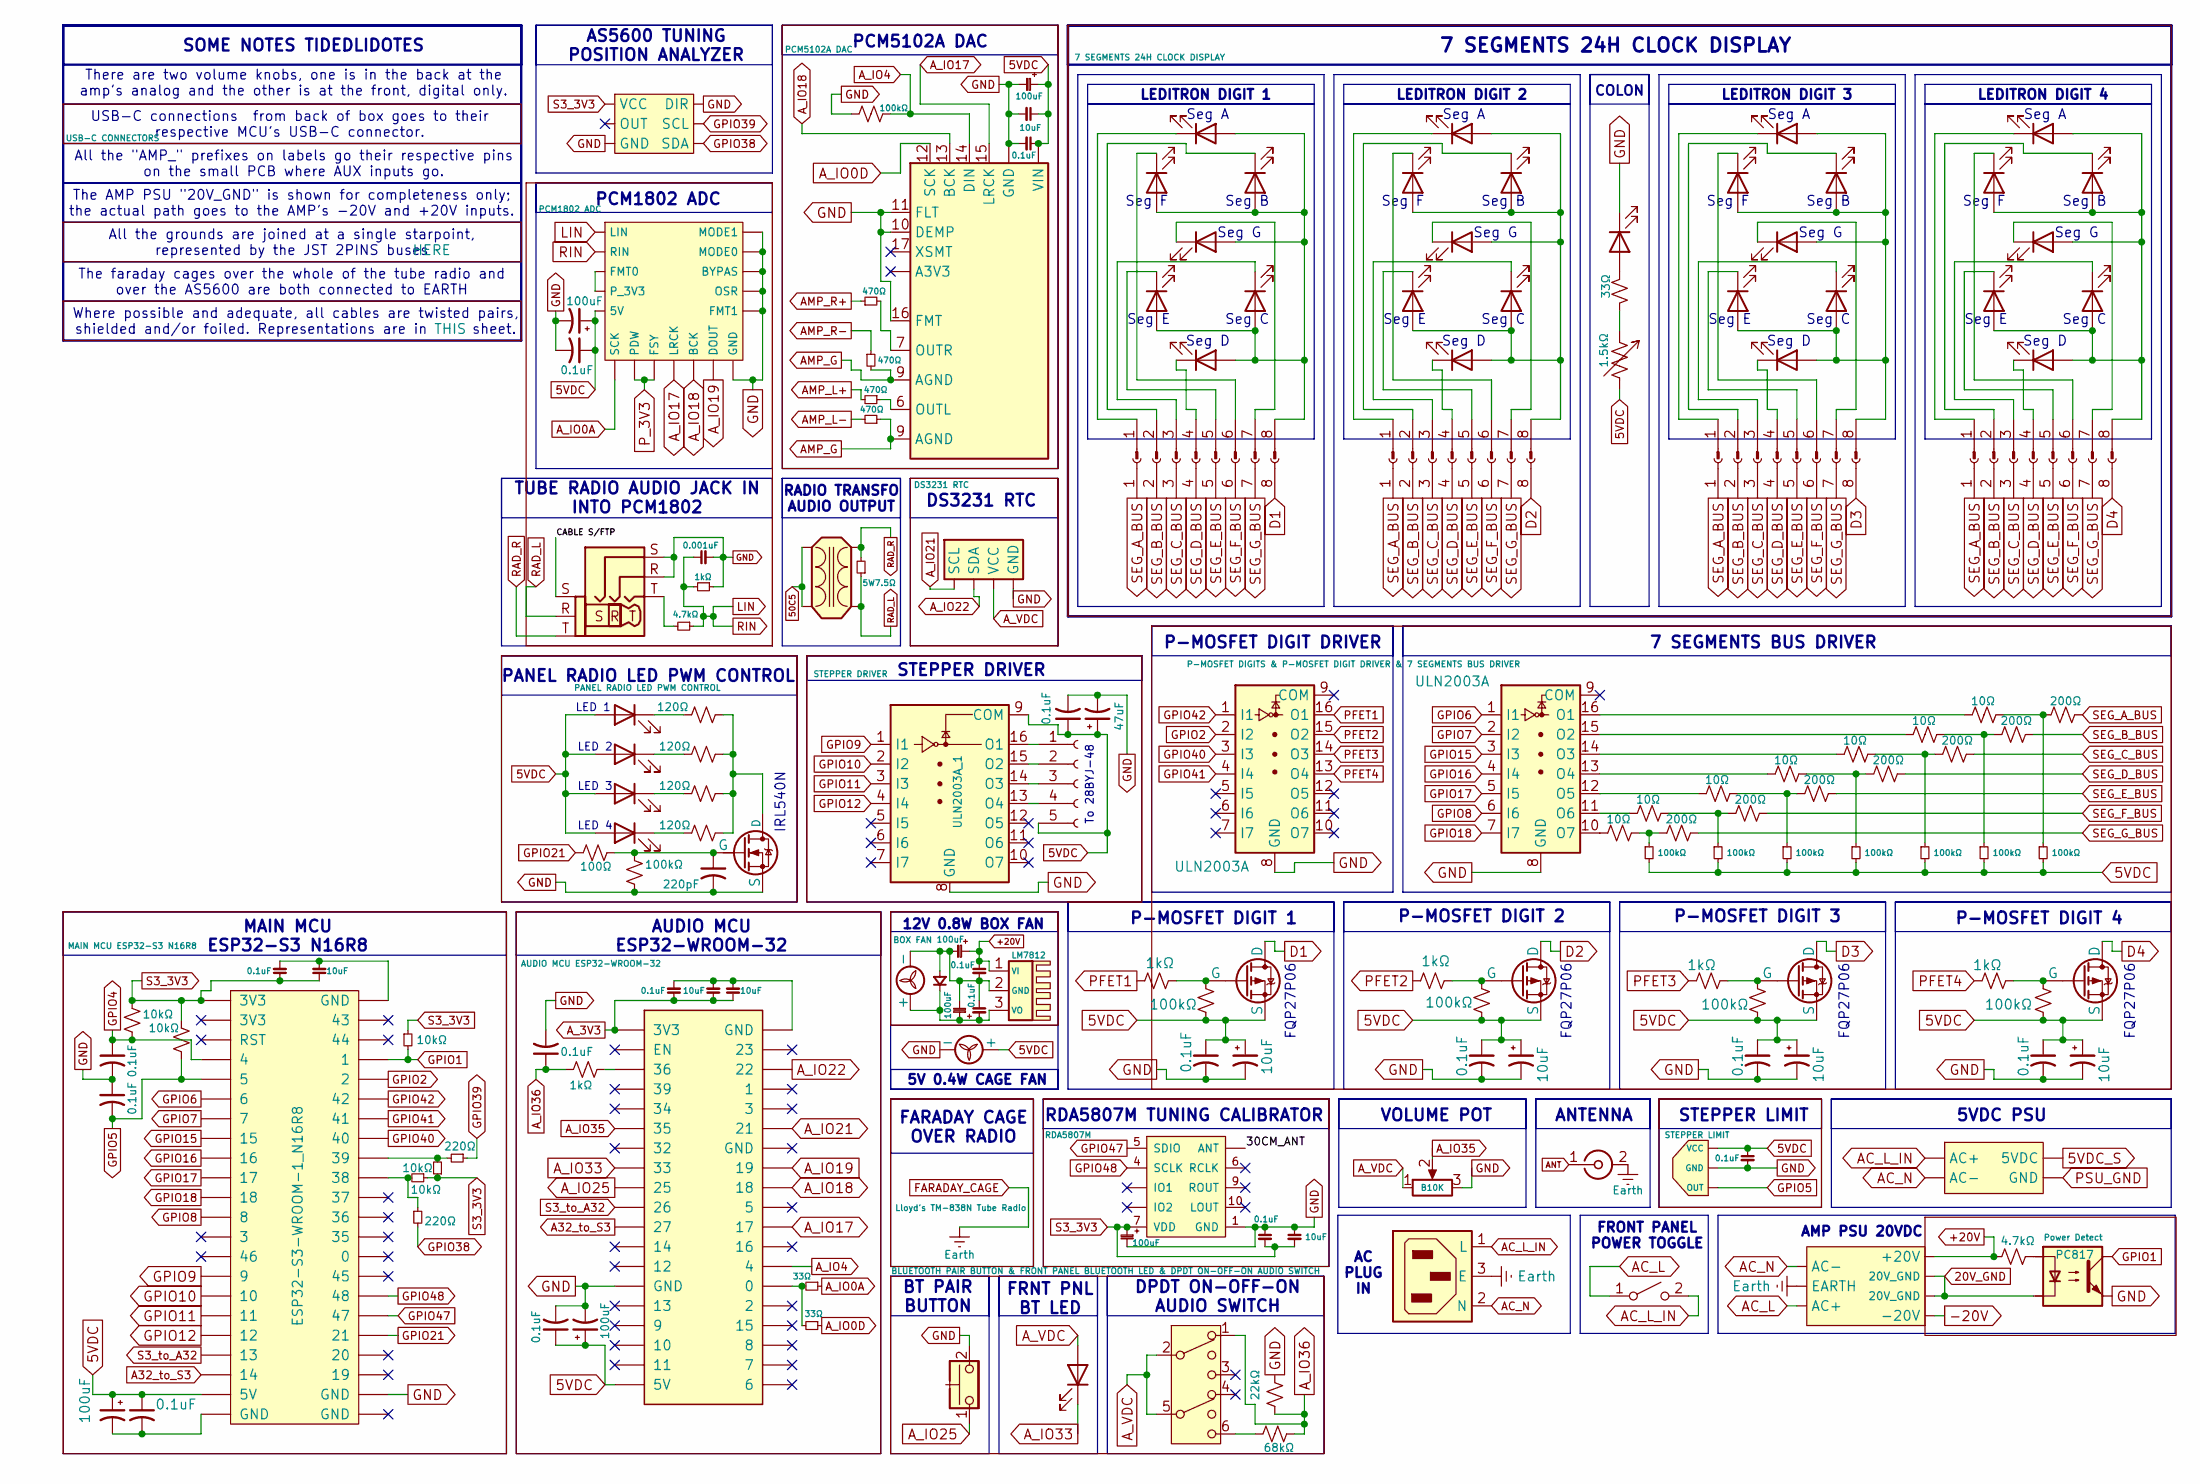
[picture p100: schematic Ambersong.kicad_sch]

Parts:
0.1uF, 220pF: C_Small_US
1kΩ, 4.7kΩ, 10kΩ, 10Ω, 22kΩ, 33Ω, 68kΩ, 100kΩ, 100Ω, 120Ω, 200Ω, 220Ω, 470Ω: R_Small_US
7.5Ω: 5W7.5Ω
10uF, 47uF, 100uF: C_Polarized_Small_US
C13, C14, C17, C20, C23, C26, C29: 0.1uF
C15, C16, C27, C28: 100uF
C21, C22, C24, C25, C30: 10uF
C59: 0.001uF
COLON1: LED
D1, D2, D3, D4, D5, D6, D7, D8, D9, D10, D11, D12, D13, D14, D15, D16, D17, D18, D19, D20, D21, D22, D23, D24, D25, D26, D27, D28, D29, D30, D31, D32, D33: LED
D34: 1N4148; DIOAD753W49L380D172B; PARTREV 5
DPDT_ON_OFF_ON: (no value)
J1, J3, J4, J8: Conn_01x08_Pin
J2, J5, J6, J7: Conn_01x08_Socket
J9: Conn_01x05_Socket
J10: Conn_Coaxial
J30: IEC_60320_C14_Receptacle
J51: AudioJack3
M1, M2: Fan
P-Mosfet: FQP27P06
PCM1802: (no value)
PFet1, PFet2, PFet3: FQP27P06
Q1: IRL540N
R17: 1.5kΩ
RV4: B10K
SW1: SW_SPST
SW2: SW_Push_Shielded
T1: TUBE RADIO TRANSFORMER AUDIO OUTPUT
U1, U4, U11: (no value)
U2, U5: ULN2003A
U3: ULN2003A_1
U6: PC817; DIP-4_W7.62mm
U7: ESP32-S3-WROOM-1_N16R8
U8: DS3231M; SOIC-16W_7.5x10.3mm_P1.27mm
U9: PCM5102A; TSSOP-20_4.4x6.5mm_P0.65mm
U10: ESP32-DevKitC_2; ESP32-DevKitC
U40: LM7812; TO-220-3_Vertical
U42: A3144; TO-92S
U89: RDA5807M

Connections:
5VDC: 0.1uF.1, 10uF.1, 47uF.1, 100kΩ.2, 100uF.1, C17.1, C24.1, C26.1, C27.1, D30.2 (A), D31.2 (A), D32.2 (A), D33.2 (A), J9.5, M2., P-Mosfet.3 (S), PCM1802., PFet1.3 (S), PFet2.3 (S), PFet3.3 (S), R17.2, U3.9 (COM), U7., U9. (A3V3), U10., U42.
5VDC_S: U4.
20V_GND: U1., U6.
30CM_ANT: U89. (IO1)
50C5: T1.
+20V: 4.7kΩ.2, C14.1, C15.1, U1., U40.1 (VI)
-20V: U1.
A32_to_S3: U7., U10.
AC_L: SW1.1 (A), U1.
AC_L_IN: J30.1 (L), SW1.2 (B), U4.
AC_N: J30.2 (N), U1., U4.
AMP_G: 470Ω.1, 470Ω.2, U9.9 (AGND)
AMP_L+: 470Ω.2
AMP_L-: 470Ω.2
AMP_R+: 470Ω.1
AMP_R-: 470Ω.1
ANT: J10.1 (In)
A_3V3: C20.1, C21.1, C22.1, U10.
A_IO0A: 33Ω.1, PCM1802.
A_IO0D: 33Ω.1, U9.12 (SCK)
A_IO4: 100kΩ.1, U9.14 (DIN), U10.
A_IO17: PCM1802., U9.15 (LRCK), U10.
A_IO18: PCM1802., U9.13 (BCK), U10.
A_IO19: PCM1802., U10.
A_IO21: U8. (SCL), U10.
A_IO22: U8. (SCL), U10.
A_IO25: SW2.1, U10.
A_IO33: D29.1 (K), U10.
A_IO35: RV4.2, U10.
A_IO36: 0.1uF.1, 1kΩ.1, 22kΩ.1, 68kΩ.1, DPDT_ON_OFF_ON.1 (A)
A_VDC: D29.2 (A), DPDT_ON_OFF_ON.2 (B), DPDT_ON_OFF_ON.5 (B), RV4.1, U8. (SCL)
CABLE S/FTP: J51.S
D1: J5.8, P-Mosfet.1 (D)
D2: J7.8, PFet1.1 (D)
D3: J6.8, PFet2.1 (D)
D4: J2.8, PFet3.1 (D)
Earth: J10.2 (Ext), J30.3 (E), U1.
GND: 0.1uF.1, 0.1uF.2, 1kΩ.1, 10uF.2, 22kΩ.2, 47uF.2, 100kΩ.1, 100kΩ.2, 100uF.2, 220pF.2, C17.2, C24.2, C26.2, C27.2, C28.2, C29.1, C30.1, C59.2, COLON1.1 (K), J51.R, J51.S, M2., PCM1802., Q1.3 (S), RV4.3, SW2.2, U2.8 (GND), U3.8 (GND), U5.8 (GND), U6., U7., U8. (SCL), U9. (A3V3), U9.10 (DEMP), U9.11 (FLT), U9.16 (FMT), U10., U11., U42., U89.1 (GND)
GPIO1: 10kΩ.2, U6., U7.
GPIO2: U5.2 (I2), U7.
GPIO4: 0.1uF.1, 10kΩ.2, U7.
GPIO5: 0.1uF.2, 10kΩ.2, U7., U42.
GPIO6: U2.1 (I1), U7.
GPIO7: U2.2 (I2), U7.
GPIO8: U2.6 (I6), U7.
GPIO9: U3.1 (I1), U7.
GPIO10: U3.2 (I2), U7.
GPIO11: U3.3 (I3), U7.
GPIO12: U3.4 (I4), U7.
GPIO15: U2.3 (I3), U7.
GPIO16: U2.4 (I4), U7.
GPIO17: U2.5 (I5), U7.
GPIO18: U2.7 (I7), U7.
GPIO21: 100Ω.2, U7.
GPIO38: 220Ω.2, U11.
GPIO39: 220Ω.1, U11.
GPIO40: U5.3 (I3), U7.
GPIO41: U5.4 (I4), U7.
GPIO42: U5.1 (I1), U7.
GPIO47: U7., U89.5 (SDIO)
GPIO48: U7., U89.4 (SCLK)
LIN: 1kΩ.2, 4.7kΩ.1, C59.1, PCM1802.
unnamed: 0.1uF.2, 100uF.2, U7.
unnamed: 1kΩ.2, U10.
unnamed: 4.7kΩ.1, U6.
unnamed: 4.7kΩ.2, J51.T
unnamed: 10kΩ.2, 220Ω.1, 220Ω.2, U7.
unnamed: 10Ω.2, U2.10 (O7), U2.11 (O6), U2.12 (O5), U2.13 (O4), U2.14 (O3), U2.15 (O2), U2.16 (O1)
unnamed: 33Ω.1, R17.1
unnamed: 33Ω.2, COLON1.2 (A), U10.
unnamed: 68kΩ.2, DPDT_ON_OFF_ON.6 (C)
unnamed: 1kΩ.1, 10Ω.1, 100kΩ.1, 200Ω.2, P-Mosfet.2 (G), PFet1.2 (G), PFet2.2 (G), PFet3.2 (G)
unnamed: 100kΩ.2, 100Ω.1, 220pF.1, Q1.2 (G)
unnamed: 120Ω.1, Q1.1 (D)
unnamed: 120Ω.2, D30.1 (K), D31.1 (K), D32.1 (K), D33.1 (K)
unnamed: 470Ω.1, U9.6 (OUTL)
unnamed: 470Ω.2, U9.7 (OUTR)
unnamed: C13.1, C14.2, C15.2, C16.2, D34., M1., U40.2 (GND)
unnamed: C13.2, C16.1, D34., M1., U40.3 (VO)
unnamed: C20.2, C21.2, C22.2, U10.
unnamed: C23.2, C25.2, U7.
unnamed: D1.1 (K), J1.1
unnamed: D1.2 (A), D2.2 (A), D3.2 (A), D4.2 (A), D5.2 (A), D6.2 (A), D7.2 (A), J1.8
unnamed: D2.1 (K), J1.6
unnamed: D3.1 (K), J1.2
unnamed: D4.1 (K), J1.5
unnamed: D5.1 (K), J1.3
unnamed: D6.1 (K), J1.4
unnamed: D7.1 (K), J1.7
unnamed: D8.1 (K), J3.6
unnamed: D9.1 (K), J3.5
unnamed: D10.1 (K), J3.1
unnamed: D8.2 (A), D9.2 (A), D10.2 (A), D11.2 (A), D12.2 (A), D13.2 (A), D14.2 (A), J3.8
unnamed: D11.1 (K), J3.7
unnamed: D12.1 (K), J3.4
unnamed: D13.1 (K), J3.2
unnamed: D14.1 (K), J3.3
unnamed: D15.1 (K), J4.6
unnamed: D15.2 (A), D16.2 (A), D17.2 (A), D18.2 (A), D19.2 (A), D20.2 (A), D21.2 (A), J4.8
unnamed: D16.1 (K), J4.5
unnamed: D17.1 (K), J4.1
unnamed: D18.1 (K), J4.7
unnamed: D19.1 (K), J4.4
unnamed: D20.1 (K), J4.2
unnamed: D21.1 (K), J4.3
unnamed: D22.1 (K), J8.6
unnamed: D22.2 (A), D23.2 (A), D24.2 (A), D25.2 (A), D26.2 (A), D27.2 (A), D28.2 (A), J8.8
unnamed: D23.1 (K), J8.5
unnamed: D24.1 (K), J8.1
unnamed: D25.1 (K), J8.7
unnamed: D26.1 (K), J8.4
unnamed: D27.1 (K), J8.2
unnamed: D28.1 (K), J8.3
unnamed: J9.1, U3.16 (O1)
unnamed: J9.2, U3.15 (O2)
unnamed: J9.3, U3.14 (O3)
unnamed: J9.4, U3.13 (O4)
unnamed: U8.5 (GND), U8.6 (GND), U8.7 (GND), U8.8 (GND), U8.9 (GND), U8.10 (GND), U8.11 (GND), U8.12 (GND)
PFET1: 1kΩ.2, U5.16 (O1)
PFET2: 1kΩ.2, U5.15 (O2)
PFET3: 1kΩ.2, U5.14 (O3)
PFET4: 1kΩ.2, U5.13 (O4)
PSU_GND: U4.
P_3V3: PCM1802.
RAD_L: 7.5Ω.1, J51.R, T1.
RAD_R: 7.5Ω.2, J51.T, T1.
S3_3V3: 10kΩ.1, C23.1, C25.1, C28.1, C29.2, C30.2, U7., U11., U89.7 (VDD)
S3_to_A32: U7., U10.
SEG_A_BUS: 200Ω.1, J2.1, J5.1, J6.1, J7.1
SEG_B_BUS: 200Ω.1, J2.2, J5.2, J6.2, J7.2
SEG_C_BUS: 200Ω.1, J2.3, J5.3, J6.3, J7.3
SEG_D_BUS: 200Ω.1, J2.4, J5.4, J6.4, J7.4
SEG_E_BUS: 200Ω.1, J2.5, J5.5, J6.5, J7.5
SEG_F_BUS: 200Ω.1, J2.6, J5.6, J6.6, J7.6
SEG_G_BUS: 200Ω.1, J2.7, J5.7, J6.7, J7.7

Notes on the sheet:
Seg G
Seg E
P-MOSFET DIGIT 1
ANTENNA
STEPPER DRIVER
Seg A
Seg D
RADIO TRANSFO AUDIO OUTPUT
SOME NOTES TIDEDLIDOTES
Seg B
LEDITRON DIGIT 4
DPDT ON-OFF-ON AUDIO SWITCH
LEDITRON DIGIT 1
FQP27P06
LED 2
There are two volume knobs, one is in the back at the amp's analog and the other is at the front, digital only.
PCM1802 ADC
LEDITRON DIGIT 2
AUDIO MCU ESP32-WROOM-32
Seg C
7 SEGMENTS BUS DRIVER
LED 3
AS5600 TUNING POSITION ANALYZER
The faraday cages over the whole of the tube radio and over the AS5600 are both connected to EARTH
USB-C connections from back of box goes to their respective MCU's USB-C connector.
P-MOSFET DIGIT 2
FARADAY CAGE OVER RADIO
IRL540N
TUBE RADIO AUDIO JACK IN INTO PCM1802
BT PAIR BUTTON
5V 0.4W CAGE FAN
The AMP PSU "20V_GND" is shown for completeness only; the actual path goes to the AMP's -20V and +20V inputs.
FRONT PANEL POWER TOGGLE
Where possible and adequate, all cables are twisted pairs, shielded and/or foiled. Representations are in sheet.
LED 1
5VDC PSU
All the grounds are joined at a single starpoint, represented by the JST 2PINS buses
LED 4
PCM5102A DAC
Seg F
COLON
P-MOSFET DIGIT 3
RDA5807M TUNING CALIBRATOR
7 SEGMENTS 24H CLOCK DISPLAY
PANEL RADIO LED PWM CONTROL
VOLUME POT
12V 0.8W BOX FAN
STEPPER LIMIT
To 28BYJ-48
DS3231 RTC
AC PLUG IN
P-MOSFET DIGIT 4
All the "AMP_" prefixes on labels go their respective pins on the small PCB where AUX inputs go.
AMP PSU 20VDC
LEDITRON DIGIT 3
FRNT PNL BT LED
MAIN MCU ESP32-S3 N16R8
P-MOSFET DIGIT DRIVER
