Z3r0shin/ambersong/firmware/include/proto.h

// ============================================================================
//  AMBERSONG  -  INTER-MCU PROTOCOL
//
//  Shared by BOTH firmwares. This file is the contract; if it changes, both
//  sides get rebuilt. Nothing else may define these numbers.
//
//  THE LINK
//    The firmware uses S3 GPIO13 (TX) / GPIO14 (RX) and A32 GPIO26 (RX) /
//    GPIO27 (TX) - pins.h. What joins them is the Hardware Bible's (§2, §3).
//  Serial2 on BOTH sides, and on the A32 it MUST be given explicit pins - its
//  defaults are GPIO16/17, and GPIO17 is the firmware's LRCK. Calling
//  Serial2.begin() bare silently breaks the DAC and surfaces much later as
//  "no audio". See link.h.
//
//  WHY A FRAMED, CHECKSUMMED PROTOCOL AND NOT PRINTF
//  Three reasons, all learned rather than assumed:
//   1. The S3 relays the A32's firmware images over this link. A corrupted
//      byte in an image must be detected, not installed.
//   2. Both MCUs print to their own consoles. A framed link cannot be confused
//      by a stray log line arriving mid-message.
//   3. Version skew is real: the S3 can update the A32, so the two WILL run
//      mismatched builds at some point. A frame of another PROTO_VERSION is
//      dropped by the framer and counted (badVer; the S3 publishes it as
//      `linkver` and on its console), so skew shows as a silent link with a
//      named cause instead of as misread structs.
//
//  FRAME LAYOUT
//    The start pattern is two DIFFERENT bytes, 0xA5 0x5A, so no run of one
//    repeated value (an idle line reads 0xFF) can form it.
//
//    +------+------+-----+------+--------+---------+-------+
//    | 0xA5 | 0x5A | ver | type | len_lo | len_hi  | ...   |
//    +------+------+-----+------+--------+---------+-------+
//    | payload (len bytes) | crc_lo | crc_hi |
//    +---------------------+--------+--------+
//
//    ver..payload inclusive are covered by CRC16-CCITT (poly 0x1021,
//    init 0xFFFF). The start bytes are NOT covered - they are resynchronisation
//    markers, not data.
//
//  ENDIANNESS
//    Both ends are little-endian Xtensa with the same compiler, so packed
//    structs are copied verbatim. That is a deliberate, recorded shortcut. If a
//    third device ever joins this bus, everything here becomes byte-oriented.
//
//  LIVENESS
//    The A32 sends STATE unprompted every 250 ms. The S3 treats >2 s of silence
//    as "A32 missing" and keeps working - the display and needle do not
//    depend on the audio MCU. The A32 is the other way round, by the author's
//    awake rule (2026-09-01): it plays and takes Bluetooth only while the amp
//    is on AND the S3 is talking (serviceWake() in a32/main.cpp). When the S3
//    goes quiet - its own OTA reboot included - the A32 mutes, drops the phone
//    and forgets the amp, and wakes again only when the S3 is back and says
//    the amp is on.
// ============================================================================

#pragma once
#include <stdint.h>
#include <stddef.h>
#include <string.h>

//  2 : ProtoAudio gained fadeInMs / fadeOutMs, and the version was bumped with
//      it. A peer of the other version now has its frames dropped by the
//      framer (badVer) instead of misreading the struct.
//  3, 4 : NOT RECORDED. The value was already 4 in the repository's first
//      commit (2026-09-01), so what changed at 3 and at 4 happened
//      before there was a history to read it from. Written down 2026-09-24 so
//      nobody goes looking for two entries that were never kept.
//  Since then no bump: every struct change has been fields APPENDED to
//  ProtoState - see WHEN PROTO_VERSION CHANGES, under the message types.
#define PROTO_VERSION       4
#define PROTO_SOF0          0xA5
#define PROTO_SOF1          0x5A
#define PROTO_MAX_PAYLOAD   1088     // OTA chunk (1024) + header slack
#define PROTO_BAUD          921600   // line rate only: the acked OTA relay is far
                                     // slower (75.8 s for an A32 image, 2026-08-31)
#define PROTO_STATE_MS      250      // A32 -> S3 unprompted state cadence
#define PROTO_SILENCE_MS    2000     // beyond this, the peer is "missing"

//  Version string format, author's convention: v.X.YYYYMMDDTHHMMSS
#define PROTO_VERSION_LEN   24

// ---------------------------------------------------------------------------
//  MESSAGE TYPES
//  Explicit numbers so a mismatch between builds is diagnosable from a capture
//  rather than from source archaeology. 0x0n handshake, 0x1n S3->A32 control,
//  0x2n A32->S3 reporting, 0x3n OTA relay.
// ---------------------------------------------------------------------------
enum : uint8_t {
  MSG_HELLO         = 0x01,   // S3  -> A32   ProtoHello
  MSG_HELLO_ACK     = 0x02,   // A32 -> S3    ProtoHello
  MSG_PING          = 0x03,   // S3  -> A32   empty       (keeps the A32 awake)
  MSG_PONG          = 0x04,   // A32 -> S3    empty

  MSG_SET_AUDIO     = 0x10,   // S3  -> A32   ProtoAudio
  MSG_SET_BT        = 0x11,   // S3  -> A32   ProtoBtCfg
  MSG_SET_SYS       = 0x12,   // S3  -> A32   ProtoSys
  MSG_SET_TIME      = 0x13,   // S3  -> A32   ProtoTime   (NTP -> DS3231)
  MSG_GET_TIME      = 0x14,   // S3  -> A32   empty
  MSG_BT_FORGET     = 0x15,   // S3  -> A32   empty       (drop all pairings)
  MSG_BT_LOOK       = 0x16,   // S3  -> A32   empty       (open the pairing window,
                              //   BT_LINK - not BT_LOOK - and only on the BT source)
  MSG_REBOOT        = 0x17,   // S3  -> A32   empty
  MSG_CAL_POT       = 0x18,   // S3  -> A32   uint8: 0 = MIN, 1 = MAX, 2 = CENTRE
  MSG_BT_CMD        = 0x19,   // S3  -> A32   uint8: BTC_*  (AVRCP transport)
  MSG_GET_CFG       = 0x1A,   // S3  -> A32   empty       (send me your settings)
  MSG_TEST_DC       = 0x1B,   // S3  -> A32   uint8 0/1   constant-DC diagnostic
  MSG_ADC_CLOCK     = 0x1C,   // RETIRED 2026-09-01. GPIO0's clock feeds the
                              //   DAC as well (Hardware Bible §3), so cutting
                              //   MCLK is a DAC clock error, not a mute. The
                              //   id stays reserved so it is never reused.
  MSG_ZERO_FLOOR    = 0x1D,   // S3  -> A32   uint8 0/1   zero-data floor
  MSG_USE_POT       = 0x1E,   // S3  -> A32   uint8 0/1   pot drives volume

  //  0x4n : S3 -> A32 DIAGNOSTICS, a new block because the 0x1n control block
  //  had only 0x1F left. An earlier version of these put SD_DELAY at 0x20, which is
  //  MSG_STATE. It would have worked - STATE only ever travels A32 -> S3 and
  //  these only ever travel S3 -> A32, so no switch would have seen both - and
  //  that is exactly the kind of "correct by luck" this file exists to refuse.
  //  0x1C stays retired and unreused, as its own comment demands.
  MSG_DIN_DRIVE     = 0x40,   // S3  -> A32   uint8 0..3  DIN pad drive
  //  MSG_SD_DELAY RETIRED 2026-09-11, the day after it was added. It was a
  //  remote, unguarded write to tx_sd_out_delay, and that register sent the radio
  //  to FULL VOLUME: of its four positions only 0 plays correctly. It was ruled
  //  unsafe to ship a build that still carried it.
  //  The id stays reserved and is never reused, like MSG_ADC_CLOCK above.
  MSG_SD_DELAY      = 0x41,   // RETIRED. Nothing sends it; the A32 ignores it.
  MSG_SIGN_TAIL     = 0x42,   // S3  -> A32   uint8 0/1   sign-extended tail
  MSG_CLK_DRIVE     = 0x43,   // S3  -> A32   uint8 2..3  clock-pin drive
  MSG_DC_WORD       = 0x44,   // S3  -> A32   uint8 0..6  INDEX into kDc (a32/main.cpp),
                              //   never a raw word: the remote path can only pick
                              //   one of seven fixed words, all <= -42 dBFS
  MSG_BT_TX         = 0x45,   // S3  -> A32   uint8 0..5  BR/EDR max TX power
                              //   level (ESP_PWR_LVL_N12..P3). DOWN only: P3 is
                              //   the controller's own default maximum.
  MSG_CLK_PAIR      = 0x46,   // S3  -> A32   uint8[2]: MCLK drive, then BCK/LRCK
                              //   drive, each clamped 2..3. Written 2026-09-13,
                              //   when drive 3 on all three pads was heard to
                              //   distort the radio path, to set MCLK and the
                              //   frame pair apart. Boot sets all three to 3
                              //   (audio.cpp).

  //  WHEN PROTO_VERSION CHANGES - one rule, and it is what the repository's
  //  history did (v2, before the first commit, bumped for a size change).
  //   - A new MESSAGE ID: no bump. An older peer ignores an id it does not know.
  //   - A struct that changes SIZE: no bump. ProtoFramer::as() refuses a
  //     payload of the wrong length, so a mismatched peer loses only that
  //     message type, and the link itself stays up. Every struct change since
  //     the first commit has been fields APPENDED to ProtoState this way; a
  //     half-updated pair loses telemetry and keeps its audio. (ProtoOtaData
  //     is read at fixed offsets, not with as() - its layout is pinned by the
  //     static_asserts below the payloads.)
  //   - A change as() CANNOT see - same size, different layout or meaning:
  //     bump. Know the cost first: every frame of the other version is dropped
  //     (badVer), so the A32 sleeps by the awake rule until both boards run the
  //     new version. Update the A32 first, through the S3 while they still
  //     match; then the S3 over its own WiFi.

  MSG_STATE         = 0x20,   // A32 -> S3    ProtoState  (unprompted, 250 ms)
  MSG_TIME          = 0x21,   // A32 -> S3    ProtoTime
  MSG_LOG           = 0x22,   // A32 -> S3    char[]      (S3 console: "[A32] ...")
  MSG_CFG           = 0x23,   // A32 -> S3    ProtoCfgAll (reply to MSG_GET_CFG)
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
